SpgV0/femmx/manual_qt/images/dlg_materials_library.png

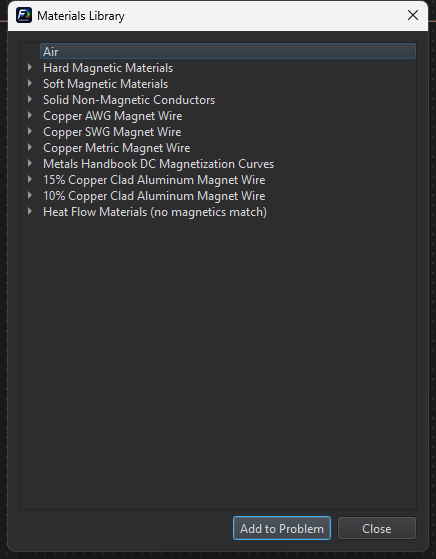
manual_qt/images/dlg_materials_library.png
