SpgV0/femmx/manual_qt/images/dlg_materials_list.png

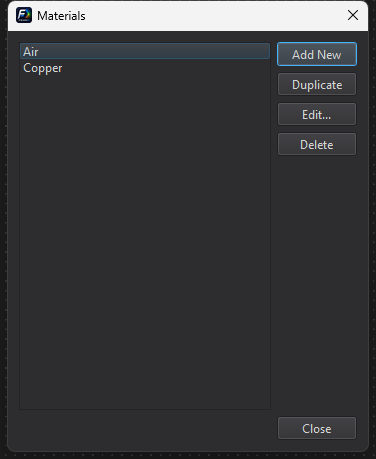
manual_qt/images/dlg_materials_list.png
