SpgV0/femmx/manual_qt/images/dlg_add_arc_prompt.png

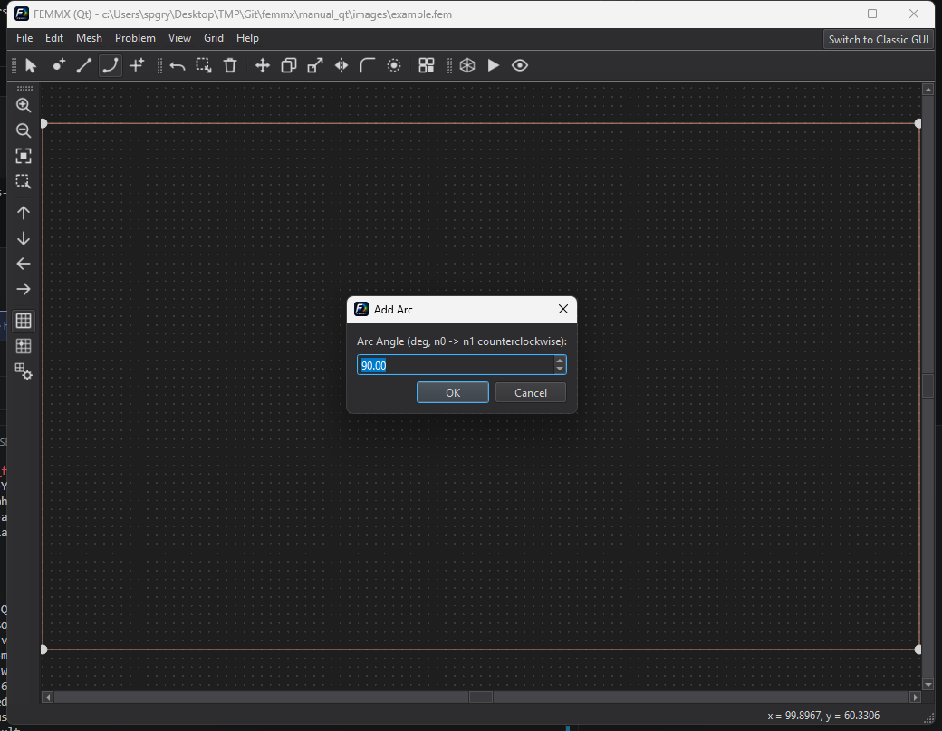
manual_qt/images/dlg_add_arc_prompt.png
