SpgV0/femmx/manual_qt/images/dlg_circuit_edit.png

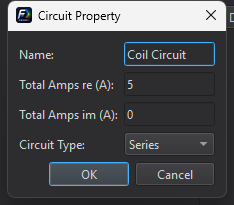
manual_qt/images/dlg_circuit_edit.png
