SpgV0/femmx/manual_qt/images/dlg_exterior_region.png

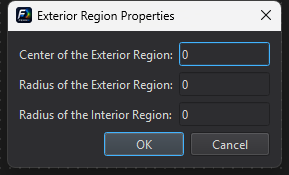
manual_qt/images/dlg_exterior_region.png
