SpgV0/femmx/manual_qt/images/dlg_heat_boundary_edit_filled.png

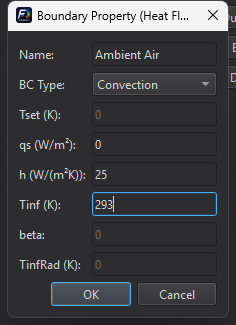
manual_qt/images/dlg_heat_boundary_edit_filled.png
