SpgV0/femmx/manual_qt/images/dlg_heat_boundary_list.png

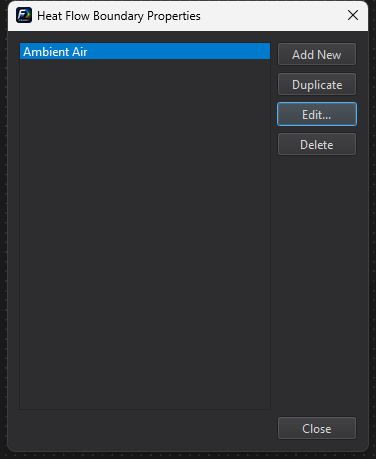
manual_qt/images/dlg_heat_boundary_list.png
