SpgV0/femmx/manual_qt/images/dlg_heat_point_edit.png

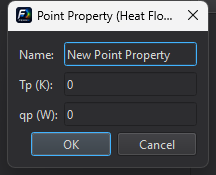
manual_qt/images/dlg_heat_point_edit.png
