SpgV0/femmx/manual_qt/images/dlg_node_props.png

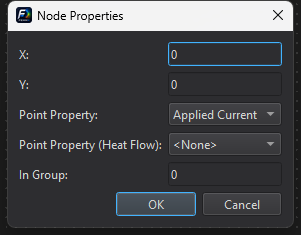
manual_qt/images/dlg_node_props.png
