SpgV0/femmx/manual_qt/images/dlg_pointprop_edit.png

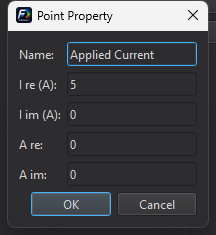
manual_qt/images/dlg_pointprop_edit.png
