SpgV0/femmx/manual_qt/images/menu_grid.png

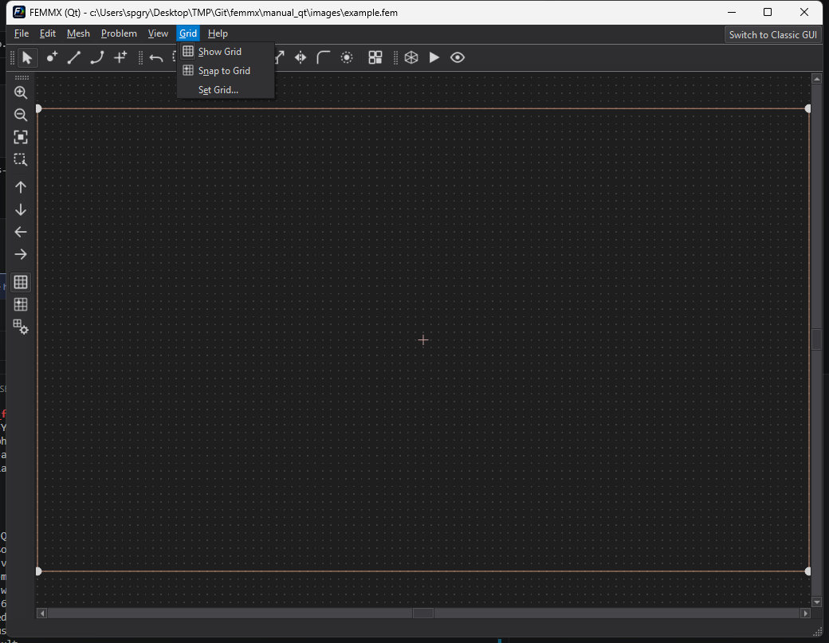
manual_qt/images/menu_grid.png
