SpgV0/femmx/manual_qt/images/menu_view.png

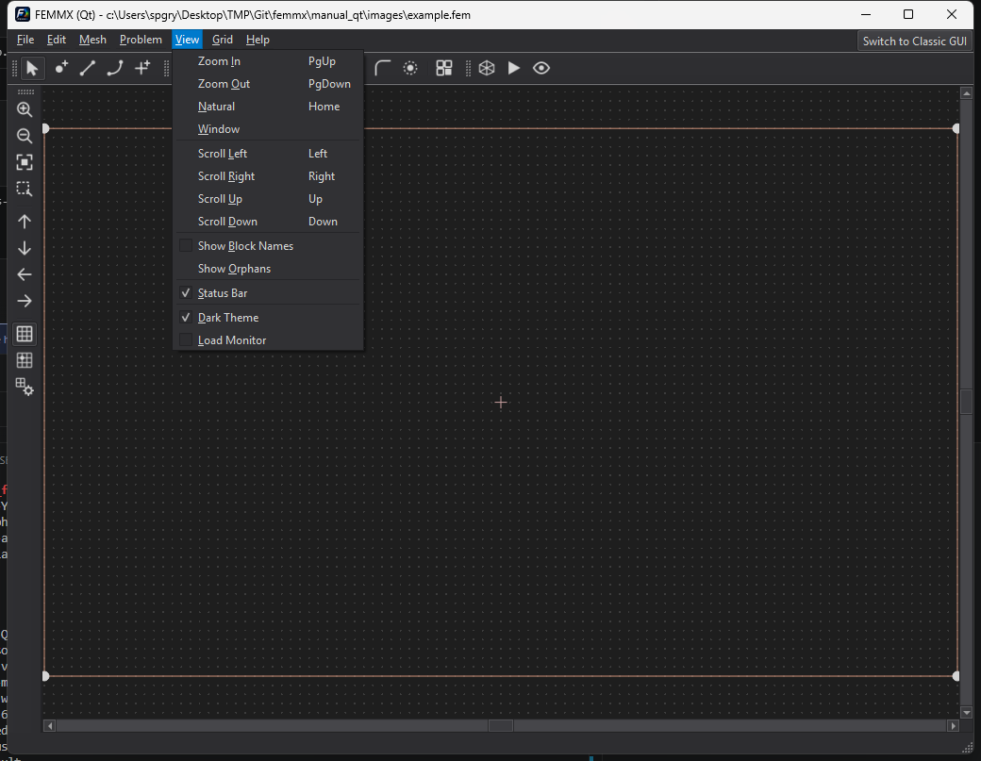
manual_qt/images/menu_view.png
