SpgV0/femmx/manual_qt/images/sv_menu_file.png

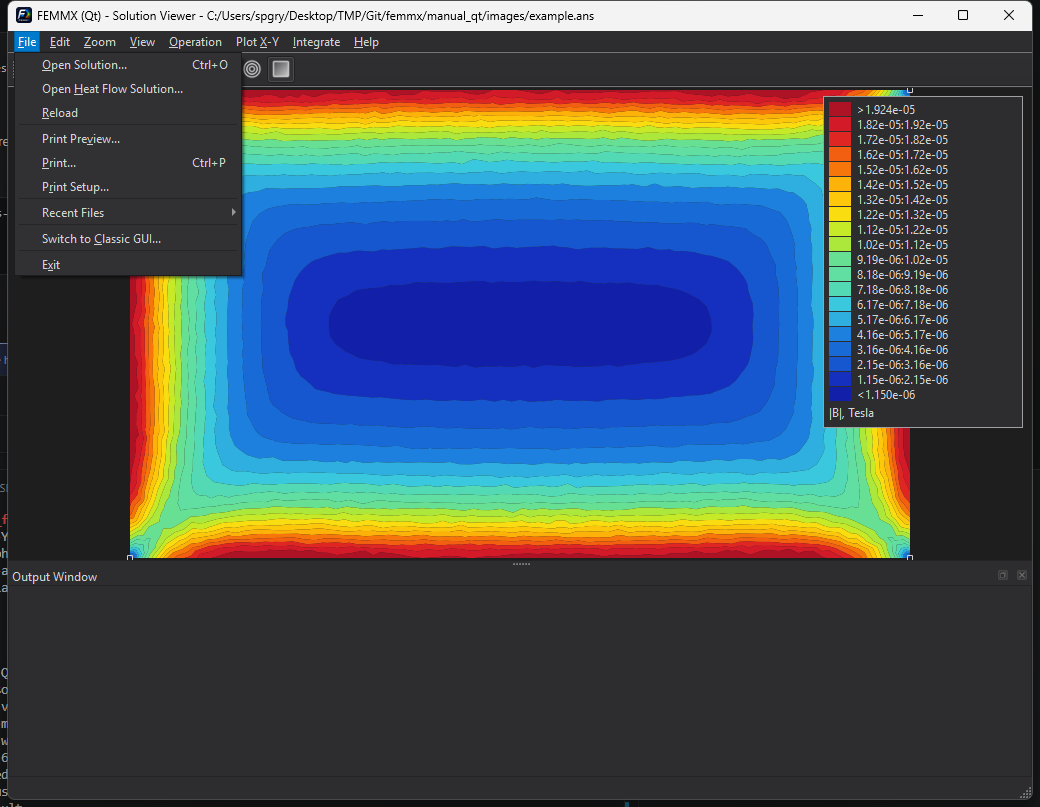
manual_qt/images/sv_menu_file.png
