SpgV0/femmx/manual_qt/images/sv_menu_operation.png

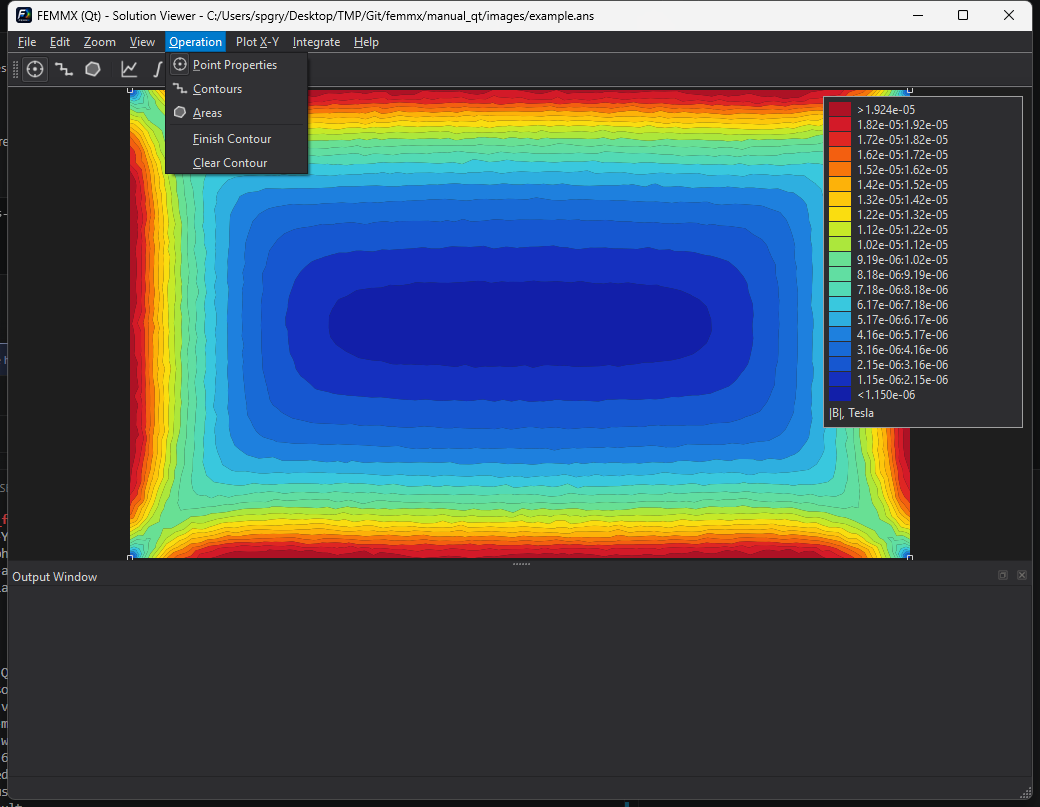
manual_qt/images/sv_menu_operation.png
