SpgV0/femmx/manual_qt/images/sv_plotxy_chart2.png

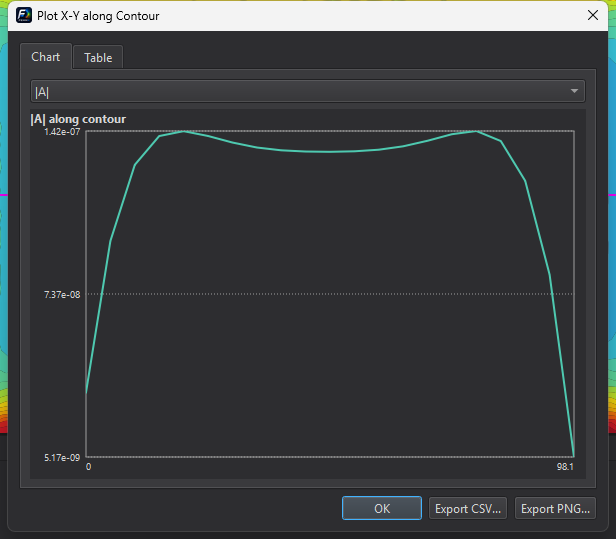
manual_qt/images/sv_plotxy_chart2.png
