SpgV0/femmx/manual_qt/images/view_loadmonitor_check.png

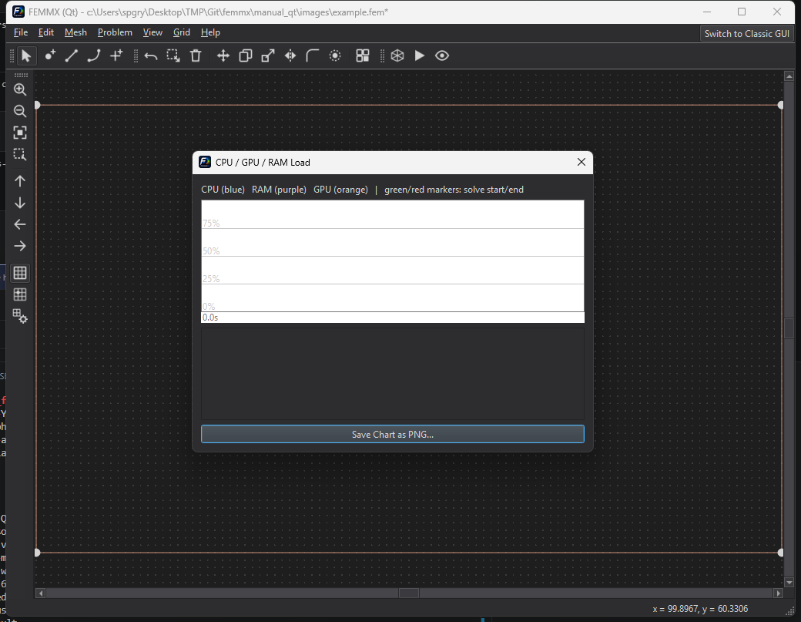
manual_qt/images/view_loadmonitor_check.png
