SpgV0/femmx/test/fixtures/render/golden/contour.png

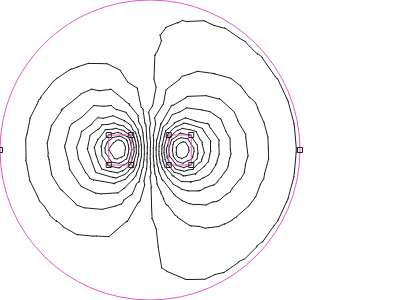
test/fixtures/render/golden/contour.png
