SpgV0/femmx/test/fixtures/render/golden/crop_density.png

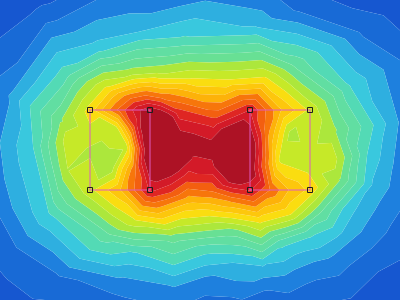
test/fixtures/render/golden/crop_density.png
