SpgV0/femmx/test/fixtures/render/golden/density.png

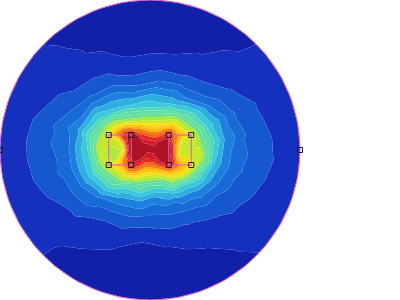
test/fixtures/render/golden/density.png
