SpgV0/femmx/test/fixtures/render/golden/geometry.png

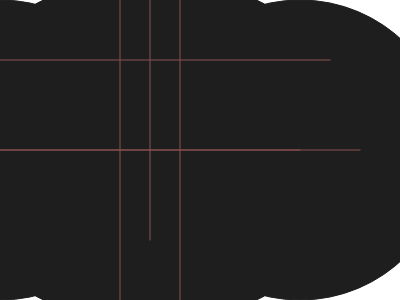
test/fixtures/render/golden/geometry.png
