SpgV0/femmx/manual_qt/images/dlg_problem_properties.png

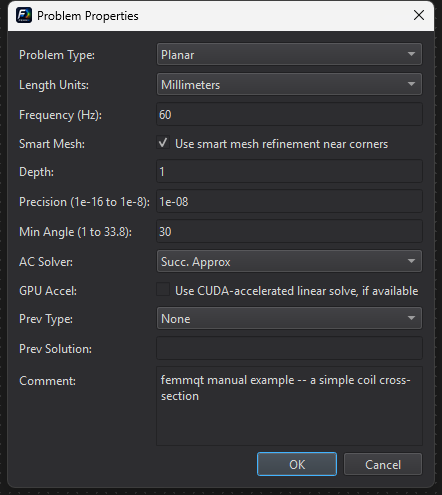
manual_qt/images/dlg_problem_properties.png
