SpgV0/femmx/femmqt/MainWindow.cpp

#define _USE_MATH_DEFINES

#include "MainWindow.h"

#include "AnsFileIO.h"
#include "AppPreferences.h"
#include "AppTheme.h"
#include "ArcPropDialog.h"
#include "BlockLabelPropDialog.h"
#include "BoundaryPropDialog.h"
#include "CircuitPropDialog.h"
#include "ConstraintListDialog.h"
#include "ConstraintSolver.h"
#include "DxfIO.h"
#include "ExteriorRegionDialog.h"
#include "FemmFileIO.h"
#include "FemmProblemEdit.h"
#include "FemxFileIO.h"
#include "SketchFileIO.h"
#include "GuiSwitch.h"
#include "HoverTooltip.h"
#include "IconTheme.h"
#include "LoadMonitorDialog.h"
#include "MaterialLibraryDialog.h"
#include "MaterialPropDialog.h"
#include "MeshOverlay.h"
#include "MoveCopyDialog.h"
#include "NodePropDialog.h"
#include "ConstructionGeometry.h"
#include "OffsetChamfer.h"
#include "ProblemFileIO.h"
#include "ProblemKind.h"
#include "OpenBoundaryDialog.h"
#include "PointPropDialog.h"
#include "PreferencesDialog.h"
#include "ProblemPropertiesDialog.h"
#include "PropertyEditDialog.h"
#include "PropertyFields.h"
#include "PropertyListDialog.h"
#include "SegmentPropDialog.h"
#include "SolutionView.h"
#include "SolveRunner.h"

#include <QActionGroup>
#include <QApplication>
#include <QClipboard>
#include <QCloseEvent>
#include <QComboBox>
#include <QDesktopServices>
#include <QDialog>
#include <QDialogButtonBox>
#include <QDoubleValidator>
#include <QFile>
#include <QFileDialog>
#include <QFileInfo>
#include <QFormLayout>
#include <QGraphicsView>
#include <QInputDialog>
#include <QLabel>
#include <QLineEdit>
#include <QMenuBar>
#include <QMessageBox>

#include "DemoBrowserDialog.h"
#include "DemoLibrary.h"
#include "Notify.h"
#include "WindowTitle.h"
#include <QPageSetupDialog>
#include <QPainter>
#include <QPlainTextEdit>
#include <QPrintDialog>
#include <QPrintPreviewDialog>
#include <QPrinter>
#include <QPushButton>
#include <QScrollArea>
#include <QScrollBar>
#include <QSet>
#include <QSettings>
#include <QSpinBox>
#include <QStatusBar>
#include <QToolBar>
#include <QUrl>
#include <QVBoxLayout>

#include <cmath>

namespace {
// Generates "New <Base>"/"<Base> Copy", disambiguated with a trailing
// " (2)", " (3)", ... against whatever names are already in `list` --
// shared by the Add New / Duplicate callbacks below for all four
// property lists (they're otherwise unrelated struct types, but all
// start with a QString `name` member, so this only needs to be a small
// template rather than four near-identical copies).
template <typename T>
QString uniqueName(const QVector<T>& list, const QString& base)
{
  QSet<QString> existing;
  for (const T& item : list)
    existing.insert(item.name);
  if (!existing.contains(base))
    return base;
  for (int n = 2;; n++) {
    QString candidate = QString("%1 (%2)").arg(base).arg(n);
    if (!existing.contains(candidate))
      return candidate;
  }
}

// Modified by Claude (Anthropic), noreply@anthropic.com: human-readable
// label for ConstraintListDialog -- names the type plus the node indices
// it touches, via ConstraintSolver::touchedNodes (the same node set the
// solver itself scopes its unknowns to -- see that function's own
// comment), rather than duplicating each type's own refA/refB/refC field
// semantics here.
QString constraintTypeName(ConstraintType type)
{
  switch (type) {
  case ConstraintType::Coincident: return "Coincident";
  case ConstraintType::Horizontal: return "Horizontal";
  case ConstraintType::Vertical: return "Vertical";
  case ConstraintType::Parallel: return "Parallel";
  case ConstraintType::Perpendicular: return "Perpendicular";
  case ConstraintType::Equal: return "Equal";
  case ConstraintType::Tangent: return "Tangent";
  case ConstraintType::Concentric: return "Concentric";
  case ConstraintType::Symmetric: return "Symmetric";
  }
  return "?";
}

QString describeConstraint(const FemmProblem& p, const FemmConstraint& c)
{
  const QVector<int> nodes = ConstraintSolver::touchedNodes(p, c);
  QStringList nodeStrs;
  for (int n : nodes)
    nodeStrs << QString::number(n);
  return QString("%1 (nodes %2)").arg(constraintTypeName(c.type)).arg(nodeStrs.join(", "));
}

// Matches ProblemPropertiesDialog.cpp's m_lengthUnits combo text exactly
// (same enum order), reused here so the Set Grid dialog's units label
// reads the same word the user already picked in Problem Properties.
QString lengthUnitsName(FemmLengthUnits u)
{
  switch (u) {
  case FemmLengthUnits::Inches: return "Inches";
  case FemmLengthUnits::Millimeters: return "Millimeters";
  case FemmLengthUnits::Centimeters: return "Centimeters";
  case FemmLengthUnits::Meters: return "Meters";
  case FemmLengthUnits::Mils: return "Mils";
  case FemmLengthUnits::Microns: return "Microns";
  }
  return QString();
}

// Per direct user request: right after a freshly-opened file's initial
// Natural/fit-to-view zoom, pick a grid spacing so roughly 20 squares
// span the x axis, snapped to a "nice" whole-number step (1/2/5 x a
// power of ten -- the same progression axis tick marks conventionally
// use) rather than an arbitrary fraction. Takes the ACTUAL visible scene
// width, not the raw model bounding box -- for anything other than a
// model whose own aspect ratio matches the viewport's, fitInViewSafe's
// Qt::KeepAspectRatio padding means more of the x axis is visible than
// just the model's own width (confirmed live: a 50x200mm model in a
// ~985x730px window shows ~295mm of scene width, not 50mm -- using the
// model's width alone would have produced a ~150-square-wide grid, not
// ~20). Callers pass view->mapToScene(view->viewport()->rect()).
// boundingRect(), taken AFTER fitInViewSafe so it reflects what actually
// ended up on screen. Bottoms out at 1 (a true integer, per the original
// request this was built for) for any view whose width is itself under
// ~20 units -- a sub-1 step would technically hit the "~20 squares"
// target more precisely there, but wouldn't be a whole number anymore.
double niceIntegerGridSize(const QRectF& visibleBounds)
{
  double extent = visibleBounds.width();
  if (extent <= 0)
    return 1.0;
  double target = extent / 20.0;
  if (target < 1.0)
    return 1.0;
  double magnitude = std::pow(10.0, std::floor(std::log10(target)));
  double normalized = target / magnitude;
  double nice;
  if (normalized < 1.5)
    nice = 1;
  else if (normalized < 3.5)
    nice = 2;
  else if (normalized < 7.5)
    nice = 5;
  else
    nice = 10;
  return nice * magnitude;
}
}

MainWindow::MainWindow(QWidget* parent)
    : QMainWindow(parent)
{
  resize(1024, 768);

  m_scene = new GeometryScene(this);
  m_scene->setProblem(&m_problem);
  // #28: honour the saved per-type snap choices from the first window
  // onwards, not just after Preferences has been opened once.
  m_scene->setSnapFlags(AppPreferences::load().snapFlags);
  connect(m_scene, &GeometryScene::problemEdited, this, &MainWindow::onProblemEdited);
  connect(m_scene, &GeometryScene::entityDoubleClicked, this, &MainWindow::onEntityDoubleClicked);
  connect(m_scene, &GeometryScene::openSelectedRequested, this, &MainWindow::onOpenSelectedTriggered);
  connect(m_scene, &GeometryScene::zoomWindowSelected, this, &MainWindow::onZoomWindowSelected);
  connect(m_scene, &GeometryScene::selectByCircleCompleted, this, [this]() { m_selectToolAction->setChecked(true); });
  connect(m_scene, &GeometryScene::aboutToEdit, this, &MainWindow::snapshotForUndo);

  m_view = new GeometryView(m_scene, this);
  m_view->setRenderHint(QPainter::Antialiasing);
  m_view->setDragMode(QGraphicsView::RubberBandDrag);
  // FEMM's geometry files use a math (y-up) convention, matching how
  // femmx.exe itself draws (see FemmeView.cpp's DwgToScreen, which flips
  // y explicitly for GDI's y-down screen space) -- flip the view instead
  // of the data, so GeometryScene's coordinates can stay exactly what's
  // in the .fem file with no transform bookkeeping of its own.
  m_view->scale(1, -1);
  setCentralWidget(m_view);
  connect(m_view, &GeometryView::enterPointRequested, this, &MainWindow::onEnterPointTriggered);

  QMenu* fileMenu = menuBar()->addMenu("&File");
  fileMenu->addAction("&New", this, &MainWindow::onNewTriggered, QKeySequence::New);
  fileMenu->addAction("&Open...", this, &MainWindow::onOpenTriggered, QKeySequence::Open);
  fileMenu->addAction("&Save", this, &MainWindow::onSaveTriggered, QKeySequence::Save);
  fileMenu->addAction("Save &As...", this, &MainWindow::onSaveAsTriggered, QKeySequence::SaveAs);
  fileMenu->addSeparator();
  fileMenu->addAction("&Import DXF...", this, &MainWindow::onImportDxfTriggered);
  fileMenu->addAction("&Export DXF...", this, &MainWindow::onExportDxfTriggered);
  fileMenu->addSeparator();
  fileMenu->addAction("Print Pre&view...", this, &MainWindow::onPrintPreviewTriggered);
  fileMenu->addAction("&Print...", this, &MainWindow::onPrintTriggered, QKeySequence::Print);
  fileMenu->addAction("P&rint Setup...", this, &MainWindow::onPrintSetupTriggered);
  fileMenu->addSeparator();
  // Issue #90: the shipped demo library. Disabled rather than hidden
  // when there is none, so a build without the corpus says why instead
  // of quietly having one fewer menu item -- and disabled rather than
  // reporting: a missing demo library is not something the user did,
  // and an error dialog at startup would be a modal on a path that may
  // have no desktop (#85).
  m_demoModelsAction = fileMenu->addAction("&Demo Models...", this,
      &MainWindow::onDemoModelsTriggered);
  {
    QString demoError;
    const int count = DemoLibrary::load(demoError).size();
    if (count == 0) {
      m_demoModelsAction->setEnabled(false);
      m_demoModelsAction->setToolTip(
          QStringLiteral("No demo models are installed: %1").arg(demoError));
    } else {
      m_demoModelsAction->setToolTip(
          QStringLiteral("%1 worked examples, each with a closed-form answer to "
                         "check against").arg(count));
    }
  }
  fileMenu->addSeparator();
  m_recentFilesMenu = fileMenu->addMenu("Recent Files");
  fileMenu->addSeparator();
  fileMenu->addAction("Switch to &Classic GUI...", this, &MainWindow::onSwitchToClassicTriggered);
  fileMenu->addSeparator();
  fileMenu->addAction("E&xit", this, &QWidget::close);

  // Matches femm.rc's IDR_FEMMETYPE Edit menu.
  QMenu* editMenu = menuBar()->addMenu("&Edit");
  editMenu->addAction("&Undo", this, &MainWindow::onUndoTriggered, QKeySequence::Undo);
  editMenu->addAction("&Open Selected", this, &MainWindow::onOpenSelectedTriggered);
  editMenu->addAction("&Delete", this, &MainWindow::onDeleteSelectedTriggered, QKeySequence::Delete);
  editMenu->addSeparator();
  editMenu->addAction("&Move...", this, &MainWindow::onMoveSelectedTriggered);
  editMenu->addAction("&Copy...", this, &MainWindow::onCopySelectedTriggered);
  editMenu->addAction("Sc&ale...", this, &MainWindow::onScaleSelectedTriggered);
  editMenu->addAction("M&irror...", this, &MainWindow::onMirrorSelectedTriggered);
  editMenu->addSeparator();
  editMenu->addAction("Create &Radius...", this, &MainWindow::onCreateRadiusTriggered);
  editMenu->addAction("Create &Open Boundary...", this, &MainWindow::onCreateOpenBoundaryTriggered);
  editMenu->addSeparator();
  editMenu->addAction("Copy as &Bitmap", this, &MainWindow::onCopyBitmapTriggered);
  editMenu->addSeparator();
  // Simplified, instant-action equivalent of femm.rc's "Operation > Group"
  // mode (which requires switching modes, then pressing Tab to prompt for
  // a group number) -- same underlying inGroup field, just two direct
  // commands instead of a persistent tool mode.
  editMenu->addAction("Select by &Group...", this, &MainWindow::onSelectByGroupTriggered);
  editMenu->addAction("Set &Group...", this, &MainWindow::onSetGroupTriggered);
  editMenu->addSeparator();
  editMenu->addAction("&Preferences...", this, &MainWindow::onPreferencesTriggered);

  // Modified by Claude (Anthropic), noreply@anthropic.com: menu-based
  // access to the drawing tools -- per direct user request ("I want a
  // tools tab for the drawing tools similar to constraints tab"). Until
  // now these existed ONLY as Draw-toolbar buttons with no menu entry
  // (see the toolbar-construction code below, where the still-checkable
  // QActions actually get created). Populated a bit further down, once
  // those QActions exist -- reuses the exact same QAction objects
  // (already checkable, already in the shared `toolGroup` QActionGroup)
  // rather than duplicating them, so a menu selection and a toolbar
  // click stay in sync for free, with no extra wiring.
  QMenu* toolsMenu = menuBar()->addMenu("&Tools");

  // Modified by Claude (Anthropic), noreply@anthropic.com: CAD-style
  // geometric constraints -- per direct user request ("add dimensions
  // when drawings and constraints similar to modern cad"). No classic
  // FEMM precedent (see FemmProblem.h's FemmConstraint comment) -- select
  // the entities a constraint type needs first (same selection mechanism
  // as Move/Copy/Scale/Mirror above), then apply it here.
  QMenu* constraintsMenu = menuBar()->addMenu("&Constraints");
  constraintsMenu->addAction("&Coincident", this, &MainWindow::onCoincidentConstraintTriggered);
  constraintsMenu->addAction("&Horizontal", this, &MainWindow::onHorizontalConstraintTriggered);
  constraintsMenu->addAction("&Vertical", this, &MainWindow::onVerticalConstraintTriggered);
  constraintsMenu->addAction("&Parallel", this, &MainWindow::onParallelConstraintTriggered);
  constraintsMenu->addAction("Perpe&ndicular", this, &MainWindow::onPerpendicularConstraintTriggered);
  constraintsMenu->addAction("&Equal", this, &MainWindow::onEqualConstraintTriggered);
  constraintsMenu->addAction("&Tangent", this, &MainWindow::onTangentConstraintTriggered);
  constraintsMenu->addAction("Co&ncentric", this, &MainWindow::onConcentricConstraintTriggered);
  constraintsMenu->addAction("&Symmetric", this, &MainWindow::onSymmetricConstraintTriggered);
  constraintsMenu->addSeparator();
  constraintsMenu->addAction("&Solve Constraints", this, &MainWindow::onSolveConstraintsTriggered);
  constraintsMenu->addAction("Constraint &List...", this, &MainWindow::onConstraintListTriggered);
  constraintsMenu->addSeparator();
  constraintsMenu->addAction("Clear All Constraints", this, &MainWindow::onClearConstraintsTriggered);
  constraintsMenu->addAction("Clear All Dimensions", this, &MainWindow::onClearDimensionsTriggered);

  // Matches femm.rc's separate Mesh (Create/Show/Purge) and Analysis
  // (Analyze/View Results) menus, just combined under one "Mesh" menu
  // rather than two -- Create Mesh alone (no solve) lets a mesh be
  // inspected/refined before committing to a full Solve.
  QMenu* meshMenu = menuBar()->addMenu("&Mesh");
  meshMenu->addAction("&Create Mesh", this, &MainWindow::onCreateMeshTriggered);
  m_showMeshAction = meshMenu->addAction("&Show Mesh");
  m_showMeshAction->setCheckable(true);
  connect(m_showMeshAction, &QAction::toggled, m_scene, &GeometryScene::setShowMesh);
  meshMenu->addAction("&Purge Mesh", this, &MainWindow::onPurgeMeshTriggered);
  meshMenu->addSeparator();
  meshMenu->addAction("&Solve", this, &MainWindow::onSolveTriggered, QKeySequence("Ctrl+L"));
  meshMenu->addAction("&View Results...", this, &MainWindow::onViewResultsTriggered);

  QMenu* problemMenu = menuBar()->addMenu("&Problem");
  problemMenu->addAction("&Problem Properties...", this, &MainWindow::onProblemPropertiesTriggered);
  problemMenu->addAction("&Exterior Region...", this, &MainWindow::onExteriorRegionTriggered);
  problemMenu->addSeparator();
  problemMenu->addAction("&Materials...", this, &MainWindow::onMaterialsTriggered);
  problemMenu->addAction("Materials &Library...", this, &MainWindow::onMaterialsLibraryTriggered);
  problemMenu->addAction("&Boundary Properties...", this, &MainWindow::onBoundaryPropsTriggered);
  problemMenu->addAction("&Circuits...", this, &MainWindow::onCircuitsTriggered);
  problemMenu->addAction("Poi&nt Properties...", this, &MainWindow::onPointPropsTriggered);

  // Matches femm.rc's IDR_FEMMETYPE View menu (Zoom/Pan/Show Block Names
  // subset), plus Dark Theme and the Load Monitor -- Lua Console is a
  // separate todo item (see the plan's scope note on it).
  QMenu* viewMenu = menuBar()->addMenu("&View");
  viewMenu->addAction("Zoom &In", this, &MainWindow::onZoomIn, QKeySequence(Qt::Key_PageUp));
  viewMenu->addAction("Zoom &Out", this, &MainWindow::onZoomOut, QKeySequence(Qt::Key_PageDown));
  viewMenu->addAction("&Natural", this, &MainWindow::onZoomNatural, QKeySequence(Qt::Key_Home));
  viewMenu->addAction("&Window", this, &MainWindow::onZoomWindowTriggered);
  viewMenu->addAction("&Keyboard", this, &MainWindow::onKbdZoomTriggered);
  viewMenu->addSeparator();
  viewMenu->addAction("Scroll &Left", this, &MainWindow::onPanLeft, QKeySequence(Qt::Key_Left));
  viewMenu->addAction("Scroll &Right", this, &MainWindow::onPanRight, QKeySequence(Qt::Key_Right));
  viewMenu->addAction("Scroll &Up", this, &MainWindow::onPanUp, QKeySequence(Qt::Key_Up));
  viewMenu->addAction("Scroll &Down", this, &MainWindow::onPanDown, QKeySequence(Qt::Key_Down));
  viewMenu->addSeparator();
  QAction* showNamesAction = viewMenu->addAction("Show &Block Names");
  showNamesAction->setCheckable(true);
  connect(showNamesAction, &QAction::toggled, m_scene, &GeometryScene::setShowBlockNames);
  viewMenu->addAction("Show &Orphans", this, &MainWindow::onShowOrphansTriggered);
  viewMenu->addSeparator();
  QAction* statusBarAction = viewMenu->addAction("&Status Bar");
  statusBarAction->setCheckable(true);
  statusBarAction->setChecked(true);
  connect(statusBarAction, &QAction::toggled, statusBar(), &QStatusBar::setVisible);
  viewMenu->addSeparator();
  QAction* darkThemeAction = viewMenu->addAction("&Dark Theme");
  darkThemeAction->setCheckable(true);
  darkThemeAction->setChecked(AppTheme::isDark());
  connect(darkThemeAction, &QAction::toggled, this, &MainWindow::onDarkThemeToggled);
  QAction* loadMonitorAction = viewMenu->addAction("&Load Monitor");
  loadMonitorAction->setCheckable(true);
  connect(loadMonitorAction, &QAction::toggled, this, &MainWindow::onLoadMonitorToggled);

  QMenu* gridMenu = menuBar()->addMenu("&Grid");
  QAction* showGridAction = gridMenu->addAction("&Show Grid");
  showGridAction->setCheckable(true);
  showGridAction->setChecked(m_scene->showGrid());
  connect(showGridAction, &QAction::toggled, m_scene, &GeometryScene::setShowGrid);
  QAction* snapGridAction = gridMenu->addAction("S&nap to Grid");
  snapGridAction->setCheckable(true);
  snapGridAction->setChecked(m_scene->snapToGrid());
  connect(snapGridAction, &QAction::toggled, m_scene, &GeometryScene::setSnapToGrid);
  gridMenu->addAction("S&et Grid...", this, &MainWindow::onSetGridTriggered);

  QMenu* helpMenu = menuBar()->addMenu("&Help");
  helpMenu->addAction("&Help Topics", this, &MainWindow::onHelpTopicsTriggered);
  helpMenu->addAction("&Keyboard Shortcuts...", this, &MainWindow::onKeyboardShortcutsTriggered);
  helpMenu->addSeparator();
  helpMenu->addAction("&License", this, &MainWindow::onLicenseTriggered);
  helpMenu->addAction("&About FEMMX...", this, &MainWindow::onAboutTriggered);

  // Distinct, always-visible button for jumping back to the classic MFC
  // GUI, per direct user request -- the toolbars above are deliberately
  // icon-only (see their own comment), so "Switch to Classic GUI" living
  // only as a File-menu item was easy to miss. Pinned to the menu bar's
  // corner so it stays visible regardless of window size, not swallowed
  // into an overflow chevron the way a toolbar button could be.
  auto* switchToClassicButton = new QPushButton("Switch to Classic GUI", this);
  switchToClassicButton->setToolTip("Close this file here and reopen it in the original FEMM interface");
  connect(switchToClassicButton, &QPushButton::clicked, this, &MainWindow::onSwitchToClassicTriggered);
  menuBar()->setCornerWidget(switchToClassicButton, Qt::TopRightCorner);

  updateRecentFilesMenu();

  QToolBar* toolBar = addToolBar("Draw");
  // Icon-only, matching a modern CAD-style toolbar -- each action keeps
  // its descriptive text (set below) as a tooltip and for the
  // accessibility/menu fallback, it just isn't painted next to the icon.
  toolBar->setToolButtonStyle(Qt::ToolButtonIconOnly);
  toolBar->setIconSize(QSize(20, 20));
  auto* toolGroup = new QActionGroup(this);
  toolGroup->setExclusive(true);

  m_selectToolAction = addThemedToolAction(toolBar, ":/icons/select.svg", "Select");
  m_selectToolAction->setToolTip("Select -- click or rubber-band-select existing geometry to edit it");
  m_selectToolAction->setCheckable(true);
  m_selectToolAction->setChecked(true);
  toolGroup->addAction(m_selectToolAction);
  connect(m_selectToolAction, &QAction::triggered, this, [this]() { m_scene->setToolMode(GeometryToolMode::Select); });

  m_addNodeToolAction = addThemedToolAction(toolBar, ":/icons/add_node.svg", "Add Node");
  m_addNodeToolAction->setToolTip("Add Node -- click to place a new node");
  m_addNodeToolAction->setCheckable(true);
  // Single-key tool shortcut, per direct user request for CAD-style
  // keys ("n for node, l for line, c for circle, r for rectangle").
  // setShortcut, not just a menu mnemonic, so the bare key works
  // whenever the canvas has focus. Matches the Smart Dimension "D"
  // precedent below; none of these collide with an existing binding.
  m_addNodeToolAction->setShortcut(QKeySequence(Qt::Key_N));
  toolGroup->addAction(m_addNodeToolAction);
  connect(m_addNodeToolAction, &QAction::triggered, this, [this]() { m_scene->setToolMode(GeometryToolMode::AddNode); });

  m_addSegmentToolAction = addThemedToolAction(toolBar, ":/icons/add_segment.svg", "Add Segment");
  m_addSegmentToolAction->setToolTip("Add Segment -- click two nodes to connect them with a straight line");
  m_addSegmentToolAction->setCheckable(true);
  // Single-key tool shortcut, per direct user request for CAD-style
  // keys ("n for node, l for line, c for circle, r for rectangle").
  // setShortcut, not just a menu mnemonic, so the bare key works
  // whenever the canvas has focus. Matches the Smart Dimension "D"
  // precedent below; none of these collide with an existing binding.
  m_addSegmentToolAction->setShortcut(QKeySequence(Qt::Key_L));
  toolGroup->addAction(m_addSegmentToolAction);
  connect(m_addSegmentToolAction, &QAction::triggered, this, [this]() { m_scene->setToolMode(GeometryToolMode::AddSegment); });

  m_addArcToolAction = addThemedToolAction(toolBar, ":/icons/add_arc.svg", "Add Arc");
  m_addArcToolAction->setToolTip("Add Arc -- click two nodes to connect them with a circular arc");
  m_addArcToolAction->setCheckable(true);
  // Single-key tool shortcut, per direct user request for CAD-style
  // keys ("n for node, l for line, c for circle, r for rectangle").
  // setShortcut, not just a menu mnemonic, so the bare key works
  // whenever the canvas has focus. Matches the Smart Dimension "D"
  // precedent below; none of these collide with an existing binding.
  m_addArcToolAction->setShortcut(QKeySequence(Qt::Key_A));
  toolGroup->addAction(m_addArcToolAction);
  connect(m_addArcToolAction, &QAction::triggered, this, [this]() { m_scene->setToolMode(GeometryToolMode::AddArc); });

  m_addBlockLabelToolAction = addThemedToolAction(toolBar, ":/icons/add_block_label.svg", "Add Block Label");
  m_addBlockLabelToolAction->setToolTip("Add Block Label -- click to mark a region and assign it a material");
  m_addBlockLabelToolAction->setCheckable(true);
  toolGroup->addAction(m_addBlockLabelToolAction);
  connect(m_addBlockLabelToolAction, &QAction::triggered, this, [this]() { m_scene->setToolMode(GeometryToolMode::AddBlockLabel); });

  // Per direct user request -- no classic FEMM precedent (see the enum's
  // own comment), a new CAD-style convenience: drag out a rectangle/circle
  // in one gesture instead of placing each node and connecting segment/
  // arc by hand.
  m_addRectangleToolAction = addThemedToolAction(toolBar, ":/icons/add_rectangle.svg", "Draw Rectangle");
  m_addRectangleToolAction->setToolTip("Draw Rectangle -- drag between two diagonal corners");
  m_addRectangleToolAction->setCheckable(true);
  // Single-key tool shortcut, per direct user request for CAD-style
  // keys ("n for node, l for line, c for circle, r for rectangle").
  // setShortcut, not just a menu mnemonic, so the bare key works
  // whenever the canvas has focus. Matches the Smart Dimension "D"
  // precedent below; none of these collide with an existing binding.
  m_addRectangleToolAction->setShortcut(QKeySequence(Qt::Key_R));
  toolGroup->addAction(m_addRectangleToolAction);
  connect(m_addRectangleToolAction, &QAction::triggered, this, [this]() { m_scene->setToolMode(GeometryToolMode::DrawRectangle); });

  m_addCircleToolAction = addThemedToolAction(toolBar, ":/icons/add_circle.svg", "Draw Circle");
  m_addCircleToolAction->setToolTip("Draw Circle -- drag from the center out to the perimeter");
  m_addCircleToolAction->setCheckable(true);
  // Single-key tool shortcut, per direct user request for CAD-style
  // keys ("n for node, l for line, c for circle, r for rectangle").
  // setShortcut, not just a menu mnemonic, so the bare key works
  // whenever the canvas has focus. Matches the Smart Dimension "D"
  // precedent below; none of these collide with an existing binding.
  m_addCircleToolAction->setShortcut(QKeySequence(Qt::Key_C));
  toolGroup->addAction(m_addCircleToolAction);
  connect(m_addCircleToolAction, &QAction::triggered, this, [this]() { m_scene->setToolMode(GeometryToolMode::DrawCircle); });

  // Added by Claude (Anthropic), noreply@anthropic.com, 2026-09-12
  // (issue #29). These three MODIFY existing geometry, which is the
  // category femmqt was missing entirely -- it could add and it could
  // delete, so the only way to shorten a line was to delete it and draw
  // it again, which is where stray fragments and near-miss junctions
  // come from.
  //
  // Grouped behind their own separator for that reason: they are a
  // different kind of operation from everything to their left, and the
  // click means something different (it picks a PIECE, not a position).
  toolBar->addSeparator();

  m_trimToolAction = addThemedToolAction(toolBar, ":/icons/trim.svg", "Trim");
  m_trimToolAction->setToolTip("Trim -- click the piece of a line or arc to remove. "
                               "The piece runs to the nearest crossing on each side; "
                               "with nothing crossing it, the whole entity goes.");
  m_trimToolAction->setCheckable(true);
  // T, matching the single-key CAD-style bindings the tools to the left
  // already use (N/L/A/R/C/D). Free: nothing else binds it.
  m_trimToolAction->setShortcut(QKeySequence(Qt::Key_T));
  toolGroup->addAction(m_trimToolAction);
  connect(m_trimToolAction, &QAction::triggered, this, [this]() { m_scene->setToolMode(GeometryToolMode::Trim); });

  m_extendToolAction = addThemedToolAction(toolBar, ":/icons/extend.svg", "Extend");
  m_extendToolAction->setToolTip("Extend -- click near the end of a line or arc to grow it "
                                 "until it meets the next entity in its path.");
  m_extendToolAction->setCheckable(true);
  m_extendToolAction->setShortcut(QKeySequence(Qt::Key_E));
  toolGroup->addAction(m_extendToolAction);
  connect(m_extendToolAction, &QAction::triggered, this, [this]() { m_scene->setToolMode(GeometryToolMode::Extend); });

  m_splitToolAction = addThemedToolAction(toolBar, ":/icons/split.svg", "Split");
  m_splitToolAction->setToolTip("Split -- click a line or arc to cut it in two at that point, "
                                "moving nothing.");
  m_splitToolAction->setCheckable(true);
  // S is Save's modifier-less neighbour but not itself bound; K is what
  // Fusion uses for Break, and is free here too. S reads better next to
  // T and E, and Ctrl+S is unaffected.
  m_splitToolAction->setShortcut(QKeySequence(Qt::Key_S));
  toolGroup->addAction(m_splitToolAction);
  connect(m_splitToolAction, &QAction::triggered, this, [this]() { m_scene->setToolMode(GeometryToolMode::Split); });

  // Modified by Claude (Anthropic), noreply@anthropic.com: CAD-style
  // dimension tools -- per direct user request ("add dimensions when
  // drawings"). Also reachable from the Tools menu, like every other
  // drawing-tool button above -- see toolsMenu's population just below.
  toolBar->addSeparator();
  m_addDimensionDistanceToolAction = addThemedToolAction(toolBar, ":/icons/dimension_distance.svg", "Distance Dimension");
  m_addDimensionDistanceToolAction->setToolTip("Distance Dimension -- click two nodes, then enter the distance");
  m_addDimensionDistanceToolAction->setCheckable(true);
  toolGroup->addAction(m_addDimensionDistanceToolAction);
  connect(m_addDimensionDistanceToolAction, &QAction::triggered, this, [this]() { m_scene->setToolMode(GeometryToolMode::AddDimensionDistance); });

  m_addDimensionRadiusToolAction = addThemedToolAction(toolBar, ":/icons/dimension_radius.svg", "Radius Dimension");
  m_addDimensionRadiusToolAction->setToolTip("Radius Dimension -- click an arc, then enter the radius");
  m_addDimensionRadiusToolAction->setCheckable(true);
  toolGroup->addAction(m_addDimensionRadiusToolAction);
  connect(m_addDimensionRadiusToolAction, &QAction::triggered, this, [this]() { m_scene->setToolMode(GeometryToolMode::AddDimensionRadius); });

  m_addDimensionAngleToolAction = addThemedToolAction(toolBar, ":/icons/dimension_angle.svg", "Angle Dimension");
  m_addDimensionAngleToolAction->setToolTip("Angle Dimension -- click two lines, move to place, then type the angle. The lines need not touch.");
  m_addDimensionAngleToolAction->setCheckable(true);
  toolGroup->addAction(m_addDimensionAngleToolAction);
  // Modified by Claude (Anthropic), noreply@anthropic.com: per direct user
  // report that "the angle tool does not always work well", asking for
  // Fusion 360's behaviour -- this button now arms Smart Dimension rather
  // than the old AddDimensionAngle mode.
  //
  // The old mode responded ONLY to clicks on nodes, and needed three of
  // them in a fixed order (vertex first, then each ray end) with no
  // feedback about which stage you were in, then popped a modal dialog
  // immediately instead of the place-then-type step every other dimension
  // here uses. Clicking the lines you actually wanted to angle did
  // nothing at all.
  //
  // Fusion has no separate angle tool: Smart Dimension infers the kind of
  // dimension from what you pick, and two line picks mean an angle. That
  // path already existed here and is now general enough to be the whole
  // answer (see handleToolClick's SmartDimension case, which as of this
  // change also handles lines that never touch). AddDimensionAngle is
  // left in place for the 3-node form rather than deleted, since existing
  // .fem-adjacent workflows and the Tools menu still reference it.
  connect(m_addDimensionAngleToolAction, &QAction::triggered, this, [this]() { m_scene->setToolMode(GeometryToolMode::SmartDimension); });

  // Modified by Claude (Anthropic), noreply@anthropic.com: "Smart
  // Dimension" -- per direct user request ("I want to be able to set
  // dimension by pressing D and [click] the line or the nodes"), matching
  // SolidWorks/Fusion 360's own "D" shortcut. setShortcut (not just a
  // menu mnemonic) makes the bare "D" key work anywhere the canvas has
  // focus, not just while a menu is open -- confirmed no existing action
  // in this app already binds plain Key_D. See GeometryScene::
  // handleToolClick's SmartDimension case for the actual click dispatch
  // (segment -> Distance on its own 2 endpoints, arc -> Radius, node ->
  // 2-click Distance).
  m_smartDimensionToolAction = addThemedToolAction(toolBar, ":/icons/dimension_smart.svg", "Smart Dimension");
  m_smartDimensionToolAction->setToolTip("Smart Dimension (D) -- click a line for its length, an arc for its radius, or two nodes for the distance between them");
  m_smartDimensionToolAction->setCheckable(true);
  m_smartDimensionToolAction->setShortcut(QKeySequence(Qt::Key_D));
  toolGroup->addAction(m_smartDimensionToolAction);
  connect(m_smartDimensionToolAction, &QAction::triggered, this, [this]() { m_scene->setToolMode(GeometryToolMode::SmartDimension); });

  // toolsMenu (created earlier, alongside the Edit menu) populated here,
  // now that every tool QAction above actually exists -- same order as
  // the toolbar itself, so the menu reads as a straightforward list
  // version of it.
  toolsMenu->addAction(m_selectToolAction);
  toolsMenu->addAction(m_addNodeToolAction);
  toolsMenu->addAction(m_addSegmentToolAction);
  toolsMenu->addAction(m_addArcToolAction);
  toolsMenu->addAction(m_addBlockLabelToolAction);
  toolsMenu->addSeparator();
  toolsMenu->addAction(m_addRectangleToolAction);
  toolsMenu->addAction(m_addCircleToolAction);
  toolsMenu->addSeparator();
  toolsMenu->addAction(m_trimToolAction);
  toolsMenu->addAction(m_extendToolAction);
  toolsMenu->addAction(m_splitToolAction);

  // Added by Claude (Anthropic), noreply@anthropic.com, 2026-09-12
  // (issue #31). A submenu rather than five more toolbar buttons: these
  // are occasional, and the toolbar is already dense enough that #57's
  // missing icons went unnoticed until a user reported them.
  QMenu* constructionMenu = toolsMenu->addMenu("Construction Geometry");
  constructionMenu->setToolTipsVisible(true);
  QAction* toConstruction = constructionMenu->addAction("Convert Selection to Construction");
  toConstruction->setToolTip("Construction geometry is drawn dashed, is never meshed or "
                             "solved, and is not written to the .fem -- but constraints "
                             "and dimensions may reference it, which is the point of it.");
  connect(toConstruction, &QAction::triggered, this, [this]() { convertSelectionConstruction(true); });
  QAction* toReal = constructionMenu->addAction("Convert Selection to Real Geometry");
  connect(toReal, &QAction::triggered, this, [this]() { convertSelectionConstruction(false); });
  constructionMenu->addSeparator();
  connect(constructionMenu->addAction("Centreline..."), &QAction::triggered,
      this, &MainWindow::onAddCentrelineTriggered);
  connect(constructionMenu->addAction("Bolt Circle..."), &QAction::triggered,
      this, &MainWindow::onAddBoltCircleTriggered);
  connect(constructionMenu->addAction("Reference Rectangle..."), &QAction::triggered,
      this, &MainWindow::onAddReferenceRectangleTriggered);
  toolsMenu->addSeparator();
  toolsMenu->addAction(m_addDimensionDistanceToolAction);
  toolsMenu->addAction(m_addDimensionRadiusToolAction);
  toolsMenu->addAction(m_addDimensionAngleToolAction);
  toolsMenu->addAction(m_smartDimensionToolAction);

  HoverTooltip::installOn(toolBar);

  // Matches femm.rc's IDR_FEMMETYPE toolbar's edit/mesh/analyze section --
  // every one of these already exists as a menu item above; this just
  // gives the common ones a toolbar button too (per direct user request:
  // the classic GUI's toolbars are icon-driven, not text-menu-only).
  // Tooltip text matches femm.rc's own STRINGTABLE descriptions for these
  // command IDs where one exists, adapted lightly for wording that isn't
  // Qt-specific-command-ID-shaped.
  QToolBar* editToolBar = addToolBar("Edit");
  editToolBar->setToolButtonStyle(Qt::ToolButtonIconOnly);
  editToolBar->setIconSize(QSize(20, 20));
  addThemedAction(editToolBar, ":/icons/undo.svg", "Undo", "Undo the last operation", &MainWindow::onUndoTriggered);
  addThemedAction(editToolBar, ":/icons/open_selected.svg", "Open Selected", "Open the properties dialog for the currently selected entity", &MainWindow::onOpenSelectedTriggered);
  addThemedAction(editToolBar, ":/icons/delete.svg", "Delete", "Delete the selected objects", &MainWindow::onDeleteSelectedTriggered);
  // Matches femm.rc's IDR_FEMMETYPE toolbar's ID_FD_SELECTCIRC, right next
  // to ID_SELECTWND (that one has no femmqt equivalent since it's just
  // rubber-band drag-select, already the Select tool's default behavior)
  // -- toolbar-only in the classic GUI, no menu item, found missing during
  // a full icon-by-icon toolbar audit.
  addThemedAction(editToolBar, ":/icons/select_circle.svg", "Select by Circle", "Drag out a circle -- everything inside it gets selected", &MainWindow::onSelectByCircleTriggered);
  editToolBar->addSeparator();
  addThemedAction(editToolBar, ":/icons/move.svg", "Move", "Move the selected objects", &MainWindow::onMoveSelectedTriggered);
  addThemedAction(editToolBar, ":/icons/copy.svg", "Copy", "Copy the selected objects", &MainWindow::onCopySelectedTriggered);
  addThemedAction(editToolBar, ":/icons/scale.svg", "Scale", "Scale the selected objects", &MainWindow::onScaleSelectedTriggered);
  addThemedAction(editToolBar, ":/icons/mirror.svg", "Mirror", "Mirror the selected objects across a line", &MainWindow::onMirrorSelectedTriggered);
  addThemedAction(editToolBar, ":/icons/create_radius.svg", "Create Radius", "Convert a sharp corner into a radius", &MainWindow::onCreateRadiusTriggered);
  // Added by Claude (Anthropic), noreply@anthropic.com, 2026-09-12
  // (issue #30). Beside Create Radius because they are the same family:
  // a fillet, a flat and a parallel copy are the three things you do to
  // a corner or an edge, and Create Radius was the only one of them
  // femmqt had.
  addThemedAction(editToolBar, ":/icons/chamfer.svg", "Chamfer", "Cut a sharp corner off with a flat -- the straight counterpart to Create Radius", &MainWindow::onChamferTriggered);
  addThemedAction(editToolBar, ":/icons/offset.svg", "Offset", "Draw a parallel copy of the selected lines and arcs at a set distance", &MainWindow::onOffsetTriggered);
  addThemedAction(editToolBar, ":/icons/open_boundary.svg", "Create Open Boundary", "Create an asymptotic (Kelvin-transform) open boundary around the model", &MainWindow::onCreateOpenBoundaryTriggered);
  editToolBar->addSeparator();
  addThemedAction(editToolBar, ":/icons/group.svg", "Select by Group", "Select all entities belonging to a numbered group", &MainWindow::onSelectByGroupTriggered);
  HoverTooltip::installOn(editToolBar);

  QToolBar* constraintsToolBar = addToolBar("Constraints");
  constraintsToolBar->setToolButtonStyle(Qt::ToolButtonIconOnly);
  constraintsToolBar->setIconSize(QSize(20, 20));
  addThemedAction(constraintsToolBar, ":/icons/constraint_coincident.svg", "Coincident", "Coincident -- select 2 nodes", &MainWindow::onCoincidentConstraintTriggered);
  addThemedAction(constraintsToolBar, ":/icons/constraint_horizontal.svg", "Horizontal", "Horizontal -- select 1 segment", &MainWindow::onHorizontalConstraintTriggered);
  addThemedAction(constraintsToolBar, ":/icons/constraint_vertical.svg", "Vertical", "Vertical -- select 1 segment", &MainWindow::onVerticalConstraintTriggered);
  addThemedAction(constraintsToolBar, ":/icons/constraint_parallel.svg", "Parallel", "Parallel -- select 2 segments", &MainWindow::onParallelConstraintTriggered);
  addThemedAction(constraintsToolBar, ":/icons/constraint_perpendicular.svg", "Perpendicular", "Perpendicular -- select 2 segments", &MainWindow::onPerpendicularConstraintTriggered);
  addThemedAction(constraintsToolBar, ":/icons/constraint_equal.svg", "Equal", "Equal -- select 2 segments, or 2 arcs", &MainWindow::onEqualConstraintTriggered);
  addThemedAction(constraintsToolBar, ":/icons/constraint_tangent.svg", "Tangent", "Tangent -- select 1 segment + 1 arc, or 2 arcs", &MainWindow::onTangentConstraintTriggered);
  addThemedAction(constraintsToolBar, ":/icons/constraint_concentric.svg", "Concentric", "Concentric -- select 2 arcs", &MainWindow::onConcentricConstraintTriggered);
  addThemedAction(constraintsToolBar, ":/icons/constraint_symmetric.svg", "Symmetric", "Symmetric -- select 2 nodes + 1 segment (the mirror line)", &MainWindow::onSymmetricConstraintTriggered);
  HoverTooltip::installOn(constraintsToolBar);

  QToolBar* meshToolBar = addToolBar("Mesh");
  meshToolBar->setToolButtonStyle(Qt::ToolButtonIconOnly);
  meshToolBar->setIconSize(QSize(20, 20));
  addThemedAction(meshToolBar, ":/icons/mesh.svg", "Create Mesh", "Run the mesh generator", &MainWindow::onCreateMeshTriggered);
  addThemedAction(meshToolBar, ":/icons/solve.svg", "Solve", "Run the field analysis (mesh, then solve)", &MainWindow::onSolveTriggered);
  addThemedAction(meshToolBar, ":/icons/view_results.svg", "View Results", "View the results of the analysis", &MainWindow::onViewResultsTriggered);
  HoverTooltip::installOn(meshToolBar);

  // Matches femm.rc's separate IDR_LEFTBAR (zoom/pan/grid, docked on the
  // left in classic FEMM) -- kept as its own left-docked toolbar here
  // too, rather than folding it into the top ones, for the same reason:
  // it's a distinct, frequently-used group.
  QToolBar* navToolBar = addToolBar("Navigate");
  addToolBar(Qt::LeftToolBarArea, navToolBar);
  navToolBar->setOrientation(Qt::Vertical);
  navToolBar->setToolButtonStyle(Qt::ToolButtonIconOnly);
  navToolBar->setIconSize(QSize(20, 20));
  addThemedAction(navToolBar, ":/icons/zoom_in.svg", "Zoom In", "Zoom in", &MainWindow::onZoomIn);
  addThemedAction(navToolBar, ":/icons/zoom_out.svg", "Zoom Out", "Zoom out", &MainWindow::onZoomOut);
  addThemedAction(navToolBar, ":/icons/zoom_natural.svg", "Natural", "Zoom to fit the entire drawing", &MainWindow::onZoomNatural);
  addThemedAction(navToolBar, ":/icons/zoom_window.svg", "Window", "Drag a rectangle to zoom into", &MainWindow::onZoomWindowTriggered);
  navToolBar->addSeparator();
  addThemedAction(navToolBar, ":/icons/pan_up.svg", "Scroll Up", "Move the view up", &MainWindow::onPanUp);
  addThemedAction(navToolBar, ":/icons/pan_down.svg", "Scroll Down", "Move the view down", &MainWindow::onPanDown);
  addThemedAction(navToolBar, ":/icons/pan_left.svg", "Scroll Left", "Move the view left", &MainWindow::onPanLeft);
  addThemedAction(navToolBar, ":/icons/pan_right.svg", "Scroll Right", "Move the view right", &MainWindow::onPanRight);
  navToolBar->addSeparator();
  // Reuses the exact same QAction objects the Grid menu above already
  // created (not copies) so the toolbar buttons and menu checkmarks for
  // Show/Snap Grid never drift out of sync with each other. Icons are
  // re-tinted by refreshToolbarIcons() too (added to m_themedActions
  // manually here since addThemedAction() always creates a fresh action).
  navToolBar->addAction(showGridAction);
  showGridAction->setIcon(IconTheme::themedToolIcon(":/icons/show_grid.svg"));
  showGridAction->setToolTip("Show grid points");
  m_themedActions.push_back({ showGridAction, ":/icons/show_grid.svg" });
  navToolBar->addAction(snapGridAction);
  snapGridAction->setIcon(IconTheme::themedToolIcon(":/icons/snap_grid.svg"));
  snapGridAction->setToolTip("Snap new points and drags to the nearest grid point");
  m_themedActions.push_back({ snapGridAction, ":/icons/snap_grid.svg" });
  addThemedAction(navToolBar, ":/icons/set_grid.svg", "Set Grid", "Change the grid spacing", &MainWindow::onSetGridTriggered);
  HoverTooltip::installOn(navToolBar);

  m_positionLabel = new QLabel(this);
  m_positionLabel->setMinimumWidth(160);
  statusBar()->addPermanentWidget(m_positionLabel);
  // Added by Claude (Anthropic), noreply@anthropic.com, 2026-09-12 (#28):
  // names the snap the cursor is currently on. Left of the coordinates
  // because the two are read together -- the coordinate readout already
  // shows the SNAPPED position, and without this there is no way to tell
  // a snapped coordinate from a free one.
  m_snapLabel = new QLabel(this);
  m_snapLabel->setMinimumWidth(90);
  statusBar()->addPermanentWidget(m_snapLabel);
  connect(m_scene, &GeometryScene::mousePositionChanged, this, &MainWindow::onMousePositionChanged);
  connect(m_scene, &GeometryScene::snapChanged, this, &MainWindow::onSnapChanged);
  // #29: trim/extend/split decline for ordinary geometric reasons
  // ("nothing crosses that line"), which are not errors and must not be
  // dialogs -- but a click that does nothing and says nothing is
  // indistinguishable from a broken tool.
  connect(m_scene, &GeometryScene::toolMessage, this,
      [this](const QString& text) { statusBar()->showMessage(text, 6000); });

  statusBar()->showMessage("Ready");
  updateTitle();
}

// Added by Claude (Anthropic), noreply@anthropic.com, 2026-09-12 (#28).
void MainWindow::onSnapChanged(const SnapEngine::SnapResult& snap)
{
  if (!m_snapLabel)
    return;
  // Grid is deliberately named here even though the on-canvas glyph
  // stays hidden for it: a word in the status bar costs nothing and
  // answers "why did my point move?", whereas a marker chasing the
  // cursor across every grid square would be noise.
  m_snapLabel->setText(snap.snapped()
          ? QString("Snap: %1").arg(QString::fromLatin1(SnapEngine::name(snap.type)))
          : QString());
}

void MainWindow::onMousePositionChanged(QPointF scenePos)
{
  m_lastMousePos = scenePos;
  // Matches femm/FemmeView.cpp's OnMouseMove status-text format exactly:
  // (x,y) for planar Cartesian, (r,z) for axisymmetric Cartesian, or
  // (magnitude at angle) whenever Coords/coordsPolar is polar, regardless
  // of problem type.
  double x = scenePos.x(), y = scenePos.y();
  if (!m_problem.coordsPolar) {
    const char* label1 = m_problem.problemType == FemmCoordinateType::Axisymmetric ? "r" : "x";
    const char* label2 = m_problem.problemType == FemmCoordinateType::Axisymmetric ? "z" : "y";
    m_positionLabel->setText(QString("%1 = %2, %3 = %4").arg(label1).arg(x, 0, 'g', 6).arg(label2).arg(y, 0, 'g', 6));
  } else {
    double r = std::hypot(x, y);
    double deg = std::atan2(y, x) * 180.0 / M_PI;
    m_positionLabel->setText(QString("%1 at %2 deg").arg(r, 0, 'g', 6).arg(deg, 0, 'g', 6));
  }
}

void MainWindow::onEnterPointTriggered()
{
  // Matches femm/FemmeView.cpp's EnterPoint()/IDD_ENTERPT exactly: two
  // labeled fields whose meaning depends on coordsPolar (radius/degrees)
  // or else problemType (x/y planar, r/z axisymmetric), defaulting to the
  // cursor's last known position (converted to polar first if that's the
  // active mode) the same way classic seeds m_coord1/m_coord2 from mx/my.
  GeometryToolMode mode = m_scene->toolMode();
  if (mode != GeometryToolMode::AddNode && mode != GeometryToolMode::AddBlockLabel)
    return;

  QDialog dlg(this);
  dlg.setWindowTitle("Enter Point");
  auto* form = new QFormLayout;

  QString label1, label2;
  double coord1, coord2;
  if (!m_problem.coordsPolar) {
    label1 = m_problem.problemType == FemmCoordinateType::Axisymmetric ? "r-coord" : "x-coord";
    label2 = m_problem.problemType == FemmCoordinateType::Axisymmetric ? "z-coord" : "y-coord";
    coord1 = m_lastMousePos.x();
    coord2 = m_lastMousePos.y();
  } else {
    label1 = "radius";
    label2 = "degrees";
    coord1 = std::hypot(m_lastMousePos.x(), m_lastMousePos.y());
    coord2 = std::atan2(m_lastMousePos.y(), m_lastMousePos.x()) * 180.0 / M_PI;
  }

  auto* coord1Edit = new QLineEdit(QString::number(coord1, 'g', 12), &dlg);
  coord1Edit->setValidator(new QDoubleValidator(coord1Edit));
  form->addRow(label1 + ":", coord1Edit);
  auto* coord2Edit = new QLineEdit(QString::number(coord2, 'g', 12), &dlg);
  coord2Edit->setValidator(new QDoubleValidator(coord2Edit));
  form->addRow(label2 + ":", coord2Edit);

  auto* buttons = new QDialogButtonBox(QDialogButtonBox::Ok | QDialogButtonBox::Cancel, &dlg);
  connect(buttons, &QDialogButtonBox::accepted, &dlg, &QDialog::accept);
  connect(buttons, &QDialogButtonBox::rejected, &dlg, &QDialog::reject);

  auto* layout = new QVBoxLayout(&dlg);
  layout->addLayout(form);
  layout->addWidget(buttons);

  if (dlg.exec() != QDialog::Accepted)
    return;

  double x, y;
  if (!m_problem.coordsPolar) {
    x = coord1Edit->text().toDouble();
    y = coord2Edit->text().toDouble();
  } else {
    double r = coord1Edit->text().toDouble();
    double deg = coord2Edit->text().toDouble();
    x = r * std::cos(deg * M_PI / 180.0);
    y = r * std::sin(deg * M_PI / 180.0);
  }

  snapshotForUndo();
  if (mode == GeometryToolMode::AddNode)
    FemmProblemEdit::addNode(m_problem, x, y);
  else
    FemmProblemEdit::addBlockLabel(m_problem, x, y);
  m_scene->rebuild();
  markEdited();
}

void MainWindow::onNewTriggered()
{
  if (!confirmDiscardUnsavedChanges())
    return;

  // Issue #80: a document is one problem kind, chosen here, exactly as
  // the classic GUI's NewDocDlg asks. The kind cannot be changed
  // afterwards because the properties attached to the geometry mean
  // different things in each physics -- a permeability is not a thermal
  // conductivity -- so there is nothing sensible to convert them into.
  QDialog dlg(this);
  dlg.setWindowTitle("New Problem");
  auto* form = new QFormLayout;
  auto* kindCombo = new QComboBox(&dlg);
  const FemmProblemKind kinds[] = {
    FemmProblemKind::Magnetics,
    FemmProblemKind::Electrostatics,
    FemmProblemKind::HeatFlow,
    FemmProblemKind::CurrentFlow,
  };
  for (FemmProblemKind k : kinds) {
    kindCombo->addItem(QStringLiteral("%1  (*.%2)")
                           .arg(ProblemKind::displayName(k), ProblemKind::extension(k)));
  }
  form->addRow("Problem type:", kindCombo);
  auto* buttons = new QDialogButtonBox(QDialogButtonBox::Ok | QDialogButtonBox::Cancel, &dlg);
  QObject::connect(buttons, &QDialogButtonBox::accepted, &dlg, &QDialog::accept);
  QObject::connect(buttons, &QDialogButtonBox::rejected, &dlg, &QDialog::reject);
  auto* layout = new QVBoxLayout(&dlg);
  layout->addLayout(form);
  layout->addWidget(buttons);
  if (dlg.exec() != QDialog::Accepted)
    return;

  m_problem = FemmProblem();
  m_problem.kind = kinds[qBound(0, kindCombo->currentIndex(), 3)];
  m_currentPath.clear();
  m_scene->setProblem(&m_problem);
  m_dirty = false; // after setProblem() -- see the matching comment in openFile()
  m_view->resetZoomTransform();
  updateTitle();
  statusBar()->showMessage(
      QStringLiteral("New %1 problem").arg(ProblemKind::displayName(m_problem.kind)));
}

void MainWindow::onOpenTriggered()
{
  if (!confirmDiscardUnsavedChanges())
    return;
  const QString path = QFileDialog::getOpenFileName(this, "Open Problem", QString(),
      "FEMM Problems (*.fem *.fee *.feh *.fec *.femx);;"
      "Magnetics (*.fem *.femx);;"
      "Electrostatics (*.fee);;"
      "Heat Flow (*.feh);;"
      "Current Flow (*.fec)");
  if (path.isEmpty())
    return;
  openFile(path);
}

// Added by Claude (Anthropic), noreply@anthropic.com, 2026-09-13 (#91).
bool MainWindow::openDemo(const QString& demoPath, const QString& title)
{
  QString error;
  const QString copy = DemoLibrary::makeWorkingCopy(demoPath, error);
  if (copy.isEmpty()) {
    Notify::warning(this, "Open Demo",
        QStringLiteral("Couldn't make a working copy of this demo: %1").arg(error));
    return false;
  }

  // Deliberately the copy's path, not the original's: the solve
  // pipeline derives its working directory from whatever is open, so
  // this is what keeps triangle.exe and the solver out of the installed
  // demos directory.
  if (!openFile(copy))
    return false;

  m_isDemoCopy = true;
  m_demoTitle = title;
  updateTitle();
  statusBar()->showMessage(
      QStringLiteral("Opened a working copy of \"%1\" -- Save will ask where to "
                     "keep it").arg(title));
  return true;
}

bool MainWindow::openFile(const QString& path)
{
  QFileInfo pathInfo(path);
  QString femPath = path;
  QString femxPath = pathInfo.absolutePath() + "/" + pathInfo.completeBaseName() + ".femx";
  if (pathInfo.suffix().compare("femx", Qt::CaseInsensitive) == 0) {
    femPath = pathInfo.absolutePath() + "/" + pathInfo.completeBaseName() + ".fem";
    femxPath = path;
  }

  // Issue #80: which physics this file is, from its extension.
  FemmProblemKind kind = FemmProblemKind::Magnetics;
  if (!ProblemKind::kindForPath(femPath, kind)) {
    Notify::warning(this, "Open Failed",
        QStringLiteral("\"%1\" is not a FEMM model file. Expected .fem "
                       "(magnetics), .fee (electrostatics), .feh (heat flow) "
                       "or .fec (current flow).")
            .arg(pathInfo.fileName()));
    return false;
  }

  // THE .femx CACHE IS MAGNETICS-ONLY, deliberately, which #80 asked to
  // have decided explicitly rather than left to happen.
  //
  // It is a binary mirror of the .fem's record layout, and it exists
  // twice -- once in femmqt/ and once in femm/ -- which is a duplication
  // this repo has already been bitten by. Extending it to three more
  // formats means three more record layouts kept byte-identical across
  // both copies, in exchange for load time on models that do not exist:
  // the 88k-node magnetics models that motivated the cache have no
  // electrostatics or heat-flow counterpart here. The format also has no
  // field saying which physics it holds, so a .femx cannot describe a
  // .fee without a version bump that would invalidate every existing
  // cache.
  //
  // The correctness point matters more than the reasoning: a .femx
  // sitting beside a .fee is a cache of some OTHER model that shared the
  // base name, and loading it would silently hand back the wrong
  // geometry. Hence the kind check here, not just a preference.
  const bool cacheApplies = (kind == FemmProblemKind::Magnetics);

  QString error;
  FemmProblem problem;
  bool loadedFromFemx = false;

  if (cacheApplies && FemxFileIO::isUpToDate(femxPath, femPath)) {
    if (FemxFileIO::readFemx(femxPath, problem, error))
      loadedFromFemx = true;
    // falls through to the .fem path below if the cache turned out corrupt
  }

  if (!loadedFromFemx) {
    if (!QFileInfo::exists(femPath)) {
      Notify::warning(this, "Open Failed",
          QStringLiteral("\"%1\" doesn't exist and no matching .femx cache was found.").arg(femPath));
      return false;
    }
    if (!ProblemFileIO::readAs(femPath, kind, problem, error)) {
      Notify::warning(this, "Open Failed", error);
      return false;
    }
    // Cache for next time -- best-effort, same as the .ansx side, and
    // only for the format the cache describes.
    if (cacheApplies) {
      QString writeError;
      FemxFileIO::writeFemx(femxPath, femPath, problem, writeError);
    }
  }

  // Modified by Claude (Anthropic), noreply@anthropic.com, 2026-09-12:
  // restore the sketch layer from its sidecar (issue #27). Done here
  // rather than inside either file reader because the sketch belongs to
  // the MODEL, not to whichever of .fem/.femx happened to supply the
  // geometry -- and .femx is a regenerable cache, so it cannot be the
  // sketch's home (see SketchFileIO.h).
  //
  // References are re-resolved against the geometry that just loaded.
  // Anything that no longer matches is dropped and reported rather than
  // applied to whatever now occupies its index.
  QStringList sketchReport;
  QString sketchError;
  if (!SketchFileIO::readSketch(femPath, problem, sketchReport, sketchError)) {
    Notify::warning(this, "Sketch Not Loaded",
        QStringLiteral("The model opened, but its constraints and dimensions "
                       "did not:\n\n%1")
            .arg(sketchError));
  } else if (!sketchReport.isEmpty()) {
    Notify::information(this, "Sketch Partly Restored",
        QStringLiteral("The model opened. Some constraints or dimensions "
                       "could not be reattached to the geometry and were "
                       "dropped:\n\n%1")
            .arg(sketchReport.join("\n")));
  }

  m_problem = problem;
  m_currentPath = femPath;
  // Cleared here rather than by each caller: every ordinary open goes
  // through this function, and a stale flag would make Save prompt for
  // a document that has a perfectly good path of its own (#91).
  m_isDemoCopy = false;
  m_demoTitle.clear();
  m_scene->setProblem(&m_problem);
  QRectF problemBounds = m_scene->computeProblemBounds();
  m_view->fitInViewSafe(problemBounds);
  m_scene->setGridSize(niceIntegerGridSize(m_view->mapToScene(m_view->viewport()->rect()).boundingRect()));
  // After, not before, setProblem(): populating the scene calls setPos()
  // on every new NodeItem, which -- same as a real user drag -- fires
  // ItemPositionHasChanged -> onNodeMoved() -> problemEdited(), so a
  // freshly-opened, untouched file would otherwise show as dirty
  // immediately (confirmed directly: the window title showed a
  // trailing "*" right after this session's first GUI-switch test,
  // before this fix).
  m_dirty = false;

  statusBar()->showMessage(QString("%1 -- %2 nodes, %3 segments, %4 arcs, %5 block labels (loaded via %6)")
                                .arg(femPath)
                                .arg(m_problem.nodes.size())
                                .arg(m_problem.segments.size())
                                .arg(m_problem.arcSegments.size())
                                .arg(m_problem.blockLabels.size())
                                .arg(loadedFromFemx ? ".femx" : ".fem"));
  updateTitle();
  addToRecentFiles(femPath);
  return true;
}

void MainWindow::onSaveTriggered()
{
  // Issue #91: a demo's working copy lives in a temporary directory,
  // so writing back to it silently would put the user's work somewhere
  // they would never find it. Ask where it should go instead -- this
  // is the menu action only; saveAs() below is still what every
  // internal save (including the one before a solve) calls, and that
  // must not stop to ask.
  if (m_currentPath.isEmpty() || m_isDemoCopy) {
    onSaveAsTriggered();
    return;
  }
  saveAs(m_currentPath);
}

void MainWindow::onSaveAsTriggered()
{
  // Only this kind's extension is offered: the writer refuses a
  // mismatched one anyway (a heat-flow model saved as .fem would reopen
  // as magnetics with no properties), so offering the others would only
  // produce a refusal the user could have been spared.
  const QString ext = ProblemKind::extension(m_problem.kind);
  const QString path = QFileDialog::getSaveFileName(this,
      QStringLiteral("Save %1 Problem").arg(ProblemKind::displayName(m_problem.kind)),
      m_currentPath,
      QStringLiteral("%1 (*.%2)").arg(ProblemKind::displayName(m_problem.kind), ext));
  if (path.isEmpty())
    return;
  saveAs(path);
}

bool MainWindow::saveAs(const QString& path)
{
  QString error;
  if (!ProblemFileIO::write(path, m_problem, error)) {
    Notify::warning(this, "Save Failed", error);
    return false;
  }
  // Best-effort .femx cache refresh -- unlike .ansx's lazy on-open
  // generation, this can be done right here since the just-saved
  // FemmProblem is already in hand, so a save never leaves a stale cache
  // behind for this session's own next open.
  QFileInfo pathInfo(path);
  QString femxPath = pathInfo.absolutePath() + "/" + pathInfo.completeBaseName() + ".femx";
  if (m_problem.kind == FemmProblemKind::Magnetics) {
    QString femxError;
    FemxFileIO::writeFemx(femxPath, path, m_problem, femxError);
  }

  // Modified by Claude (Anthropic), noreply@anthropic.com, 2026-09-12:
  // the sketch layer goes to its own sidecar (issue #27). Best-effort in
  // the same sense as the .femx cache above -- a read-only directory must
  // not fail the save the user asked for -- but unlike the cache this is
  // the ONLY copy, so a failure is worth saying out loud rather than
  // swallowing. writeSketch removes the sidecar when the sketch is empty,
  // so deleting the last constraint persists too.
  QString sketchError;
  if (!SketchFileIO::writeSketch(path, m_problem, sketchError)
      && !(m_problem.constraints.isEmpty() && m_problem.dimensions.isEmpty())) {
    statusBar()->showMessage(
        QStringLiteral("Saved %1, but its constraints and dimensions were "
                       "not: %2").arg(path, sketchError));
  }

  // A saved-somewhere-else copy is an ordinary document; only a save
  // that lands back on the working copy itself leaves it a demo (#91).
  if (m_isDemoCopy && path != m_currentPath) {
    m_isDemoCopy = false;
    m_demoTitle.clear();
  }

  m_currentPath = path;
  m_dirty = false;
  updateTitle();
  statusBar()->showMessage(QString("Saved %1").arg(path));
  addToRecentFiles(path);
  return true;
}

void MainWindow::onSolveTriggered()
{
  // OnWritePoly (see MeshBuilder's header comment) reads geometry from
  // the saved .fem on disk, not straight from m_problem in memory --
  // matching the classic GUI's own OnMenuAnalyze (femm/FemmeView.cpp:
  // 2743), which force-saves right before meshing/solving. A file must
  // exist on disk either way, so this always saves first rather than
  // just checking m_dirty.
  if (m_currentPath.isEmpty()) {
    onSaveAsTriggered();
    if (m_currentPath.isEmpty())
      return; // user cancelled the save dialog
  } else if (!saveAs(m_currentPath)) {
    return;
  }

  if (hasAppliedPeriodicBoundary()) {
    Notify::warning(this, "Cannot Solve",
        "This problem uses a periodic or antiperiodic boundary condition, "
        "which this Qt GUI doesn't support meshing for yet. Open it in the "
        "classic FEMMX GUI to solve it.");
    return;
  }

  statusBar()->showMessage("Meshing and solving...");
  QApplication::setOverrideCursor(Qt::WaitCursor);
  // SolveRunner::solve() now pumps the event loop while it waits on
  // triangle.exe/fkn.exe (see SolveRunner.cpp's own comment) so the Load
  // Monitor's timer can actually sample during a solve -- but that also
  // means this window would otherwise still respond to menu clicks
  // mid-solve, and a second concurrent solve/mesh isn't safe (both would
  // write the same .poly/.pbc/.ans files). Disabling the menu bar for the
  // duration blocks that without blocking repaints/timers the way a full
  // setEnabled(false) on the whole window would.
  if (m_loadMonitor)
    m_loadMonitor->markSolveStart(QStringLiteral("magnetics: %1").arg(QFileInfo(m_currentPath).fileName()));
  menuBar()->setEnabled(false);
  QString error;
  bool ok = SolveRunner::solve(m_problem, m_currentPath, error);
  menuBar()->setEnabled(true);
  if (m_loadMonitor)
    m_loadMonitor->markSolveEnd();
  QApplication::restoreOverrideCursor();

  if (!ok) {
    statusBar()->showMessage("Solve failed");
    Notify::warning(this, "Solve Failed", error);
    return;
  }

  // Modified by Claude (Anthropic), noreply@anthropic.com, 2026-09-13
  // (issue #82): each solver writes its own solution format -- .ans,
  // .res, .anh, .anc -- so the path follows the document's kind rather
  // than always saying .ans.
  const QString solutionPath = QFileInfo(m_currentPath).absolutePath() + "/"
      + QFileInfo(m_currentPath).completeBaseName() + "."
      + ProblemKind::solutionExtension(m_problem.kind);
  statusBar()->showMessage(QString("Solved -- see %1").arg(solutionPath));

  // #83: the viewer reads all four now, so every kind opens it.
  const QString ansPath = solutionPath;
  if (!m_solutionWindow)
    m_solutionWindow = new SolutionWindow();
  // Modified by Claude (Anthropic), noreply@anthropic.com, 2026-07-20:
  // show() now runs BEFORE openAnsFile(), not after -- openAnsFile()'s
  // fitInView() call needs the view's real, final viewport geometry to
  // compute a correct "Natural" fit, and a QMainWindow's viewport can
  // report stale/default layout geometry before its first show(). Matches
  // the ordering main.cpp's own command-line-file-open path already uses.
  m_solutionWindow->show();
  m_solutionWindow->raise();
  m_solutionWindow->activateWindow();
  m_solutionWindow->openSolutionFile(ansPath);
}

void MainWindow::onViewResultsTriggered()
{
  if (!m_solutionWindow)
    m_solutionWindow = new SolutionWindow();
  m_solutionWindow->show();
  m_solutionWindow->raise();
  m_solutionWindow->activateWindow();
}

// Added by Claude (Anthropic), noreply@anthropic.com, 2026-09-13 (#90).
void MainWindow::onDemoModelsTriggered()
{
  QString error;
  const QVector<DemoLibrary::Demo> demos = DemoLibrary::load(error);
  if (demos.isEmpty()) {
    // Reached only if the library disappeared after startup, since the
    // action is disabled otherwise.
    Notify::warning(this, "Demo Models",
        QStringLiteral("No demo models are installed: %1").arg(error));
    return;
  }

  // An unsaved document would be silently replaced otherwise -- the
  // same guard the ordinary Open path uses.
  if (!confirmDiscardUnsavedChanges())
    return;

  DemoBrowserDialog dialog(demos, this);
  if (dialog.exec() != QDialog::Accepted)
    return;

  const DemoLibrary::Demo& demo = dialog.selected();
  // openDemo, not openFile: the installed original must never be the
  // file that is open. See DemoLibrary.h.
  openDemo(demo.absolutePath(), demo.title);
}

void MainWindow::onSwitchToClassicTriggered()
{
  // The other GUI needs a file on disk to open (there's no in-memory
  // handoff between two separate processes) -- same "must be saved"
  // requirement as onSolveTriggered, reusing the same confirm-or-save
  // flow the normal close path already uses.
  if (m_dirty) {
    // Cancel is the headless answer: with nobody to ask, refusing to
    // switch loses nothing, while Discard would throw away the user's
    // edits on their behalf (issue #85).
    auto result = Notify::question(this, "Switch GUI",
        "Save changes before switching to the classic GUI?",
        QMessageBox::Save | QMessageBox::Discard | QMessageBox::Cancel,
        QMessageBox::Save, QMessageBox::Cancel);
    if (result == QMessageBox::Cancel)
      return;
    if (result == QMessageBox::Save) {
      if (m_currentPath.isEmpty()) {
        onSaveAsTriggered();
        if (m_currentPath.isEmpty() || m_dirty)
          return; // save dialog was cancelled, or failed
      } else if (!saveAs(m_currentPath)) {
        return;
      }
    }
  }

  GuiSwitch::writePreferredGui(GuiSwitch::PreferredGui::Classic);
  if (!GuiSwitch::launchClassicGui(m_currentPath)) {
    Notify::warning(this, "Switch Failed",
        "Couldn't find or start femmx.exe next to femmqt.exe.");
    return;
  }
  close();
}

bool MainWindow::hasAppliedPeriodicBoundary() const
{
  // Mirrors CFemmeDoc::HasPeriodicBC (femm/writepoly.cpp:28-88): BdryFormat
  // 4-7 are the periodic/antiperiodic variants: 4/5 are the ones a plain
  // segment can carry (femm/writepoly.cpp:57), while arcs can carry any of
  // 4-7 (femm/writepoly.cpp:77). Only checks properties actually referenced
  // by a segment/arc, not just defined -- an unused periodic boundary
  // definition doesn't block solving, matching the original's own
  // two-phase check.
  auto isPeriodicFormat = [](int fmt, bool allowExtended) {
    return fmt == 4 || fmt == 5 || (allowExtended && (fmt == 6 || fmt == 7));
  };
  for (const FemmSegment& s : m_problem.segments) {
    if (s.boundaryMarker <= 0 || s.boundaryMarker > m_problem.boundaryProps.size())
      continue;
    if (isPeriodicFormat(m_problem.boundaryProps[s.boundaryMarker - 1].bdryFormat, false))
      return true;
  }
  for (const FemmArcSegment& a : m_problem.arcSegments) {
    if (a.boundaryMarker <= 0 || a.boundaryMarker > m_problem.boundaryProps.size())
      continue;
    if (isPeriodicFormat(m_problem.boundaryProps[a.boundaryMarker - 1].bdryFormat, true))
      return true;
  }
  return false;
}

void MainWindow::onProblemEdited()
{
  markEdited();
}

void MainWindow::markEdited()
{
  m_dirty = true;
  updateTitle();
}

void MainWindow::onProblemPropertiesTriggered()
{
  ProblemPropertiesDialog dlg(m_problem, this);
  if (dlg.exec() == QDialog::Accepted)
    markEdited();
}

void MainWindow::onExteriorRegionTriggered()
{
  ExteriorRegionDialog dlg(m_problem, this);
  if (dlg.exec() == QDialog::Accepted)
    markEdited();
}

void MainWindow::onMaterialsLibraryTriggered()
{
  MaterialLibraryDialog dlg(m_problem, this);
  dlg.exec();
  // The dialog only ever appends (never edits/removes) materials, so
  // there's nothing to roll back if the user just browsed without adding
  // anything -- but mark dirty unconditionally rather than tracking
  // whether "Add to Problem" actually fired, since a spurious dirty flag
  // costs nothing (worst case: an extra prompt to save unchanged data)
  // while a missed one could silently lose an added material.
  markEdited();
}

void MainWindow::onPreferencesTriggered()
{
  bool wasDark = AppTheme::isDark();
  PreferencesDialog dlg(this);
  if (dlg.exec() != QDialog::Accepted)
    return;
  if (AppTheme::isDark() != wasDark) {
    m_scene->refreshTheme();
    refreshToolbarIcons();
  }
  // #28: the snap toggles have to reach the live scene, not just
  // femm.cfg -- a setting that only takes effect after a restart reads
  // as a broken setting.
  m_scene->setSnapFlags(AppPreferences::load().snapFlags);
}

void MainWindow::onDarkThemeToggled(bool dark)
{
  AppTheme::setDark(dark);
  AppPreferences prefs = AppPreferences::load();
  prefs.darkTheme = dark;
  prefs.save();
  m_scene->refreshTheme();
  refreshToolbarIcons();
  if (m_loadMonitor)
    m_loadMonitor->refreshTheme();
}

void MainWindow::onLoadMonitorToggled(bool show)
{
  if (!m_loadMonitor) {
    m_loadMonitor = new LoadMonitorDialog(this);
    // Registers it with this window's docking system (per direct user
    // request: "a floating window that can be attached in the main
    // window") -- floating right away gives it the same default
    // appearance the old always-separate dialog had; from there, Qt's
    // own dock-widget title bar lets the user drag it into any of this
    // window's dock areas, or back out again.
    addDockWidget(Qt::RightDockWidgetArea, m_loadMonitor);
    m_loadMonitor->setFloating(true);
  }
  m_loadMonitor->setMonitoring(show);
}

void MainWindow::onCreateRadiusTriggered()
{
  // Requires exactly one selected node touching either two segments, two
  // arcs, or one of each -- femm/FemmeDoc.cpp's CanCreateRadius (the
  // classic GUI enforces this the same way, via its own node-selection
  // requirement before enabling this command).
  m_scene->syncSelectionToProblem();
  int nodeIndex = -1;
  for (int i = 0; i < m_problem.nodes.size(); i++) {
    if (m_problem.nodes[i].isSelected) {
      if (nodeIndex >= 0) {
        Notify::information(this, "Create Radius", "Select exactly one node first.");
        return;
      }
      nodeIndex = i;
    }
  }
  if (nodeIndex < 0) {
    Notify::information(this, "Create Radius", "Select a node first (one shared by two segments, two arcs, or one of each).");
    return;
  }
  if (!FemmProblemEdit::canCreateRadius(m_problem, nodeIndex)) {
    Notify::information(this, "Create Radius",
        "That node isn't a valid corner to fillet -- it needs to be shared by exactly two segments, two arcs, or one segment and one arc.");
    return;
  }

  bool ok = false;
  double r = QInputDialog::getDouble(this, "Create Radius", "Radius:", 0.0, 0.0, 1.0e300, 6, &ok);
  if (!ok)
    return;

  snapshotForUndo();
  if (!FemmProblemEdit::createRadius(m_problem, nodeIndex, r)) {
    Notify::warning(this, "Create Radius",
        "Couldn't fit a radius of that size at that corner (too large, a near-straight corner, or no valid tangent solution).");
    return;
  }
  m_scene->rebuild();
  markEdited();
}

// Added by Claude (Anthropic), noreply@anthropic.com, 2026-09-12 (#30).
//
// Chamfer takes the same corner selection as Create Radius directly
// above, and reports its refusals the same way -- a corner that cannot
// be cut is a fact about the drawing, not an error.
void MainWindow::onChamferTriggered()
{
  m_scene->syncSelectionToProblem();
  int nodeIndex = -1;
  for (int i = 0; i < m_problem.nodes.size(); i++) {
    if (m_problem.nodes[i].isSelected) {
      if (nodeIndex >= 0) {
        Notify::information(this, "Chamfer", "Select exactly one node first.");
        return;
      }
      nodeIndex = i;
    }
  }
  if (nodeIndex < 0) {
    Notify::information(this, "Chamfer",
        "Select the corner node to chamfer first -- one shared by exactly two straight lines.");
    return;
  }

  QDialog dlg(this);
  dlg.setWindowTitle("Chamfer");
  auto* form = new QFormLayout;

  auto* modeCombo = new QComboBox(&dlg);
  modeCombo->addItems({ "Distance and distance", "Distance and angle" });
  form->addRow("Define by:", modeCombo);

  const QString units = lengthUnitsName(m_problem.lengthUnits);
  auto* firstEdit = new QLineEdit("1", &dlg);
  firstEdit->setValidator(new QDoubleValidator(1e-12, 1e12, 12, firstEdit));
  form->addRow(QString("First distance (%1):").arg(units), firstEdit);

  auto* secondEdit = new QLineEdit("1", &dlg);
  secondEdit->setValidator(new QDoubleValidator(1e-12, 1e12, 12, secondEdit));
  auto* secondLabel = new QLabel(QString("Second distance (%1):").arg(units), &dlg);
  form->addRow(secondLabel, secondEdit);

  // The second field means two different things, so it says which rather
  // than leaving the user to infer it from the combo above.
  QObject::connect(modeCombo, &QComboBox::currentIndexChanged, &dlg, [&](int i) {
    if (i == 0) {
      secondLabel->setText(QString("Second distance (%1):").arg(units));
      secondEdit->setText("1");
    } else {
      secondLabel->setText("Angle to the first edge (degrees):");
      secondEdit->setText("45");
    }
  });

  auto* buttons = new QDialogButtonBox(QDialogButtonBox::Ok | QDialogButtonBox::Cancel, &dlg);
  QObject::connect(buttons, &QDialogButtonBox::accepted, &dlg, &QDialog::accept);
  QObject::connect(buttons, &QDialogButtonBox::rejected, &dlg, &QDialog::reject);
  auto* layout = new QVBoxLayout(&dlg);
  layout->addLayout(form);
  layout->addWidget(buttons);
  if (dlg.exec() != QDialog::Accepted)
    return;

  const double first = firstEdit->text().toDouble();
  const double second = secondEdit->text().toDouble();

  // Try it on a copy, so a refusal costs no undo step -- same reasoning
  // as GeometryScene::handleTrimExtendClick (#29).
  FemmProblem trial = m_problem;
  const OffsetChamfer::Result probe = modeCombo->currentIndex() == 0
      ? OffsetChamfer::chamferDistances(trial, nodeIndex, first, second)
      : OffsetChamfer::chamferDistanceAngle(trial, nodeIndex, first, second);
  if (!probe.ok) {
    Notify::information(this, "Chamfer", probe.message);
    return;
  }

  snapshotForUndo();
  if (modeCombo->currentIndex() == 0)
    OffsetChamfer::chamferDistances(m_problem, nodeIndex, first, second);
  else
    OffsetChamfer::chamferDistanceAngle(m_problem, nodeIndex, first, second);
  m_scene->rebuild();
  markEdited();
}

void MainWindow::onOffsetTriggered()
{
  m_scene->syncSelectionToProblem();
  int selected = 0;
  for (const FemmSegment& s : m_problem.segments)
    if (s.isSelected)
      selected++;
  for (const FemmArcSegment& a : m_problem.arcSegments)
    if (a.isSelected)
      selected++;
  if (selected == 0) {
    Notify::information(this, "Offset",
        "Select the lines and arcs to offset first. A connected run offsets as one "
        "curve, with its corners resolved; anything disconnected offsets on its own.");
    return;
  }

  QDialog dlg(this);
  dlg.setWindowTitle("Offset");
  auto* form = new QFormLayout;

  auto* distEdit = new QLineEdit("1", &dlg);
  // Deliberately signed: the side is part of the distance, and there is
  // no way to point at a side from a modal dialog.
  distEdit->setValidator(new QDoubleValidator(-1e12, 1e12, 12, distEdit));
  form->addRow(QString("Distance (%1):").arg(lengthUnitsName(m_problem.lengthUnits)), distEdit);

  auto* cornerCombo = new QComboBox(&dlg);
  cornerCombo->addItems({ "Sharp (extend and intersect)", "Rounded (arc of the offset radius)" });
  form->addRow("Outside corners:", cornerCombo);

  auto* note = new QLabel(
      "A positive distance offsets to the left of each chain's direction of travel, "
      "a negative one to the right. Boundary conditions are not copied onto the new "
      "curve: the original still carries them, and imposing the same condition in two "
      "places would change the problem rather than the drawing.",
      &dlg);
  note->setWordWrap(true);
  note->setMinimumWidth(360);

  auto* buttons = new QDialogButtonBox(QDialogButtonBox::Ok | QDialogButtonBox::Cancel, &dlg);
  QObject::connect(buttons, &QDialogButtonBox::accepted, &dlg, &QDialog::accept);
  QObject::connect(buttons, &QDialogButtonBox::rejected, &dlg, &QDialog::reject);
  auto* layout = new QVBoxLayout(&dlg);
  layout->addLayout(form);
  layout->addWidget(note);
  layout->addWidget(buttons);
  if (dlg.exec() != QDialog::Accepted)
    return;

  const double distance = distEdit->text().toDouble();
  const OffsetChamfer::CornerStyle style = cornerCombo->currentIndex() == 0
      ? OffsetChamfer::CornerStyle::Miter
      : OffsetChamfer::CornerStyle::Fillet;

  FemmProblem trial = m_problem;
  const OffsetChamfer::Result probe = OffsetChamfer::offsetSelection(trial, distance, style);
  if (!probe.ok) {
    Notify::information(this, "Offset", probe.message);
    return;
  }

  snapshotForUndo();
  const OffsetChamfer::Result r = OffsetChamfer::offsetSelection(m_problem, distance, style);
  m_scene->rebuild();
  markEdited();
  // What was created, and what was deliberately not carried over. In the
  // status bar rather than a dialog: it is a report, not a question.
  statusBar()->showMessage(r.message, 10000);
}

// Added by Claude (Anthropic), noreply@anthropic.com, 2026-09-12 (#31).
//
// All four share one shape: try it, and only take an undo snapshot if it
// is going to do something. A command that refuses must not consume an
// undo step -- see GeometryScene::handleTrimExtendClick (#29) for why
// that is a data-loss issue rather than a nuisance.
void MainWindow::applyConstructionResult(const QString& title,
    const ConstructionGeometry::Result& r)
{
  if (!r.ok) {
    Notify::information(this, title, r.message);
    return;
  }
  m_scene->rebuild();
  markEdited();
  statusBar()->showMessage(r.message, 8000);
}

void MainWindow::convertSelectionConstruction(bool toConstruction)
{
  m_scene->syncSelectionToProblem();
  FemmProblem trial = m_problem;
  const ConstructionGeometry::Result probe =
      ConstructionGeometry::setSelectedConstruction(trial, toConstruction);
  if (!probe.ok) {
    Notify::information(this, "Construction Geometry", probe.message);
    return;
  }
  snapshotForUndo();
  applyConstructionResult("Construction Geometry",
      ConstructionGeometry::setSelectedConstruction(m_problem, toConstruction));
}

void MainWindow::onAddCentrelineTriggered()
{
  QDialog dlg(this);
  dlg.setWindowTitle("Centreline");
  auto* form = new QFormLayout;
  const QString units = lengthUnitsName(m_problem.lengthUnits);

  // Prefilled with the axis, because in an axisymmetric model that is
  // the centreline nearly every time and r=0 is not part of the drawn
  // geometry.
  auto* x0 = new QLineEdit("0", &dlg);
  auto* y0 = new QLineEdit("0", &dlg);
  auto* x1 = new QLineEdit("0", &dlg);
  auto* y1 = new QLineEdit("100", &dlg);
  for (QLineEdit* e : { x0, y0, x1, y1 })
    e->setValidator(new QDoubleValidator(-1e12, 1e12, 12, e));
  form->addRow(QString("From x (%1):").arg(units), x0);
  form->addRow(QString("From y (%1):").arg(units), y0);
  form->addRow(QString("To x (%1):").arg(units), x1);
  form->addRow(QString("To y (%1):").arg(units), y1);

  auto* buttons = new QDialogButtonBox(QDialogButtonBox::Ok | QDialogButtonBox::Cancel, &dlg);
  QObject::connect(buttons, &QDialogButtonBox::accepted, &dlg, &QDialog::accept);
  QObject::connect(buttons, &QDialogButtonBox::rejected, &dlg, &QDialog::reject);
  auto* layout = new QVBoxLayout(&dlg);
  layout->addLayout(form);
  layout->addWidget(buttons);
  if (dlg.exec() != QDialog::Accepted)
    return;

  snapshotForUndo();
  applyConstructionResult("Centreline",
      ConstructionGeometry::addCentreline(m_problem, x0->text().toDouble(),
          y0->text().toDouble(), x1->text().toDouble(), y1->text().toDouble()));
}

void MainWindow::onAddBoltCircleTriggered()
{
  QDialog dlg(this);
  dlg.setWindowTitle("Bolt Circle");
  auto* form = new QFormLayout;
  const QString units = lengthUnitsName(m_problem.lengthUnits);

  auto* cx = new QLineEdit("0", &dlg);
  auto* cy = new QLineEdit("0", &dlg);
  auto* radius = new QLineEdit("50", &dlg);
  auto* start = new QLineEdit("0", &dlg);
  for (QLineEdit* e : { cx, cy, radius, start })
    e->setValidator(new QDoubleValidator(-1e12, 1e12, 12, e));
  auto* count = new QSpinBox(&dlg);
  count->setRange(1, 1000);
  count->setValue(6);

  form->addRow(QString("Centre x (%1):").arg(units), cx);
  form->addRow(QString("Centre y (%1):").arg(units), cy);
  form->addRow(QString("Radius (%1):").arg(units), radius);
  form->addRow("Positions:", count);
  form->addRow("First position at (degrees):", start);

  auto* buttons = new QDialogButtonBox(QDialogButtonBox::Ok | QDialogButtonBox::Cancel, &dlg);
  QObject::connect(buttons, &QDialogButtonBox::accepted, &dlg, &QDialog::accept);
  QObject::connect(buttons, &QDialogButtonBox::rejected, &dlg, &QDialog::reject);
  auto* layout = new QVBoxLayout(&dlg);
  layout->addLayout(form);
  layout->addWidget(buttons);
  if (dlg.exec() != QDialog::Accepted)
    return;

  snapshotForUndo();
  applyConstructionResult("Bolt Circle",
      ConstructionGeometry::addBoltCircle(m_problem, cx->text().toDouble(),
          cy->text().toDouble(), radius->text().toDouble(), count->value(),
          start->text().toDouble()));
}

void MainWindow::onAddReferenceRectangleTriggered()
{
  QDialog dlg(this);
  dlg.setWindowTitle("Reference Rectangle");
  auto* form = new QFormLayout;
  const QString units = lengthUnitsName(m_problem.lengthUnits);

  auto* x0 = new QLineEdit("0", &dlg);
  auto* y0 = new QLineEdit("0", &dlg);
  auto* x1 = new QLineEdit("100", &dlg);
  auto* y1 = new QLineEdit("60", &dlg);
  for (QLineEdit* e : { x0, y0, x1, y1 })
    e->setValidator(new QDoubleValidator(-1e12, 1e12, 12, e));
  form->addRow(QString("Corner x (%1):").arg(units), x0);
  form->addRow(QString("Corner y (%1):").arg(units), y0);
  form->addRow(QString("Opposite x (%1):").arg(units), x1);
  form->addRow(QString("Opposite y (%1):").arg(units), y1);

  auto* buttons = new QDialogButtonBox(QDialogButtonBox::Ok | QDialogButtonBox::Cancel, &dlg);
  QObject::connect(buttons, &QDialogButtonBox::accepted, &dlg, &QDialog::accept);
  QObject::connect(buttons, &QDialogButtonBox::rejected, &dlg, &QDialog::reject);
  auto* layout = new QVBoxLayout(&dlg);
  layout->addLayout(form);
  layout->addWidget(buttons);
  if (dlg.exec() != QDialog::Accepted)
    return;

  snapshotForUndo();
  applyConstructionResult("Reference Rectangle",
      ConstructionGeometry::addReferenceRectangle(m_problem, x0->text().toDouble(),
          y0->text().toDouble(), x1->text().toDouble(), y1->text().toDouble()));
}

void MainWindow::onCreateOpenBoundaryTriggered()
{
  OpenBoundaryDialog dlg(m_problem, this);
  snapshotForUndo();
  if (dlg.exec() == QDialog::Accepted) {
    m_scene->rebuild();
    markEdited();
  }
}

void MainWindow::onImportDxfTriggered()
{
  QString path = QFileDialog::getOpenFileName(this, "Import DXF", QString(), "DXF Files (*.dxf)");
  if (path.isEmpty())
    return;

  FemmProblem parsed;
  double suggestedTolerance = 0;
  QString error;
  if (!DxfIO::parseDxf(path, parsed, suggestedTolerance, error)) {
    Notify::warning(this, "Import DXF", error);
    return;
  }

  bool ok = false;
  double tolerance = QInputDialog::getDouble(this, "Import DXF",
      "Merge nodes within this distance of each other:", suggestedTolerance, 0.0, 1.0e300, 10, &ok);
  if (!ok)
    return;
  DxfIO::mergeCoincidentNodes(parsed, tolerance);

  snapshotForUndo();
  int nodeOffset = m_problem.nodes.size();
  for (const FemmNode& n : parsed.nodes)
    m_problem.nodes.push_back(n);
  for (FemmSegment s : parsed.segments) {
    s.n0 += nodeOffset;
    s.n1 += nodeOffset;
    m_problem.segments.push_back(s);
  }
  for (FemmArcSegment a : parsed.arcSegments) {
    a.n0 += nodeOffset;
    a.n1 += nodeOffset;
    m_problem.arcSegments.push_back(a);
  }
  m_scene->rebuild();
  markEdited();
  statusBar()->showMessage(QString("Imported %1 nodes, %2 segments, %3 arcs from %4")
                                .arg(parsed.nodes.size())
                                .arg(parsed.segments.size())
                                .arg(parsed.arcSegments.size())
                                .arg(path));
}

void MainWindow::onExportDxfTriggered()
{
  QString path = QFileDialog::getSaveFileName(this, "Export DXF", QString(), "DXF Files (*.dxf)");
  if (path.isEmpty())
    return;
  QString error;
  if (!DxfIO::exportDxf(path, m_problem, error))
    Notify::warning(this, "Export DXF", error);
  else
    statusBar()->showMessage(QString("Exported %1").arg(path));
}

void MainWindow::onPrintTriggered()
{
  if (!m_printer)
    m_printer = new QPrinter(QPrinter::HighResolution);
  QPrintDialog dlg(m_printer, this);
  if (dlg.exec() != QDialog::Accepted)
    return;
  QPainter painter(m_printer);
  m_view->render(&painter);
}

void MainWindow::onPrintPreviewTriggered()
{
  if (!m_printer)
    m_printer = new QPrinter(QPrinter::HighResolution);
  QPrintPreviewDialog dlg(m_printer, this);
  connect(&dlg, &QPrintPreviewDialog::paintRequested, this, [this](QPrinter* p) {
    QPainter painter(p);
    m_view->render(&painter);
  });
  dlg.exec();
}

void MainWindow::onPrintSetupTriggered()
{
  if (!m_printer)
    m_printer = new QPrinter(QPrinter::HighResolution);
  QPageSetupDialog dlg(m_printer, this);
  dlg.exec();
}

void MainWindow::onCopyBitmapTriggered()
{
  QPixmap pixmap = m_view->viewport()->grab();
  QApplication::clipboard()->setPixmap(pixmap);
  statusBar()->showMessage("Copied view to clipboard as a bitmap.");
}

void MainWindow::onDeleteSelectedTriggered()
{
  if (!m_scene->hasSelection()) {
    Notify::information(this, "Delete", "Nothing selected.");
    return;
  }
  m_scene->deleteSelectedItem();
}

void MainWindow::onSelectByCircleTriggered()
{
  // Arms the one-shot drag; GeometryScene::mouseReleaseEvent does the
  // actual selection and reverts back to Select mode itself, same pattern
  // as onZoomWindowTriggered.
  m_scene->setToolMode(GeometryToolMode::SelectCircle);
}

void MainWindow::onOpenSelectedTriggered()
{
  FemmItemKind kind;
  QVector<int> indices;
  if (!m_scene->selectedEntities(kind, indices)) {
    Notify::information(this, "Open Selected",
        m_scene->hasSelection() ? "Select entities of only one kind (nodes, segments, arcs, or block labels) at a time." : "Nothing selected.");
    return;
  }
  openEntityProperties(kind, indices);
}

// Added by Claude (Anthropic), noreply@anthropic.com, 2026-09-13 (#81).
//
// The property-list handler for every category of every problem kind
// that has a field spec. The list itself was already generic
// (PropertyListDialog takes callbacks); what is new is that the count,
// the names, the add, the delete and the reference count all go through
// ProblemKind, and the edit dialog is built from a field spec instead of
// being a hand-written class per physics.
//
// Magnetics still takes the branch below this one: its four dialogs
// already match the classic ones field for field, and two of them do
// things a flat field list does not describe -- the BH curve editor, and
// the point property's radio pair that ZEROES the other pair rather than
// just grasying it out. Rewriting those to gain uniformity would risk a
// regression in the one physics that already works.
void MainWindow::showPropertyList(ProblemKind::Category category)
{
  PropertyListDialog::Callbacks cb;
  cb.count = [this, category]() { return ProblemKind::count(m_problem, category); };
  cb.nameAt = [this, category](int i) { return ProblemKind::name(m_problem, category, i); };
  cb.editAt = [this, category](int i) {
    PropertyEditDialog dlg(PropertyFields::specFor(m_problem, category, i), this);
    if (dlg.exec() == QDialog::Accepted) {
      m_scene->rebuild();
      markEdited();
    }
  };
  cb.addNew = [this, category]() {
    ProblemKind::addDefault(m_problem, category);
    markEdited();
  };
  cb.referenceCount = [this, category](int i) {
    return ProblemKind::referenceCount(m_problem, category, i);
  };
  cb.remove = [this, category](int i) {
    ProblemKind::remove(m_problem, category, i);
    m_scene->rebuild();
    markEdited();
  };

  const QString label = ProblemKind::categoryLabel(m_problem.kind, category);
  PropertyListDialog dlg(label, label.toLower(), cb, this);
  dlg.exec();
}

void MainWindow::onMaterialsTriggered()
{
  if (PropertyFields::hasSpec(m_problem, ProblemKind::Category::Material)) {
    showPropertyList(ProblemKind::Category::Material);
    return;
  }
  PropertyListDialog::Callbacks cb;
  cb.count = [this]() { return m_problem.materialProps.size(); };
  cb.nameAt = [this](int i) { return m_problem.materialProps[i].name; };
  cb.editAt = [this](int i) {
    MaterialPropDialog dlg(m_problem.materialProps[i], this);
    if (dlg.exec() == QDialog::Accepted)
      markEdited();
  };
  cb.addNew = [this]() {
    FemmMaterialProp m;
    m.name = uniqueName(m_problem.materialProps, "New Material");
    m_problem.materialProps.push_back(m);
    markEdited();
  };
  cb.referenceCount = [this](int i) { return FemmProblemEdit::countMaterialPropReferences(m_problem, i); };
  cb.remove = [this](int i) {
    FemmProblemEdit::deleteMaterialProp(m_problem, i);
    m_scene->rebuild();
    markEdited();
  };
  PropertyListDialog dlg("Materials", "material", cb, this);
  dlg.exec();
}

void MainWindow::onBoundaryPropsTriggered()
{
  if (PropertyFields::hasSpec(m_problem, ProblemKind::Category::Boundary)) {
    showPropertyList(ProblemKind::Category::Boundary);
    return;
  }
  PropertyListDialog::Callbacks cb;
  cb.count = [this]() { return m_problem.boundaryProps.size(); };
  cb.nameAt = [this](int i) { return m_problem.boundaryProps[i].name; };
  cb.editAt = [this](int i) {
    BoundaryPropDialog dlg(m_problem.boundaryProps[i], this);
    if (dlg.exec() == QDialog::Accepted)
      markEdited();
  };
  cb.addNew = [this]() {
    FemmBoundaryProp b;
    b.name = uniqueName(m_problem.boundaryProps, "New Boundary");
    m_problem.boundaryProps.push_back(b);
    markEdited();
  };
  cb.referenceCount = [this](int i) { return FemmProblemEdit::countBoundaryPropReferences(m_problem, i); };
  cb.remove = [this](int i) {
    FemmProblemEdit::deleteBoundaryProp(m_problem, i);
    m_scene->rebuild();
    markEdited();
  };
  PropertyListDialog dlg("Boundary Properties", "boundary", cb, this);
  dlg.exec();
}

void MainWindow::onCircuitsTriggered()
{
  if (PropertyFields::hasSpec(m_problem, ProblemKind::Category::Source)) {
    showPropertyList(ProblemKind::Category::Source);
    return;
  }
  PropertyListDialog::Callbacks cb;
  cb.count = [this]() { return m_problem.circuitProps.size(); };
  cb.nameAt = [this](int i) { return m_problem.circuitProps[i].name; };
  cb.editAt = [this](int i) {
    CircuitPropDialog dlg(m_problem.circuitProps[i], this);
    if (dlg.exec() == QDialog::Accepted)
      markEdited();
  };
  cb.addNew = [this]() {
    FemmCircuitProp c;
    c.name = uniqueName(m_problem.circuitProps, "New Circuit");
    m_problem.circuitProps.push_back(c);
    markEdited();
  };
  cb.referenceCount = [this](int i) { return FemmProblemEdit::countCircuitPropReferences(m_problem, i); };
  cb.remove = [this](int i) {
    FemmProblemEdit::deleteCircuitProp(m_problem, i);
    m_scene->rebuild();
    markEdited();
  };
  PropertyListDialog dlg("Circuits", "circuit", cb, this);
  dlg.exec();
}

void MainWindow::onPointPropsTriggered()
{
  if (PropertyFields::hasSpec(m_problem, ProblemKind::Category::Point)) {
    showPropertyList(ProblemKind::Category::Point);
    return;
  }
  PropertyListDialog::Callbacks cb;
  cb.count = [this]() { return m_problem.pointProps.size(); };
  cb.nameAt = [this](int i) { return m_problem.pointProps[i].name; };
  cb.editAt = [this](int i) {
    PointPropDialog dlg(m_problem.pointProps[i], this);
    if (dlg.exec() == QDialog::Accepted)
      markEdited();
  };
  cb.addNew = [this]() {
    FemmPointProp p;
    p.name = uniqueName(m_problem.pointProps, "New Point Property");
    m_problem.pointProps.push_back(p);
    markEdited();
  };
  cb.referenceCount = [this](int i) { return FemmProblemEdit::countPointPropReferences(m_problem, i); };
  cb.remove = [this](int i) {
    FemmProblemEdit::deletePointProp(m_problem, i);
    m_scene->rebuild();
    markEdited();
  };
  PropertyListDialog dlg("Point Properties", "point property", cb, this);
  dlg.exec();
}

void MainWindow::onEntityDoubleClicked(FemmItemKind kind, int index)
{
  openEntityProperties(kind, { index });
}

void MainWindow::openEntityProperties(FemmItemKind kind, const QVector<int>& indices)
{
  bool accepted = false;
  switch (kind) {
  case FemmItemKind::Node: {
    QVector<FemmNode*> nodes;
    for (int i : indices)
      if (i >= 0 && i < m_problem.nodes.size())
        nodes.push_back(&m_problem.nodes[i]);
    if (!nodes.isEmpty()) {
      NodePropDialog dlg(nodes, m_problem, this);
      accepted = dlg.exec() == QDialog::Accepted;
    }
    break;
  }
  case FemmItemKind::Segment: {
    QVector<FemmSegment*> segments;
    for (int i : indices)
      if (i >= 0 && i < m_problem.segments.size())
        segments.push_back(&m_problem.segments[i]);
    if (!segments.isEmpty()) {
      SegmentPropDialog dlg(segments, m_problem, this);
      accepted = dlg.exec() == QDialog::Accepted;
    }
    break;
  }
  case FemmItemKind::Arc: {
    QVector<FemmArcSegment*> arcs;
    for (int i : indices)
      if (i >= 0 && i < m_problem.arcSegments.size())
        arcs.push_back(&m_problem.arcSegments[i]);
    if (!arcs.isEmpty()) {
      ArcPropDialog dlg(arcs, m_problem, this);
      accepted = dlg.exec() == QDialog::Accepted;
    }
    break;
  }
  case FemmItemKind::BlockLabel: {
    QVector<FemmBlockLabel*> labels;
    for (int i : indices)
      if (i >= 0 && i < m_problem.blockLabels.size())
        labels.push_back(&m_problem.blockLabels[i]);
    if (!labels.isEmpty()) {
      BlockLabelPropDialog dlg(labels, m_problem, this);
      accepted = dlg.exec() == QDialog::Accepted;
    }
    break;
  }
  // Modified by Claude (Anthropic), noreply@anthropic.com: double-click
  // to edit a dimension's value -- unlike the property dialogs above
  // (which only ever change non-geometric properties like boundary/
  // material assignment), this one CAN move geometry, via the constraint
  // solver -- so it snapshots for undo itself, unlike its siblings here
  // (none of which currently do; a pre-existing gap in this function,
  // not something newly introduced).
  case FemmItemKind::Dimension: {
    if (indices.isEmpty() || indices.first() < 0 || indices.first() >= m_problem.dimensions.size())
      break;
    FemmDimension& dim = m_problem.dimensions[indices.first()];
    // Modified by Claude (Anthropic), noreply@anthropic.com: was a 2-way
    // ternary chain that silently fell through to the Angle label/bounds
    // for HorizontalDistance/VerticalDistance (added alongside the Smart
    // Dimension tool's two-point H/V/Aligned inference) -- switched to an
    // explicit switch so a new DimensionType can't silently inherit the
    // wrong label/bounds again.
    QString label;
    double minVal = 0.0, maxVal = 1.0e9;
    switch (dim.type) {
    case DimensionType::Distance:
    case DimensionType::HorizontalDistance:
    case DimensionType::VerticalDistance:
      label = "Distance:";
      break;
    case DimensionType::Radius:
      label = "Radius:";
      break;
    case DimensionType::Angle:
      label = "Angle (deg):";
      minVal = -359.99;
      maxVal = 359.99;
      break;
    case DimensionType::AngleLines:
      // Lines have no direction, so their angle only spans (0,180) -- see
      // DimensionType::AngleLines in FemmProblem.h.
      label = "Angle (deg):";
      minVal = 0.01;
      maxVal = 179.99;
      break;
    }
    bool ok = false;
    double newValue = QInputDialog::getDouble(this, "Edit Dimension", label, dim.value, minVal, maxVal, 6, &ok);
    if (ok && newValue != dim.value) {
      snapshotForUndo();
      dim.value = newValue;
      ConstraintSolver::SolveResult result = ConstraintSolver::solve(m_problem);
      m_scene->setConstraintStatus(result.nodeStatus);
      accepted = true;
    }
    break;
  }
  }

  if (accepted) {
    // A block label's hole/material-assigned rendering (see
    // addBlockLabelItem's pen color) depends on blockTypeIndex, which
    // this dialog can change -- rebuild() to reflect it. Cheap enough at
    // this editor's scale (thousands, not millions, of entities) to just
    // always do it here rather than tracking which edits actually need it.
    m_scene->rebuild();
    markEdited();
  }
}

// Zoom/Pan -- mirrors FemmeView.cpp's OnZoomIn/OnZoomOut/OnPan* (2x-per-
// step zoom, quarter-viewport-per-step pan), just expressed as relative
// QGraphicsView transforms/scrollbar deltas instead of raw GDI ox/oy/mag
// bookkeeping -- Qt's view already owns an equivalent transform, so there's
// no reason to duplicate that state on this side.
void MainWindow::onZoomIn()
{
  m_view->zoomBy(2.0);
}

void MainWindow::onZoomOut()
{
  m_view->zoomBy(0.5);
}

void MainWindow::onZoomNatural()
{
  m_view->fitInViewSafe(m_scene->computeProblemBounds());
}

void MainWindow::onZoomWindowTriggered()
{
  m_scene->setToolMode(GeometryToolMode::ZoomWindow);
}

QImage MainWindow::renderToImage(QSize size, QRectF source)
{
  if (m_scene == nullptr || size.isEmpty())
    return QImage();

  const QRectF bounds = m_scene->computeProblemBounds();
  if (bounds.isEmpty())
    return QImage();

  QImage image(size, QImage::Format_ARGB32);
  image.fill(AppTheme::background());

  QPainter painter(&image);
  painter.setRenderHint(QPainter::Antialiasing, true);
  // y-up scene, same flip as SolutionWindow::renderToImage -- see there.
  painter.translate(0, size.height());
  painter.scale(1.0, -1.0);

  m_scene->render(&painter, QRectF(QPointF(0, 0), QSizeF(size)),
      source.isEmpty() ? bounds : source, Qt::KeepAspectRatio);
  return image;
}

void MainWindow::onZoomWindowSelected(QRectF sceneRect)
{
  m_view->fitInViewSafe(sceneRect);
  // Match the toolbar's radio buttons back to Select, which is what the
  // scene itself reverted to internally (see GeometryScene::
  // mouseReleaseEvent) -- Zoom Window isn't part of that QActionGroup (see
  // its header comment), so nothing else re-checks this automatically.
  m_selectToolAction->setChecked(true);
}

void MainWindow::onKbdZoomTriggered()
{
  // Matches femm/FemmeView.cpp's OnKbdZoom (IDD_KBDZOOM): a numeric-entry
  // alternative to Zoom > Window's mouse drag, prefilled with the current
  // view bounds. Ends by reusing the exact same fitInViewSafe path Zoom
  // Window uses -- only how the target rect is obtained differs.
  QRectF visible = m_view->mapToScene(m_view->viewport()->rect()).boundingRect();

  QDialog dlg(this);
  dlg.setWindowTitle("Set View Bounds");
  auto* form = new QFormLayout(&dlg);
  auto* leftEdit = new QLineEdit(QString::number(visible.left(), 'g', 6));
  auto* rightEdit = new QLineEdit(QString::number(visible.right(), 'g', 6));
  auto* topEdit = new QLineEdit(QString::number(visible.bottom(), 'g', 6)); // scene is y-up (GeometryView::fitInViewSafe applies scale(1,-1)) -- bottom() is numerically the larger y, i.e. "Top" in problem space
  auto* bottomEdit = new QLineEdit(QString::number(visible.top(), 'g', 6));
  for (auto* e : {leftEdit, rightEdit, topEdit, bottomEdit})
    e->setValidator(new QDoubleValidator(e));
  form->addRow("Left:", leftEdit);
  form->addRow("Right:", rightEdit);
  form->addRow("Top:", topEdit);
  form->addRow("Bottom:", bottomEdit);
  auto* buttons = new QDialogButtonBox(QDialogButtonBox::Ok | QDialogButtonBox::Cancel, &dlg);
  connect(buttons, &QDialogButtonBox::accepted, &dlg, &QDialog::accept);
  connect(buttons, &QDialogButtonBox::rejected, &dlg, &QDialog::reject);
  form->addRow(buttons);
  if (dlg.exec() != QDialog::Accepted)
    return;

  double x0 = leftEdit->text().toDouble();
  double x1 = rightEdit->text().toDouble();
  double y0 = topEdit->text().toDouble();
  double y1 = bottomEdit->text().toDouble();
  QRectF rect(qMin(x0, x1), qMin(y0, y1), qAbs(x1 - x0), qAbs(y1 - y0));
  m_view->fitInViewSafe(rect);
}

void MainWindow::onPanLeft()
{
  auto* bar = m_view->horizontalScrollBar();
  bar->setValue(bar->value() - m_view->viewport()->width() / 4);
}

void MainWindow::onPanRight()
{
  auto* bar = m_view->horizontalScrollBar();
  bar->setValue(bar->value() + m_view->viewport()->width() / 4);
}

void MainWindow::onPanUp()
{
  auto* bar = m_view->verticalScrollBar();
  bar->setValue(bar->value() - m_view->viewport()->height() / 4);
}

void MainWindow::onPanDown()
{
  auto* bar = m_view->verticalScrollBar();
  bar->setValue(bar->value() + m_view->viewport()->height() / 4);
}

void MainWindow::onSetGridTriggered()
{
  // Matches femm/GRIDDLG.h's GRIDDLG exactly (CAPTION "Grid Properties"):
  // Grid Size plus a Coordinates combo (Cartesian/Polar) -- the same
  // coordsPolar flag EnterPoint() (onEnterPointTriggered) and the status
  // bar's mouse-position readout (onMousePositionChanged) both read.
  QDialog dlg(this);
  dlg.setWindowTitle("Set Grid");
  auto* form = new QFormLayout;

  auto* sizeEdit = new QLineEdit(QString::number(m_scene->gridSize(), 'g', 12), &dlg);
  sizeEdit->setValidator(new QDoubleValidator(1e-9, 1e9, 12, sizeEdit));
  // Per direct user request -- classic's own Grid Properties dialog shows
  // a bare number with no unit indication at all.
  form->addRow(QString("Grid Size (%1):").arg(lengthUnitsName(m_problem.lengthUnits)), sizeEdit);

  auto* coordsCombo = new QComboBox(&dlg);
  coordsCombo->addItems({ "Cartesian", "Polar" });
  coordsCombo->setCurrentIndex(m_problem.coordsPolar ? 1 : 0);
  form->addRow("Coordinates:", coordsCombo);

  auto* buttons = new QDialogButtonBox(QDialogButtonBox::Ok | QDialogButtonBox::Cancel, &dlg);
  QObject::connect(buttons, &QDialogButtonBox::accepted, &dlg, &QDialog::accept);
  QObject::connect(buttons, &QDialogButtonBox::rejected, &dlg, &QDialog::reject);

  auto* layout = new QVBoxLayout(&dlg);
  layout->addLayout(form);
  layout->addWidget(buttons);

  if (dlg.exec() != QDialog::Accepted)
    return;

  // setGridSize() unconditionally busts GeometryView's background cache
  // (see GeometryScene::resetViewBackgroundCache()) -- relied on here to
  // also repaint the Cartesian/Polar switch below, since that alone
  // doesn't go through setShowGrid/setGridSize.
  m_scene->setGridSize(sizeEdit->text().toDouble());
  m_problem.coordsPolar = coordsCombo->currentIndex() == 1;
  markEdited();
}

void MainWindow::snapshotForUndo()
{
  m_undoStack.push_back(m_problem);
  if (m_undoStack.size() > kMaxUndoSteps)
    m_undoStack.pop_front();
}

void MainWindow::onUndoTriggered()
{
  if (m_undoStack.isEmpty()) {
    statusBar()->showMessage("Nothing to undo");
    return;
  }
  m_problem = m_undoStack.takeLast();
  m_scene->rebuild();
  markEdited();
  statusBar()->showMessage(QString("Undone (%1 more step%2 available)").arg(m_undoStack.size()).arg(m_undoStack.size() == 1 ? "" : "s"));
}

void MainWindow::onMoveSelectedTriggered()
{
  if (!m_scene->hasSelection()) {
    Notify::information(this, "Move", "Nothing selected.");
    return;
  }
  MoveCopyDialog dlg(/*isMove=*/true, this);
  if (dlg.exec() != QDialog::Accepted)
    return;

  snapshotForUndo();
  m_scene->syncSelectionToProblem();
  // #32: a transform can change what a constraint MEANS -- a rotated
  // line is no longer horizontal -- and the report says so rather than
  // leaving the user to discover it when the next solve pulls the
  // geometry back.
  SketchTransform::Report sketchReport;
  if (dlg.transformMode() == MoveCopyDialog::TransformMode::Rotate)
    FemmProblemEdit::rotateSelected(m_problem, dlg.aboutX(), dlg.aboutY(), dlg.shiftAngleDeg(), &sketchReport);
  else
    FemmProblemEdit::moveSelected(m_problem, dlg.deltaX(), dlg.deltaY());
  m_scene->rebuild();
  markEdited();
  reportSketchTransform("Move", sketchReport);
}

void MainWindow::onCopySelectedTriggered()
{
  if (!m_scene->hasSelection()) {
    Notify::information(this, "Copy", "Nothing selected.");
    return;
  }
  MoveCopyDialog dlg(/*isMove=*/false, this);
  if (dlg.exec() != QDialog::Accepted)
    return;

  snapshotForUndo();
  m_scene->syncSelectionToProblem();
  SketchTransform::Report sketchReport;
  if (dlg.transformMode() == MoveCopyDialog::TransformMode::Rotate)
    FemmProblemEdit::rotateCopySelected(m_problem, dlg.aboutX(), dlg.aboutY(), dlg.shiftAngleDeg(), dlg.numCopies(), &sketchReport);
  else
    FemmProblemEdit::translateCopySelected(m_problem, dlg.deltaX(), dlg.deltaY(), dlg.numCopies(), &sketchReport);
  m_scene->rebuild();
  markEdited();
  reportSketchTransform("Copy", sketchReport);
}

void MainWindow::onScaleSelectedTriggered()
{
  if (!m_scene->hasSelection()) {
    Notify::information(this, "Scale", "Nothing selected.");
    return;
  }
  bool ok = false;
  double factor = QInputDialog::getDouble(this, "Scale", "Scale Factor:", 1.0, 1e-9, 1e9, 6, &ok);
  if (!ok)
    return;
  double baseX = QInputDialog::getDouble(this, "Scale", "Base Point X:", 0.0, -1e9, 1e9, 6, &ok);
  if (!ok)
    return;
  double baseY = QInputDialog::getDouble(this, "Scale", "Base Point Y:", 0.0, -1e9, 1e9, 6, &ok);
  if (!ok)
    return;

  snapshotForUndo();
  m_scene->syncSelectionToProblem();
  SketchTransform::Report sketchReport;
  FemmProblemEdit::scaleSelected(m_problem, baseX, baseY, factor, &sketchReport);
  m_scene->rebuild();
  markEdited();
  reportSketchTransform("Scale", sketchReport);
}

void MainWindow::onMirrorSelectedTriggered()
{
  if (!m_scene->hasSelection()) {
    Notify::information(this, "Mirror", "Nothing selected.");
    return;
  }
  bool ok = false;
  double x0 = QInputDialog::getDouble(this, "Mirror", "Mirror Line Point 1, X:", 0.0, -1e9, 1e9, 6, &ok);
  if (!ok)
    return;
  double y0 = QInputDialog::getDouble(this, "Mirror", "Mirror Line Point 1, Y:", 0.0, -1e9, 1e9, 6, &ok);
  if (!ok)
    return;
  double x1 = QInputDialog::getDouble(this, "Mirror", "Mirror Line Point 2, X:", 0.0, -1e9, 1e9, 6, &ok);
  if (!ok)
    return;
  double y1 = QInputDialog::getDouble(this, "Mirror", "Mirror Line Point 2, Y:", 1.0, -1e9, 1e9, 6, &ok);
  if (!ok)
    return;

  snapshotForUndo();
  m_scene->syncSelectionToProblem();
  SketchTransform::Report sketchReport;
  FemmProblemEdit::mirrorSelected(m_problem, x0, y0, x1, y1, &sketchReport);
  m_scene->rebuild();
  markEdited();
  reportSketchTransform("Mirror", sketchReport);
}

// Added by Claude (Anthropic), noreply@anthropic.com, 2026-09-12 (#32).
//
// The status bar for the ordinary outcome -- "N constraints came along"
// is information, not a question -- and a dialog only when something was
// dropped or now conflicts, because those change what the model means
// and are worth stopping for.
void MainWindow::reportSketchTransform(const QString& title,
    const SketchTransform::Report& r)
{
  const QString summary = r.summary();
  if (summary.isEmpty())
    return;
  if (r.constraintsDropped == 0 && r.conflictsIntroduced == 0) {
    statusBar()->showMessage(title + ": " + summary, 8000);
    return;
  }
  QMessageBox box(this);
  box.setIcon(QMessageBox::Information);
  box.setWindowTitle(title);
  box.setText(summary);
  if (!r.notes.isEmpty())
    box.setDetailedText(r.notes.join("\n\n"));
  box.exec();
}

void MainWindow::applyConstraint(const FemmConstraint& c)
{
  snapshotForUndo();
  m_problem.constraints.push_back(c);
  ConstraintSolver::SolveResult result = ConstraintSolver::solve(m_problem);
  m_scene->setConstraintStatus(result.nodeStatus);
  m_scene->rebuild();
  markEdited();
  if (!result.converged)
    statusBar()->showMessage("Constraint added, but the sketch could not be fully solved -- check for a conflict (shown in red).", 6000);
}

void MainWindow::onCoincidentConstraintTriggered()
{
  QVector<int> nodes, segments, arcs, blocks;
  m_scene->selectedByKind(nodes, segments, arcs, blocks);
  if (nodes.size() != 2 || !segments.isEmpty() || !arcs.isEmpty()) {
    Notify::information(this, "Coincident", "Select exactly 2 nodes.");
    return;
  }
  FemmConstraint c;
  c.type = ConstraintType::Coincident;
  c.refA = nodes[0];
  c.refB = nodes[1];
  applyConstraint(c);
}

void MainWindow::onHorizontalConstraintTriggered()
{
  QVector<int> nodes, segments, arcs, blocks;
  m_scene->selectedByKind(nodes, segments, arcs, blocks);
  if (segments.size() != 1 || !nodes.isEmpty() || !arcs.isEmpty()) {
    Notify::information(this, "Horizontal", "Select exactly 1 segment.");
    return;
  }
  FemmConstraint c;
  c.type = ConstraintType::Horizontal;
  c.refA = segments[0];
  applyConstraint(c);
}

void MainWindow::onVerticalConstraintTriggered()
{
  QVector<int> nodes, segments, arcs, blocks;
  m_scene->selectedByKind(nodes, segments, arcs, blocks);
  if (segments.size() != 1 || !nodes.isEmpty() || !arcs.isEmpty()) {
    Notify::information(this, "Vertical", "Select exactly 1 segment.");
    return;
  }
  FemmConstraint c;
  c.type = ConstraintType::Vertical;
  c.refA = segments[0];
  applyConstraint(c);
}

void MainWindow::onParallelConstraintTriggered()
{
  QVector<int> nodes, segments, arcs, blocks;
  m_scene->selectedByKind(nodes, segments, arcs, blocks);
  if (segments.size() != 2 || !nodes.isEmpty() || !arcs.isEmpty()) {
    Notify::information(this, "Parallel", "Select exactly 2 segments.");
    return;
  }
  FemmConstraint c;
  c.type = ConstraintType::Parallel;
  c.refA = segments[0];
  c.refB = segments[1];
  applyConstraint(c);
}

void MainWindow::onPerpendicularConstraintTriggered()
{
  QVector<int> nodes, segments, arcs, blocks;
  m_scene->selectedByKind(nodes, segments, arcs, blocks);
  if (segments.size() != 2 || !nodes.isEmpty() || !arcs.isEmpty()) {
    Notify::information(this, "Perpendicular", "Select exactly 2 segments.");
    return;
  }
  FemmConstraint c;
  c.type = ConstraintType::Perpendicular;
  c.refA = segments[0];
  c.refB = segments[1];
  applyConstraint(c);
}

void MainWindow::onEqualConstraintTriggered()
{
  QVector<int> nodes, segments, arcs, blocks;
  m_scene->selectedByKind(nodes, segments, arcs, blocks);
  FemmConstraint c;
  c.type = ConstraintType::Equal;
  if (segments.size() == 2 && nodes.isEmpty() && arcs.isEmpty()) {
    c.isArcPair = false;
    c.refA = segments[0];
    c.refB = segments[1];
  } else if (arcs.size() == 2 && nodes.isEmpty() && segments.isEmpty()) {
    c.isArcPair = true;
    c.refA = arcs[0];
    c.refB = arcs[1];
  } else {
    Notify::information(this, "Equal", "Select exactly 2 segments, or exactly 2 arcs.");
    return;
  }
  applyConstraint(c);
}

void MainWindow::onTangentConstraintTriggered()
{
  QVector<int> nodes, segments, arcs, blocks;
  m_scene->selectedByKind(nodes, segments, arcs, blocks);
  FemmConstraint c;
  c.type = ConstraintType::Tangent;
  if (segments.size() == 1 && arcs.size() == 1 && nodes.isEmpty()) {
    c.firstIsArc = false;
    c.refA = segments[0];
    c.refB = arcs[0];
  } else if (arcs.size() == 2 && nodes.isEmpty() && segments.isEmpty()) {
    c.firstIsArc = true;
    c.refA = arcs[0];
    c.refB = arcs[1];
  } else {
    Notify::information(this, "Tangent", "Select exactly 1 segment + 1 arc, or exactly 2 arcs.");
    return;
  }
  applyConstraint(c);
}

void MainWindow::onConcentricConstraintTriggered()
{
  QVector<int> nodes, segments, arcs, blocks;
  m_scene->selectedByKind(nodes, segments, arcs, blocks);
  if (arcs.size() != 2 || !nodes.isEmpty() || !segments.isEmpty()) {
    Notify::information(this, "Concentric", "Select exactly 2 arcs.");
    return;
  }
  FemmConstraint c;
  c.type = ConstraintType::Concentric;
  c.refA = arcs[0];
  c.refB = arcs[1];
  applyConstraint(c);
}

void MainWindow::onSymmetricConstraintTriggered()
{
  QVector<int> nodes, segments, arcs, blocks;
  m_scene->selectedByKind(nodes, segments, arcs, blocks);
  if (nodes.size() != 2 || segments.size() != 1 || !arcs.isEmpty()) {
    Notify::information(this, "Symmetric", "Select exactly 2 nodes and 1 segment (the mirror line).");
    return;
  }
  FemmConstraint c;
  c.type = ConstraintType::Symmetric;
  c.refA = nodes[0];
  c.refB = nodes[1];
  c.refC = segments[0];
  applyConstraint(c);
}

void MainWindow::onSolveConstraintsTriggered()
{
  if (m_problem.constraints.isEmpty() && m_problem.dimensions.isEmpty()) {
    statusBar()->showMessage("No constraints or dimensions to solve.", 4000);
    return;
  }
  snapshotForUndo();
  ConstraintSolver::SolveResult result = ConstraintSolver::solve(m_problem);
  m_scene->setConstraintStatus(result.nodeStatus);
  m_scene->rebuild();
  markEdited();
  statusBar()->showMessage(result.converged
          ? QString("Solved in %1 iteration(s), residual %2.").arg(result.iterations).arg(result.finalResidualNorm, 0, 'g', 3)
          : "Could not fully solve -- check for a conflict (shown in red).",
      6000);
}

void MainWindow::onClearConstraintsTriggered()
{
  if (m_problem.constraints.isEmpty())
    return;
  snapshotForUndo();
  m_problem.constraints.clear();
  ConstraintSolver::SolveResult result = ConstraintSolver::solve(m_problem);
  m_scene->setConstraintStatus(result.nodeStatus);
  m_scene->rebuild();
  markEdited();
}

void MainWindow::onClearDimensionsTriggered()
{
  if (m_problem.dimensions.isEmpty())
    return;
  snapshotForUndo();
  m_problem.dimensions.clear();
  ConstraintSolver::SolveResult result = ConstraintSolver::solve(m_problem);
  m_scene->setConstraintStatus(result.nodeStatus);
  m_scene->rebuild();
  markEdited();
}

void MainWindow::onConstraintListTriggered()
{
  ConstraintListDialog::Callbacks cb;
  cb.count = [this]() { return m_problem.constraints.size(); };
  cb.descriptionAt = [this](int i) { return describeConstraint(m_problem, m_problem.constraints[i]); };
  cb.selectOnCanvas = [this](int i) { m_scene->selectConstraintGlyph(i); };
  cb.remove = [this](int i) {
    snapshotForUndo();
    FemmProblemEdit::deleteConstraint(m_problem, i);
    ConstraintSolver::SolveResult result = ConstraintSolver::solve(m_problem);
    m_scene->setConstraintStatus(result.nodeStatus);
    m_scene->rebuild();
    markEdited();
  };
  ConstraintListDialog dlg(cb, this);
  dlg.exec();
}

void MainWindow::onCreateMeshTriggered()
{
  // Same "must be saved first" requirement as Solve -- MeshBuilder reads
  // geometry from the saved .fem, not m_problem directly (see
  // onSolveTriggered's comment).
  if (m_currentPath.isEmpty()) {
    onSaveAsTriggered();
    if (m_currentPath.isEmpty())
      return;
  } else if (!saveAs(m_currentPath)) {
    return;
  }

  if (hasAppliedPeriodicBoundary()) {
    Notify::warning(this, "Cannot Mesh",
        "This problem uses a periodic or antiperiodic boundary condition, "
        "which this Qt GUI doesn't support meshing for yet. Open it in the "
        "classic FEMMX GUI instead.");
    return;
  }

  statusBar()->showMessage("Meshing...");
  QApplication::setOverrideCursor(Qt::WaitCursor);
  // See onSolveTriggered's matching comment -- SolveRunner::mesh() also
  // pumps events now, so the menu bar is disabled for the same
  // re-entrancy reason (triangle.exe here writes the same rootPath.* files
  // a concurrent Solve would).
  menuBar()->setEnabled(false);
  QString error;
  bool ok = SolveRunner::mesh(m_problem, m_currentPath, error);
  menuBar()->setEnabled(true);
  QApplication::restoreOverrideCursor();
  if (!ok) {
    statusBar()->showMessage("Meshing failed");
    Notify::warning(this, "Mesh Failed", error);
    return;
  }

  QFileInfo fi(m_currentPath);
  QString rootPath = fi.absolutePath() + "/" + fi.completeBaseName();
  MeshOverlay mesh;
  if (!MeshOverlayIO::load(rootPath, mesh, error)) {
    statusBar()->showMessage("Meshing failed");
    Notify::warning(this, "Mesh Failed", error);
    return;
  }

  m_scene->setMeshOverlay(mesh);
  m_scene->setShowMesh(true);
  m_showMeshAction->setChecked(true);
  statusBar()->showMessage(QString("Meshed -- %1 nodes, %2 elements").arg(mesh.nodes.size()).arg(mesh.elements.size()));
}

void MainWindow::onPurgeMeshTriggered()
{
  m_scene->clearMeshOverlay();
  m_showMeshAction->setChecked(false);

  // Matches femm.rc's "Purge Mesh" actually deleting the mesh files on
  // disk (not just hiding the overlay), so a subsequent Solve can't
  // accidentally pick up a stale mesh -- though SolveRunner::solve()
  // always regenerates them fresh anyway, this also mirrors the classic
  // GUI's own disk-cleanliness intent.
  if (!m_currentPath.isEmpty()) {
    QFileInfo fi(m_currentPath);
    QString rootPath = fi.absolutePath() + "/" + fi.completeBaseName();
    QFile::remove(rootPath + ".node");
    QFile::remove(rootPath + ".edge");
    QFile::remove(rootPath + ".ele");
  }
  statusBar()->showMessage("Mesh purged");
}

void MainWindow::onShowOrphansTriggered()
{
  if (m_scene->selectOrphans())
    statusBar()->showMessage("Orphaned nodes found and selected -- these likely mean an unclosed region.");
  else
    statusBar()->showMessage("No orphaned nodes found.");
}

void MainWindow::onSelectByGroupTriggered()
{
  bool ok = false;
  int group = QInputDialog::getInt(this, "Select by Group", "Group Number:", 0, 0, 1000000, 1, &ok);
  if (ok)
    m_scene->selectByGroup(group);
}

void MainWindow::onSetGroupTriggered()
{
  if (!m_scene->hasSelection()) {
    Notify::information(this, "Set Group", "Nothing selected.");
    return;
  }
  bool ok = false;
  int group = QInputDialog::getInt(this, "Set Group", "Group Number:", 0, 0, 1000000, 1, &ok);
  if (!ok)
    return;
  m_scene->syncSelectionToProblem();
  m_scene->applyGroupToSelected(group);
  markEdited();
}

void MainWindow::addToRecentFiles(const QString& path)
{
  QSettings settings;
  QStringList recent = settings.value("recentFiles").toStringList();
  recent.removeAll(path);
  recent.prepend(path);
  while (recent.size() > 8)
    recent.removeLast();
  settings.setValue("recentFiles", recent);
  updateRecentFilesMenu();
}

void MainWindow::updateRecentFilesMenu()
{
  m_recentFilesMenu->clear();
  QSettings settings;
  QStringList recent = settings.value("recentFiles").toStringList();
  if (recent.isEmpty()) {
    QAction* empty = m_recentFilesMenu->addAction("(none)");
    empty->setEnabled(false);
    return;
  }
  for (const QString& path : recent) {
    QAction* action = m_recentFilesMenu->addAction(path);
    action->setData(path);
    connect(action, &QAction::triggered, this, &MainWindow::onOpenRecentFile);
  }
}

void MainWindow::onOpenRecentFile()
{
  auto* action = qobject_cast<QAction*>(sender());
  if (!action)
    return;
  QString path = action->data().toString();
  if (!QFileInfo::exists(path)) {
    Notify::warning(this, "Open Failed", QStringLiteral("\"%1\" no longer exists.").arg(path));
    QSettings settings;
    QStringList recent = settings.value("recentFiles").toStringList();
    recent.removeAll(path);
    settings.setValue("recentFiles", recent);
    updateRecentFilesMenu();
    return;
  }
  if (!confirmDiscardUnsavedChanges())
    return;
  openFile(path);
}
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
