SpgV0/femmx/femm/femmeLua.cpp

// femmeDoc.cpp : implementation of the CFemmeDoc class
//
// Modified by Claude (Anthropic), noreply@anthropic.com, 2026-07-07:
// added mi_setredraw Lua command (lua_setredraw) so scripts can suspend
// canvas redraw during batch edits (e.g. many mi_copytranslate/
// mi_copyrotate calls) and force a single refresh when re-enabled.
// Modified by Claude (Anthropic), noreply@anthropic.com, 2026-07-08:
// added mi_setgpuaccel Lua command (lua_setgpuaccel) to opt a problem
// into fkn.exe's optional CUDA-accelerated linear solve.

#include "stdafx.h"
#include "BitmapCapture.h"
#include "MaterialFolder.h"
#include "ScriptGui.h"
#include "femm.h"
#include "femmeDoc.h"
#include "femmeView.h"
#include "promptbox.h"
#include "MainFrm.h"
#include "ChildFrm.h"

extern BOOL lua_byebye;
extern void* pFemmeDoc;
extern lua_State* lua;
extern BOOL bLinehook;
extern CLuaConsoleDlg* LuaConsole;
extern int m_luaWindowStatus;

#define CatchNullDocument()                              \
  ;                                                      \
  if (pFemmeDoc == NULL) {                               \
    CString msg = "No current magnetics input in focus"; \
    lua_error(L, msg.GetBuffer(1));                      \
    return 0;                                            \
  }

//---------------------Lua Extensions------------------------

void CFemmeDoc::initalise_lua()
{
  // generalized lua functionality
  // should put these in femm.cpp or something

  // register lua extensions
  lua_register(lua, "mi_saveas", luaSaveDocument);
  lua_register(lua, "mi_createmesh", lua_create_mesh);
  lua_register(lua, "mi_smartmesh", lua_smartmesh);
  lua_register(lua, "mi_showmesh", lua_show_mesh);
  lua_register(lua, "mi_purgemesh", lua_purge_mesh);
  lua_register(lua, "mi_probdef", lua_prob_def);
  lua_register(lua, "mi_analyse", lua_analyze);
  lua_register(lua, "mi_loadsolution", lua_runpost);
  lua_register(lua, "mi_addnode", lua_addnode);
  lua_register(lua, "mi_addblocklabel", lua_addlabel);
  lua_register(lua, "mi_addsegment", lua_addline);
  lua_register(lua, "mi_addarc", lua_addarc);
  lua_register(lua, "mi_selectnode", lua_selectnode);
  lua_register(lua, "mi_selectlabel", lua_selectlabel);
  lua_register(lua, "mi_selectsegment", lua_selectsegment);
  lua_register(lua, "mi_selectarcsegment", lua_selectarcsegment);
  lua_register(lua, "mi_clearselected", lua_clearselected);
  lua_register(lua, "mi_setnodeprop", lua_setnodeprop);
  lua_register(lua, "mi_setblockprop", lua_setblockprop);
  lua_register(lua, "mi_setsegmentprop", lua_setsegmentprop);
  lua_register(lua, "mi_setarcsegmentprop", lua_setarcsegmentprop);
  lua_register(lua, "mi_deleteselected", lua_deleteselected);
  lua_register(lua, "mi_deleteselectednodes", lua_deleteselectednodes);
  lua_register(lua, "mi_deleteselectedlabels", lua_deleteselectedlabels);
  lua_register(lua, "mi_deleteselectedsegments", lua_deleteselectedsegments);
  lua_register(lua, "mi_deleteselectedarcsegments", lua_deleteselectedarcsegments);
  lua_register(lua, "mi_zoomnatural", lua_zoomnatural);
  lua_register(lua, "mi_zoomout", lua_zoomout);
  lua_register(lua, "mi_zoomin", lua_zoomin);
  lua_register(lua, "mi_zoom", lua_zoom);
  lua_register(lua, "mi_addmaterial", lua_addmatprop);
  lua_register(lua, "mi_addpointprop", lua_addpointprop);
  lua_register(lua, "mi_addcircprop", lua_addcircuitprop);
  lua_register(lua, "mi_addboundprop", lua_addboundprop);
  lua_register(lua, "mi_modifymaterial", lua_modmatprop);
  lua_register(lua, "mi_modifyboundprop", lua_modboundprop);
  lua_register(lua, "mi_modifypointprop", lua_modpointprop);
  lua_register(lua, "mi_modifycircprop", lua_modcircprop);
  lua_register(lua, "mi_deletematerial", lua_delmatprop);
  lua_register(lua, "mi_deleteboundprop", lua_delboundprop);
  lua_register(lua, "mi_deletecircuit", lua_delcircuitprop);
  lua_register(lua, "mi_deletepointprop", lua_delpointprop);
  lua_register(lua, "mi_moverotate", lua_move_rotate);
  lua_register(lua, "mi_movetranslate", lua_move_translate);
  lua_register(lua, "mi_copyrotate", lua_copy_rotate);
  lua_register(lua, "mi_copytranslate", lua_copy_translate);
  lua_register(lua, "mi_mirror", lua_mirror);
  lua_register(lua, "mi_scale", lua_scale);
  lua_register(lua, "mi_seteditmode", lua_seteditmode);
  lua_register(lua, "mi_selectgroup", lua_selectgroup);
  lua_register(lua, "mi_newdocument", lua_newdocument);
  lua_register(lua, "mi_savebitmap", lua_savebitmap);
  lua_register(lua, "mi_savepng", lua_savepng);
  lua_register(lua, "mi_save_png", lua_savepng);
  lua_register(lua, "mi_savemetafile", lua_saveWMF);
  lua_register(lua, "mi_close", lua_exitpre);
  lua_register(lua, "mi_addbhpoint", lua_addbhpoint);
  lua_register(lua, "mi_clearbhpoints", lua_clearbhpoints);
  lua_register(lua, "mi_refreshview", lua_updatewindow);
  lua_register(lua, "mi_setredraw", lua_setredraw);
  lua_register(lua, "mi_setgpuaccel", lua_setgpuaccel);
  // Both spellings, as every other command in this file has: FEMM's
  // manual promises an underscore-separated form for each name, and
  // these two fork-added commands only ever registered one (#19).
  lua_register(lua, "mi_set_redraw", lua_setredraw);
  lua_register(lua, "mi_set_gpuaccel", lua_setgpuaccel);
  lua_register(lua, "mi_shownames", lua_shownames);
  lua_register(lua, "mi_showgrid", lua_showgrid);
  lua_register(lua, "mi_hidegrid", lua_hidegrid);
  lua_register(lua, "mi_gridsnap", lua_gridsnap);
  lua_register(lua, "mi_setgrid", lua_setgrid);
  lua_register(lua, "mi_setfocus", lua_switchfocus);
  lua_register(lua, "mi_readdxf", lua_readdxf);
  lua_register(lua, "mi_savedxf", lua_savedxf);
  lua_register(lua, "mi_defineouterspace", lua_defineouterspace);
  lua_register(lua, "mi_attachouterspace", lua_attachouterspace);
  lua_register(lua, "mi_detachouterspace", lua_detachouterspace);
  lua_register(lua, "mi_attachdefault", lua_attachdefault);
  lua_register(lua, "mi_detachdefault", lua_detachdefault);
  lua_register(lua, "mi_attach_default", lua_attachdefault);
  lua_register(lua, "mi_detach_default", lua_detachdefault);
  lua_register(lua, "mi_resize", luaResize);
  lua_register(lua, "mi_minimize", luaMinimize);
  lua_register(lua, "mi_maximize", luaMaximize);
  lua_register(lua, "mi_restore", luaRestore);
  lua_register(lua, "mi_createradius", lua_createradius);
  lua_register(lua, "mi_gettitle", lua_gettitle);
  lua_register(lua, "mi_setgroup", lua_setgroup);
  lua_register(lua, "mi_getmaterial", lua_getmaterial);
  lua_register(lua, "mi_getprobleminfo", lua_getprobleminfo);
  lua_register(lua, "mi_getboundingbox", lua_getboundingbox);
  lua_register(lua, "mi_selectcircle", lua_selectcircle);
  lua_register(lua, "mi_selectrectangle", lua_selectrectangle);
  lua_register(lua, "mi_setprevious", lua_previous);
  lua_register(lua, "mi_setcomment", lua_comment);

  // compatibility lua function names
  lua_register(lua, "mi_select_rectangle", lua_selectrectangle);
  lua_register(lua, "mi_select_circle", lua_selectcircle);
  lua_register(lua, "mi_set_group", lua_setgroup);
  lua_register(lua, "mi_get_title", lua_gettitle);
  lua_register(lua, "mi_define_outer_space", lua_defineouterspace);
  lua_register(lua, "mi_attach_outer_space", lua_attachouterspace);
  lua_register(lua, "mi_detach_outer_space", lua_detachouterspace);
  lua_register(lua, "mi_set_focus", lua_switchfocus);
  lua_register(lua, "mi_save_as", luaSaveDocument);
  lua_register(lua, "mi_create_mesh", lua_create_mesh);
  lua_register(lua, "mi_show_mesh", lua_show_mesh);
  lua_register(lua, "mi_purge_mesh", lua_purge_mesh);
  lua_register(lua, "mi_prob_def", lua_prob_def);
  lua_register(lua, "mi_analyze", lua_analyze);
  lua_register(lua, "mi_load_solution", lua_runpost);
  lua_register(lua, "mi_add_node", lua_addnode);
  lua_register(lua, "mi_add_block_label", lua_addlabel);
  lua_register(lua, "mi_add_segment", lua_addline);
  lua_register(lua, "mi_add_arc", lua_addarc);
  lua_register(lua, "mi_select_node", lua_selectnode);
  lua_register(lua, "mi_select_label", lua_selectlabel);
  lua_register(lua, "mi_select_segment", lua_selectsegment);
  lua_register(lua, "mi_select_arcsegment", lua_selectarcsegment);
  lua_register(lua, "mi_clear_selected", lua_clearselected);
  lua_register(lua, "mi_set_node_prop", lua_setnodeprop);
  lua_register(lua, "mi_set_block_prop", lua_setblockprop);
  lua_register(lua, "mi_set_segment_prop", lua_setsegmentprop);
  lua_register(lua, "mi_set_arcsegment_prop", lua_setarcsegmentprop);
  lua_register(lua, "mi_delete_selected", lua_deleteselected);
  lua_register(lua, "mi_delete_selected_nodes", lua_deleteselectednodes);
  lua_register(lua, "mi_delete_selected_labels", lua_deleteselectedlabels);
  lua_register(lua, "mi_delete_selected_segments", lua_deleteselectedsegments);
  lua_register(lua, "mi_delete_selected_arcsegments", lua_deleteselectedarcsegments);
  lua_register(lua, "mi_zoom_natural", lua_zoomnatural);
  lua_register(lua, "mi_zoom_out", lua_zoomout);
  lua_register(lua, "mi_zoom_in", lua_zoomin);
  lua_register(lua, "mi_add_material", lua_addmatprop);
  lua_register(lua, "mi_add_point_prop", lua_addpointprop);
  lua_register(lua, "mi_add_circ_prop", lua_addcircuitprop);
  lua_register(lua, "mi_add_bound_prop", lua_addboundprop);
  lua_register(lua, "mi_modify_material", lua_modmatprop);
  lua_register(lua, "mi_modify_bound_prop", lua_modboundprop);
  lua_register(lua, "mi_modify_point_prop", lua_modpointprop);
  lua_register(lua, "mi_modify_circ_prop", lua_modcircprop);
  lua_register(lua, "mi_delete_material", lua_delmatprop);
  lua_register(lua, "mi_delete_bound_prop", lua_delboundprop);
  lua_register(lua, "mi_delete_circuit", lua_delcircuitprop);
  lua_register(lua, "mi_delete_point_prop", lua_delpointprop);
  lua_register(lua, "mi_move_rotate", lua_move_rotate);
  lua_register(lua, "mi_move_translate", lua_move_translate);
  lua_register(lua, "mi_copy_rotate", lua_copy_rotate);
  lua_register(lua, "mi_copy_translate", lua_copy_translate);
  lua_register(lua, "mi_set_edit_mode", lua_seteditmode);
  lua_register(lua, "mi_select_group", lua_selectgroup);
  lua_register(lua, "mi_new_document", lua_newdocument);
  lua_register(lua, "mi_save_bitmap", lua_savebitmap);
  lua_register(lua, "mi_save_metafile", lua_saveWMF);
  lua_register(lua, "mi_add_bh_point", lua_addbhpoint);
  lua_register(lua, "mi_clear_bh_points", lua_clearbhpoints);
  lua_register(lua, "mi_refresh_view", lua_updatewindow);
  lua_register(lua, "mi_show_grid", lua_showgrid);
  lua_register(lua, "mi_hide_grid", lua_hidegrid);
  lua_register(lua, "mi_grid_snap", lua_gridsnap);
  lua_register(lua, "mi_set_grid", lua_setgrid);
  lua_register(lua, "mi_show_names", lua_shownames);
  lua_register(lua, "mi_read_dxf", lua_readdxf);
  lua_register(lua, "mi_save_dxf", lua_savedxf);
  lua_register(lua, "mi_create_radius", lua_createradius);
  lua_register(lua, "mi_get_material", lua_getmaterial);

  pFemmeDoc = (CFemmeDoc*)this;
}

int CFemmeDoc::lua_switchfocus(lua_State* L)
{
  POSITION tpos, dpos;
  CDocTemplate* pTemp;
  CFemmeDoc* pDoc;
  CString DocTitle, ThisTitle;
  int n;

  // get title of desired document from Lua
  n = lua_gettop(L);
  if (n == 0)
    return NULL;
  DocTitle.Format("%s", lua_tostring(L, n));
  DocTitle.MakeLower();
  if (DocTitle.Right(4) == ".fem")
    DocTitle = DocTitle.Left(DocTitle.GetLength() - 4);

  // get pointer to document template for FemmeDoc
  tpos = AfxGetApp()->GetFirstDocTemplatePosition();
  pTemp = AfxGetApp()->GetNextDocTemplate(tpos);

  // leaf through documents to get a pointer to the
  // document with the right title
  dpos = pTemp->GetFirstDocPosition();
  while (dpos != NULL) {
    pDoc = (CFemmeDoc*)pTemp->GetNextDoc(dpos);
    ThisTitle = pDoc->GetTitle();
    ThisTitle.MakeLower();
    if (ThisTitle.Right(4) == ".fem")
      ThisTitle = ThisTitle.Left(ThisTitle.GetLength() - 4);
    if (ThisTitle == DocTitle) {
      pFemmeDoc = pDoc;
      return NULL;
    }
  }

  // if we can't find it, throw an error message
  CString msg;
  msg.Format("No document that matches %s", DocTitle);
  lua_error(L, msg.GetBuffer(1));
  return NULL;
}

int CFemmeDoc::lua_exitpre(lua_State* L)
{
  CatchNullDocument();
  ((CFemmeDoc*)pFemmeDoc)->OnCloseDocument();

  return 0;
}

int CFemmeDoc::lua_readdxf(lua_State* L)
{
  CatchNullDocument();
  CFemmeDoc* thisDoc;
  CFemmeView* theView;

  thisDoc = (CFemmeDoc*)pFemmeDoc;
  POSITION pos;
  pos = thisDoc->GetFirstViewPosition();
  theView = (CFemmeView*)thisDoc->GetNextView(pos);

  int n;
  CString DocTitle;
  double DefTol;
  BOOL result;

  // get title of desired document from Lua
  n = lua_gettop(L);
  if (n == 0)
    return FALSE;
  DocTitle.Format("%s", lua_tostring(L, 1));
  if (n == 2)
    DefTol = lua_todouble(L, 2);
  else
    DefTol = 0;

  result = thisDoc->ReadDXF(DocTitle, DefTol);
  if (result)
    theView->InvalidateRect(NULL);

  return result;
}

int CFemmeDoc::lua_savedxf(lua_State* L)
{
  CatchNullDocument();
  CFemmeDoc* thisDoc;
  CFemmeView* theView;

  thisDoc = (CFemmeDoc*)pFemmeDoc;
  POSITION pos;
  pos = thisDoc->GetFirstViewPosition();
  theView = (CFemmeView*)thisDoc->GetNextView(pos);

  int n;
  CString DocTitle;
  BOOL result;

  // get title of desired document from Lua
  n = lua_gettop(L);
  if (n == 0)
    return FALSE;
  DocTitle.Format("%s", lua_tostring(L, 1));

  result = thisDoc->WriteDXF(DocTitle);
  if (result)
    theView->InvalidateRect(NULL);

  return result;
}

int CFemmeDoc::luaSaveDocument(lua_State* L)
{
  CatchNullDocument();
  CFemmeDoc* thisDoc;
  thisDoc = (CFemmeDoc*)pFemmeDoc;
  int n;
  n = lua_gettop(L);

  CString temp;
  temp.Format("%s", lua_tostring(L, n));
  thisDoc->OnSaveDocument(temp);
  thisDoc->SetPathName(temp);

  return 0;
}

int CFemmeDoc::lua_previous(lua_State* L)
{
  CatchNullDocument();
  CFemmeDoc* thisDoc;
  thisDoc = (CFemmeDoc*)pFemmeDoc;
  int n;
  n = lua_gettop(L);

  CString PrevSoln;
  if (n > 0) {
    PrevSoln.Format("%s", lua_tostring(L, 1));
    thisDoc->PrevSoln = PrevSoln;
  }

  if (n > 1)
    thisDoc->PrevType = (int)lua_todouble(L, 2);
  else
    thisDoc->PrevType = 0;

  return 0;
}

int CFemmeDoc::lua_comment(lua_State* L)
{
  CatchNullDocument();
  CFemmeDoc* thisDoc;
  thisDoc = (CFemmeDoc*)pFemmeDoc;
  int n;
  n = lua_gettop(L);

  if (n > 0) {
    CString myComment;
    myComment.Format("%s", lua_tostring(L, 1));
    thisDoc->ProblemNote = myComment;
  }

  return 0;
}

int CFemmeDoc::lua_prob_def(lua_State* L)
{
  CatchNullDocument();
  CFemmeDoc* thisDoc;
  thisDoc = (CFemmeDoc*)pFemmeDoc;

  CString units, type;
  int n;
  n = lua_gettop(L);

  // error traps
  int LengthUnits = -1;
  int ProblemType = -1;
  double Frequency;
  double Precision;
  double MinAngle = -1;
  int ACSolver = -1;

  // Frequency
  Frequency = fabs(lua_todouble(L, 1));
  thisDoc->Frequency = fabs(Frequency);
  if (n == 1)
    return 0;

  // Length Units
  units.Format("%s", lua_tostring(L, 2));
  if (units == "inches")
    LengthUnits = 0;
  if (units == "millimeters")
    LengthUnits = 1;
  if (units == "centimeters")
    LengthUnits = 2;
  if (units == "meters")
    LengthUnits = 3;
  if (units == "mills")
    LengthUnits = 4;
  if (units == "mils")
    LengthUnits = 4;
  if (units == "micrometers")
    LengthUnits = 5;
  if (LengthUnits == -1) {
    CString msg;
    msg.Format("Unknown length unit %s", units);
    lua_error(L, msg.GetBuffer(1));
    return 0;
  } else {
    thisDoc->LengthUnits = LengthUnits;
    if (n == 2)
      return 0;
  }

  // Problem type
  type.Format("%s", lua_tostring(L, 3));
  if (type == "planar")
    ProblemType = 0;
  if (type == "axi")
    ProblemType = 1;
  if (ProblemType == -1) {
    CString msg;
    msg.Format("Unknown problem type %s", type);
    lua_error(L, msg.GetBuffer(1));
    return 0;

  } else {
    thisDoc->ProblemType = ProblemType;
    if (n == 3)
      return 0;
  }

  // Changed to correct the precision rather than throwing a cryptic error
  Precision = lua_todouble(L, 4);
  if ((Precision == 0) || (Precision > 1.e-8))
    Precision = 1.e-8;
  if (Precision < 1.e-16)
    Precision = 1.e-16;
  thisDoc->Precision = Precision;
  if (n == 4)
    return 0;

  thisDoc->Depth = fabs(lua_todouble(L, 5));
  if (thisDoc->Depth <= 0)
    thisDoc->Depth = 1;
  if (n == 5)
    return 0;

  MinAngle = lua_todouble(L, 6);
  if ((MinAngle >= 1.) && (MinAngle <= MINANGLE_MAX)) {
    thisDoc->MinAngle = MinAngle;
  }
  if (n == 6)
    return 0;

  ACSolver = (int)lua_todouble(L, 7);
  if ((ACSolver == 0) || (ACSolver == 1)) {
    thisDoc->ACSolver = ACSolver;
  }

  return 0;
}

int CFemmeDoc::lua_create_mesh(lua_State* L)
{
  CatchNullDocument();
  CFemmeDoc* thisDoc;
  CFemmeView* theView;

  thisDoc = (CFemmeDoc*)pFemmeDoc;
  POSITION pos;
  pos = thisDoc->GetFirstViewPosition();
  theView = (CFemmeView*)thisDoc->GetNextView(pos);

  theView->lnuMakeMesh();

  return 1;
}

int CFemmeDoc::lua_smartmesh(lua_State* L)
{
  CatchNullDocument();
  CFemmeDoc* thisDoc;
  thisDoc = (CFemmeDoc*)pFemmeDoc;

  if (lua_gettop(L) != 0) {
    int k = (int)lua_todouble(L, 1);
    if (k != 0)
      k = 1;
    thisDoc->SmartMesh = k;
  }

  return 0;
}

int CFemmeDoc::lua_show_mesh(lua_State* L)
{
  CatchNullDocument();
  CFemmeDoc* thisDoc;
  CFemmeView* theView;

  thisDoc = (CFemmeDoc*)pFemmeDoc;
  POSITION pos;
  pos = thisDoc->GetFirstViewPosition();
  theView = (CFemmeView*)thisDoc->GetNextView(pos);

  theView->lnu_show_mesh();

  return 0;
}

int CFemmeDoc::lua_purge_mesh(lua_State* L)
{
  CatchNullDocument();
  CFemmeDoc* thisDoc;
  CFemmeView* theView;

  thisDoc = (CFemmeDoc*)pFemmeDoc;
  POSITION pos;
  pos = thisDoc->GetFirstViewPosition();
  theView = (CFemmeView*)thisDoc->GetNextView(pos);

  theView->lnu_purge_mesh();

  return 0;
}

int CFemmeDoc::lua_analyze(lua_State* L)
{
  CatchNullDocument();
  CFemmeDoc* thisDoc;
  CFemmeView* theView;

  thisDoc = (CFemmeDoc*)pFemmeDoc;
  POSITION pos;
  pos = thisDoc->GetFirstViewPosition();
  theView = (CFemmeView*)thisDoc->GetNextView(pos);

  int n = lua_gettop(L);
  int bHide = 0;
  if ((n == 0) && (theApp.GetMainWnd()->GetStyle() & WS_MINIMIZE))
    bHide = 1;
  if (n > 0)
    bHide = (int)lua_todouble(L, 1);
  if (bHide != 0)
    bHide = 1;

  theView->lnu_analyze(bHide);

  return 0;
}

int CFemmeDoc::lua_runpost(lua_State* L)
{
  CatchNullDocument();
  CFemmeDoc* thisDoc = (CFemmeDoc*)pFemmeDoc;
  CString pn = thisDoc->GetPathName();

  if (pn.GetLength() == 0) {
    CString msg;
    msg.Format("No results to display");
    lua_error(L, msg.GetBuffer(1));
    return 0;
  }

  CString rootname = "\"" + pn.Left(pn.ReverseFind('.')) + ".ans\"";
  if (((CFemmApp*)AfxGetApp())->MOCheckIfAlreadyOpen(rootname) == FALSE)
    AfxGetApp()->OpenDocumentFile(rootname);

  return 0;
}

int CFemmeDoc::lua_addnode(lua_State* L)
{
  CatchNullDocument();
  CFemmeDoc* thisDoc;
  CFemmeView* theView;
  double x, y, d;

  thisDoc = (CFemmeDoc*)pFemmeDoc;
  POSITION pos;
  pos = thisDoc->GetFirstViewPosition();

  theView = (CFemmeView*)thisDoc->GetNextView(pos);

  x = lua_todouble(L, 1);
  y = lua_todouble(L, 2);

  //	if(thisDoc->Coords)
  //	{
  //		double r,t;
  //		r=mx;
  //		t=my*PI/180;
  //		x=mx*cos(t);
  //		y=mx*sin(t);
  //	}

  if (thisDoc->nodelist.GetSize() < 2)
    d = 1.e-08;
  else {
    CComplex p0, p1, p2;
    p0 = thisDoc->nodelist[0].CC();
    p1 = p0;
    for (int i = 1; i < thisDoc->nodelist.GetSize(); i++) {
      p2 = thisDoc->nodelist[i].CC();
      if (p2.re < p0.re)
        p0.re = p2.re;
      if (p2.re > p1.re)
        p1.re = p2.re;
      if (p2.im < p0.im)
        p0.im = p2.im;
      if (p2.im > p1.im)
        p1.im = p2.im;
    }
    d = abs(p1 - p0) * CLOSE_ENOUGH;
  }
  BOOL flag;
  flag = thisDoc->AddNode(x, y, d);

  if (flag == TRUE) {
    theView->MeshUpToDate = FALSE;
    if (theView->MeshFlag == TRUE)
      theView->lnu_show_mesh();
    else
      theView->DrawPSLG();
  }

  return 0;
}

int CFemmeDoc::lua_addlabel(lua_State* L)
{
  CatchNullDocument();
  CFemmeDoc* thisDoc;
  CFemmeView* theView;
  double x, y, d;

  x = lua_todouble(L, 1);
  y = lua_todouble(L, 2);

  thisDoc = (CFemmeDoc*)pFemmeDoc;
  POSITION pos;
  pos = thisDoc->GetFirstViewPosition();
  theView = (CFemmeView*)thisDoc->GetNextView(pos);

  //	if(thisDoc->Coords)
  //	{
  //		double r,t;
  //		r=mx;
  //		t=my*PI/180;
  //		x=mx*cos(t);
  //		y=mx*sin(t);
  //	}

  if (thisDoc->nodelist.GetSize() < 2)
    d = 1.e-08;
  else {
    CComplex p0, p1, p2;
    p0 = thisDoc->nodelist[0].CC();
    p1 = p0;
    for (int i = 1; i < thisDoc->nodelist.GetSize(); i++) {
      p2 = thisDoc->nodelist[i].CC();
      if (p2.re < p0.re)
        p0.re = p2.re;
      if (p2.re > p1.re)
        p1.re = p2.re;
      if (p2.im < p0.im)
        p0.im = p2.im;
      if (p2.im > p1.im)
        p1.im = p2.im;
    }
    d = abs(p1 - p0) * CLOSE_ENOUGH;
  }
  BOOL flag;
  flag = thisDoc->AddBlockLabel(x, y, d);

  if (flag == TRUE) {
    theView->MeshUpToDate = FALSE;
    if (theView->MeshFlag == TRUE)
      theView->lnu_show_mesh();
    else
      theView->DrawPSLG();
  }

  return 0;
}

int CFemmeDoc::lua_addline(lua_State* L)
{
  CatchNullDocument();
  CFemmeDoc* thisDoc;
  CFemmeView* theView;

  double sx, sy, ex, ey;

  sx = lua_todouble(L, 1);
  sy = lua_todouble(L, 2);

  ex = lua_todouble(L, 3);
  ey = lua_todouble(L, 4);

  thisDoc = (CFemmeDoc*)pFemmeDoc;
  POSITION pos;
  pos = thisDoc->GetFirstViewPosition();

  theView = (CFemmeView*)thisDoc->GetNextView(pos);
  BOOL flag;

  flag = thisDoc->AddSegment(thisDoc->ClosestNode(sx, sy), thisDoc->ClosestNode(ex, ey));

  if (flag == TRUE) {
    theView->MeshUpToDate = FALSE;
    if (theView->MeshFlag == TRUE)
      theView->lnu_show_mesh();
    else
      theView->DrawPSLG();
  } else
    theView->DrawPSLG();

  return 0;
}

int CFemmeDoc::lua_addarc(lua_State* L)
{
  CatchNullDocument();
  CFemmeDoc* thisDoc;
  CFemmeView* theView;

  double sx, sy, ex, ey;
  double angle, maxseg;

  sx = lua_todouble(L, 1);
  sy = lua_todouble(L, 2);
  ex = lua_todouble(L, 3);
  ey = lua_todouble(L, 4);

  angle = lua_todouble(L, 5);
  maxseg = lua_todouble(L, 6);

  thisDoc = (CFemmeDoc*)pFemmeDoc;
  POSITION pos;
  pos = thisDoc->GetFirstViewPosition();

  theView = (CFemmeView*)thisDoc->GetNextView(pos);
  BOOL flag;

  CArcSegment asegm;
  asegm.n0 = thisDoc->ClosestNode(sx, sy);
  asegm.n1 = thisDoc->ClosestNode(ex, ey);
  thisDoc->nodelist[asegm.n1].ToggleSelect();
  theView->DrawPSLG();

  asegm.MaxSideLength = maxseg;
  asegm.ArcLength = angle;
  asegm.BoundaryMarker = "<None>";

  flag = thisDoc->AddArcSegment(asegm);
  flag = FALSE;
  thisDoc->UnselectAll();
  if (flag == TRUE) {
    theView->MeshUpToDate = FALSE;
    if (theView->MeshFlag == TRUE)
      theView->lnu_show_mesh();
    else
      theView->DrawPSLG();
  } else
    theView->DrawPSLG();

  return 0;
}

int CFemmeDoc::lua_selectnode(lua_State* L)
{
  CatchNullDocument();
  CFemmeDoc* thisDoc;
  CFemmeView* theView;

  double mx, my;
  mx = lua_todouble(L, 1);
  my = lua_todouble(L, 2);
  thisDoc = (CFemmeDoc*)pFemmeDoc;
  POSITION pos;
  pos = thisDoc->GetFirstViewPosition();
  theView = (CFemmeView*)thisDoc->GetNextView(pos);

  int node;
  if (thisDoc->nodelist.GetSize() == 0)
    return 0;
  node = thisDoc->ClosestNode(mx, my);
  thisDoc->nodelist[node].ToggleSelect();

  lua_pushnumber(L, thisDoc->nodelist[node].x);
  lua_pushnumber(L, thisDoc->nodelist[node].y);

  return 2;
}

int CFemmeDoc::lua_selectlabel(lua_State* L)
{
  CatchNullDocument();
  CFemmeDoc* thisDoc;
  CFemmeView* theView;

  double mx, my;
  mx = lua_todouble(L, 1);
  my = lua_todouble(L, 2);
  thisDoc = (CFemmeDoc*)pFemmeDoc;
  POSITION pos;
  pos = thisDoc->GetFirstViewPosition();
  theView = (CFemmeView*)thisDoc->GetNextView(pos);

  int node;
  if (thisDoc->blocklist.GetSize() == 0)
    return 0;
  node = thisDoc->ClosestBlockLabel(mx, my);
  thisDoc->blocklist[node].ToggleSelect();

  lua_pushnumber(L, thisDoc->blocklist[node].x);
  lua_pushnumber(L, thisDoc->blocklist[node].y);

  return 2;
}

int CFemmeDoc::lua_selectsegment(lua_State* L)
{
  CatchNullDocument();
  CFemmeDoc* thisDoc;
  CFemmeView* theView;

  double mx, my;
  mx = lua_todouble(L, 1);
  my = lua_todouble(L, 2);
  thisDoc = (CFemmeDoc*)pFemmeDoc;
  POSITION pos;
  pos = thisDoc->GetFirstViewPosition();
  theView = (CFemmeView*)thisDoc->GetNextView(pos);

  int node;
  if (thisDoc->linelist.GetSize() == 0)
    return 0;
  node = thisDoc->ClosestSegment(mx, my);
  thisDoc->linelist[node].ToggleSelect();

  lua_pushnumber(L, thisDoc->nodelist[thisDoc->linelist[node].n0].x);
  lua_pushnumber(L, thisDoc->nodelist[thisDoc->linelist[node].n0].y);
  lua_pushnumber(L, thisDoc->nodelist[thisDoc->linelist[node].n1].x);
  lua_pushnumber(L, thisDoc->nodelist[thisDoc->linelist[node].n1].y);

  return 4;
}

int CFemmeDoc::lua_selectarcsegment(lua_State* L)
{
  CatchNullDocument();
  CFemmeDoc* thisDoc;
  CFemmeView* theView;

  double mx, my;
  mx = lua_todouble(L, 1);
  my = lua_todouble(L, 2);
  thisDoc = (CFemmeDoc*)pFemmeDoc;
  POSITION pos;
  pos = thisDoc->GetFirstViewPosition();
  theView = (CFemmeView*)thisDoc->GetNextView(pos);

  int node;
  if (thisDoc->arclist.GetSize() == 0)
    return 0;
  node = thisDoc->ClosestArcSegment(mx, my);
  thisDoc->arclist[node].ToggleSelect();

  lua_pushnumber(L, thisDoc->nodelist[thisDoc->arclist[node].n0].x);
  lua_pushnumber(L, thisDoc->nodelist[thisDoc->arclist[node].n0].y);
  lua_pushnumber(L, thisDoc->nodelist[thisDoc->arclist[node].n1].x);
  lua_pushnumber(L, thisDoc->nodelist[thisDoc->arclist[node].n1].y);

  return 4;
}

int CFemmeDoc::lua_clearselected(lua_State* L)
{
  CatchNullDocument();
  CFemmeDoc* thisDoc;
  CFemmeView* theView;
  thisDoc = (CFemmeDoc*)pFemmeDoc;
  POSITION pos;
  pos = thisDoc->GetFirstViewPosition();
  theView = (CFemmeView*)thisDoc->GetNextView(pos);

  thisDoc->UnselectAll();
  return 0;
}

int CFemmeDoc::lua_setnodeprop(lua_State* L)
{
  CatchNullDocument();
  CString nodeprop;
  int groupno;

  nodeprop.Format("%s", lua_tostring(L, 1));
  groupno = (int)lua_todouble(L, 2);

  if (groupno < 0) {
    CString msg;
    msg.Format("Invalid group no %d", groupno);
    lua_error(L, msg.GetBuffer(1));
    return 0;
  }

  CFemmeDoc* thisDoc = (CFemmeDoc*)pFemmeDoc;
  int i;

  // check to see how many (if any) nodes are selected.
  for (i = 0; i < thisDoc->nodelist.GetSize(); i++) {
    if (thisDoc->nodelist[i].IsSelected == TRUE) {
      thisDoc->nodelist[i].InGroup = groupno;
      thisDoc->nodelist[i].BoundaryMarker = nodeprop;
    }
  }

  return 0;
}

int CFemmeDoc::lua_setblockprop(lua_State* L)
{
  CatchNullDocument();
  CString blocktype, incircuit, magdirfctn;
  BOOL automesh;
  double meshsize, magdirection;
  int group, turns;

  int n = lua_gettop(L);

  blocktype = "<None>";
  automesh = 1;
  incircuit = "<None>";
  magdirection = 0;
  magdirfctn.Empty();
  group = 0;
  turns = 1;

  if (n > 0)
    blocktype.Format("%s", lua_tostring(L, 1));
  if (n > 1)
    automesh = (int)lua_todouble(L, 2);
  if (n > 2)
    meshsize = lua_todouble(L, 3);
  if (n > 3)
    incircuit.Format("%s", lua_tostring(L, 4));
  if (n > 4) {
    if (lua_isnumber(L, 5))
      magdirection = lua_todouble(L, 5);
    else
      magdirfctn.Format("%s", lua_tostring(L, 5));
  }
  if (n > 5)
    group = (int)lua_todouble(L, 6);
  if (n > 6) {
    turns = (int)lua_todouble(L, 7);
    if (turns == 0)
      turns = 1;
  }

  CFemmeDoc* thisDoc = (CFemmeDoc*)pFemmeDoc;
  int i;

  for (i = 0; i < thisDoc->blocklist.GetSize(); i++) {
    if (thisDoc->blocklist[i].IsSelected == TRUE) {
      thisDoc->blocklist[i].MaxArea = PI * meshsize * meshsize / 4.;
      thisDoc->blocklist[i].MagDir = magdirection;
      thisDoc->blocklist[i].BlockType = blocktype;
      thisDoc->blocklist[i].InCircuit = incircuit;
      thisDoc->blocklist[i].InGroup = group;
      thisDoc->blocklist[i].Turns = turns;
      thisDoc->blocklist[i].MagDirFctn = magdirfctn;
      if (automesh == 1)
        thisDoc->blocklist[i].MaxArea = 0;
    }
  }

  return 0;
}

int CFemmeDoc::lua_setsegmentprop(lua_State* L)
{
  CatchNullDocument();
  CString prop;
  double elesize;
  int automesh, hide, group;

  prop.Format("%s", lua_tostring(L, 1));
  elesize = lua_todouble(L, 2);
  automesh = (int)lua_todouble(L, 3);
  hide = (int)lua_todouble(L, 4);
  group = (int)lua_todouble(L, 5);

  CFemmeDoc* thisDoc = (CFemmeDoc*)pFemmeDoc;

  for (int i = 0; i < thisDoc->linelist.GetSize(); i++) {
    if (thisDoc->linelist[i].IsSelected == TRUE) {
      if (automesh == 1)
        thisDoc->linelist[i].MaxSideLength = -1;
      else {
        if (elesize > 0)
          thisDoc->linelist[i].MaxSideLength = elesize;
        else
          elesize = -1;
      }
      thisDoc->linelist[i].BoundaryMarker = prop;
      thisDoc->linelist[i].Hidden = hide;
      thisDoc->linelist[i].InGroup = group;
    }
  }

  return 0;
}

int CFemmeDoc::lua_setarcsegmentprop(lua_State* L)
{
  CatchNullDocument();
  CString boundprop;
  double maxsegdeg;
  int hide, group;

  maxsegdeg = lua_todouble(L, 1);
  if (maxsegdeg > 10)
    maxsegdeg = 10;
  if (maxsegdeg <= 0)
    maxsegdeg = 1;
  boundprop.Format("%s", lua_tostring(L, 2));
  hide = (int)lua_todouble(L, 3);
  group = (int)lua_todouble(L, 4);

  CFemmeDoc* thisDoc = (CFemmeDoc*)pFemmeDoc;
  int i;

  for (i = 0; i < thisDoc->arclist.GetSize(); i++) {
    if (thisDoc->arclist[i].IsSelected == TRUE) {
      thisDoc->arclist[i].BoundaryMarker = boundprop;
      thisDoc->arclist[i].MaxSideLength = maxsegdeg;
      thisDoc->arclist[i].Hidden = hide;
      thisDoc->arclist[i].InGroup = group;
    }
  }

  return 0;
}

int CFemmeDoc::lua_deleteselectednodes(lua_State* L)
{
  CatchNullDocument();
  CFemmeDoc* thisDoc;
  thisDoc = (CFemmeDoc*)pFemmeDoc;
  thisDoc->DeleteSelectedNodes();
  return 0;
}

int CFemmeDoc::lua_deleteselectedlabels(lua_State* L)
{
  CatchNullDocument();
  CFemmeDoc* thisDoc;
  thisDoc = (CFemmeDoc*)pFemmeDoc;
  thisDoc->DeleteSelectedBlockLabels();
  return 0;
}

int CFemmeDoc::lua_deleteselectedsegments(lua_State* L)
{
  CatchNullDocument();
  CFemmeDoc* thisDoc;
  thisDoc = (CFemmeDoc*)pFemmeDoc;
  thisDoc->DeleteSelectedSegments();
  return 0;
}

int CFemmeDoc::lua_deleteselectedarcsegments(lua_State* L)
{
  CatchNullDocument();
  CFemmeDoc* thisDoc;
  thisDoc = (CFemmeDoc*)pFemmeDoc;
  thisDoc->DeleteSelectedArcSegments();
  return 0;
}

int CFemmeDoc::lua_deleteselected(lua_State* L)
{
  CatchNullDocument();
  CFemmeDoc* thisDoc;
  thisDoc = (CFemmeDoc*)pFemmeDoc;

  thisDoc->DeleteSelectedSegments();
  thisDoc->DeleteSelectedArcSegments();
  thisDoc->DeleteSelectedNodes();
  thisDoc->DeleteSelectedBlockLabels();

  return 0;
}

int CFemmeDoc::lua_newdocument(lua_State* L)
{
  CatchNullDocument();
  CFemmeDoc* thisDoc;
  thisDoc = (CFemmeDoc*)pFemmeDoc;
  thisDoc->OnNewDocument();
  thisDoc->SetPathName("Untitled", FALSE);
  thisDoc->SetTitle("Untitled");
  return 0;
}

int CFemmeDoc::lua_zoomnatural(lua_State* L)
{
  CatchNullDocument();
  CFemmeDoc* thisDoc;
  CFemmeView* theView;
  thisDoc = (CFemmeDoc*)pFemmeDoc;
  POSITION pos;
  pos = thisDoc->GetFirstViewPosition();
  theView = (CFemmeView*)thisDoc->GetNextView(pos);
  theView->lua_zoomnatural();

  return 0;
}

int CFemmeDoc::lua_zoomout(lua_State* L)
{
  CatchNullDocument();
  CFemmeDoc* thisDoc;
  CFemmeView* theView;
  thisDoc = (CFemmeDoc*)pFemmeDoc;
  POSITION pos;
  pos = thisDoc->GetFirstViewPosition();
  theView = (CFemmeView*)thisDoc->GetNextView(pos);

  theView->lua_zoomout();

  return 0;
}

int CFemmeDoc::lua_zoomin(lua_State* L)
{
  CatchNullDocument();
  CFemmeDoc* thisDoc;
  CFemmeView* theView;
  thisDoc = (CFemmeDoc*)pFemmeDoc;
  POSITION pos;
  pos = thisDoc->GetFirstViewPosition();
  theView = (CFemmeView*)thisDoc->GetNextView(pos);
  theView->lua_zoomin();

  //	PostMessage(theView->m_hWnd,WM_COMMAND,0,ID_ZOOM_IN);
  // it would be nice to use messages but I need to check the format first
  // this would cut down on code used twice and some unnecessary code !

  return 0;
}

int CFemmeDoc::lua_zoom(lua_State* L)
{
  CatchNullDocument();

  double x[2], y[2], m[2];

  x[0] = lua_todouble(L, 1);
  y[0] = lua_todouble(L, 2);
  x[1] = lua_todouble(L, 3);
  y[1] = lua_todouble(L, 4);

  CFemmeDoc* thisDoc;
  CFemmeView* theView;
  thisDoc = (CFemmeDoc*)pFemmeDoc;
  POSITION pos;
  pos = thisDoc->GetFirstViewPosition();
  theView = (CFemmeView*)thisDoc->GetNextView(pos);

  CRect r;
  theView->ox = x[0];
  theView->oy = y[0];
  theView->GetClientRect(&r);
  m[0] = ((double)(r.right - 1)) / (x[1] - x[0]);
  m[1] = ((double)(r.bottom - 1)) / (y[1] - y[0]);

  if (m[0] < m[1])
    theView->mag = m[0];
  else
    theView->mag = m[1];

  theView->Invalidate(TRUE);
  return 0;
}

int CFemmeDoc::lua_copy_rotate(lua_State* L)
{
  CatchNullDocument();
  CFemmeDoc* thisDoc;
  CFemmeView* theView;
  thisDoc = (CFemmeDoc*)pFemmeDoc;
  POSITION pos;
  pos = thisDoc->GetFirstViewPosition();
  theView = (CFemmeView*)thisDoc->GetNextView(pos);

  int n;
  n = lua_gettop(L);
  // IF N=5 WE Have an edit action, if n=4 we dont !

  int EditAction, copies;

  double x, y, angle;
  x = lua_todouble(L, 1);
  y = lua_todouble(L, 2);
  angle = lua_todouble(L, 3);
  copies = (int)lua_todouble(L, 4);

  if (n == 5)
    EditAction = (int)lua_todouble(L, 5);
  if (n == 4)
    EditAction = theView->EditAction;

  if (n != 4 && n != 5) {
    CString msg;
    msg.Format("Invalid number of parameters for copy rotate");
    lua_error(L, msg.GetBuffer(1));
    return 0;
  }

  thisDoc->RotateCopy(CComplex(x, y), angle, copies, EditAction);
  thisDoc->meshnode.RemoveAll();
  thisDoc->meshline.RemoveAll();
  thisDoc->greymeshline.RemoveAll();
  theView->MeshFlag = FALSE;
  theView->MeshUpToDate = FALSE;
  theView->InvalidateRect(NULL);

  return 0;
}

int CFemmeDoc::lua_copy_translate(lua_State* L)
{
  CatchNullDocument();
  CFemmeDoc* thisDoc;
  CFemmeView* theView;
  thisDoc = (CFemmeDoc*)pFemmeDoc;
  POSITION pos;
  pos = thisDoc->GetFirstViewPosition();
  theView = (CFemmeView*)thisDoc->GetNextView(pos);

  int n;
  n = lua_gettop(L);

  int EditAction, copies;
  double x, y;
  x = lua_todouble(L, 1);
  y = lua_todouble(L, 2);
  copies = (int)lua_todouble(L, 3);

  if (n == 4)
    EditAction = (int)lua_todouble(L, 4);
  if (n == 3)
    EditAction = theView->EditAction;

  if (n != 4 && n != 3) {
    CString msg;
    msg.Format("Invalid number of parameters for copy translate");
    lua_error(L, msg.GetBuffer(1));
    return 0;
  }

  thisDoc->UpdateUndo();
  thisDoc->TranslateCopy(x, y, copies, EditAction);
  thisDoc->meshnode.RemoveAll();
  thisDoc->meshline.RemoveAll();
  thisDoc->greymeshline.RemoveAll();
  theView->MeshFlag = FALSE;
  theView->MeshUpToDate = FALSE;
  theView->InvalidateRect(NULL);

  return 0;
}

int CFemmeDoc::lua_move_translate(lua_State* L)
{
  CatchNullDocument();

  double x, y;
  int EditAction;

  CFemmeDoc* thisDoc;
  CFemmeView* theView;
  thisDoc = (CFemmeDoc*)pFemmeDoc;
  POSITION pos;
  pos = thisDoc->GetFirstViewPosition();
  theView = (CFemmeView*)thisDoc->GetNextView(pos);

  int n;
  n = lua_gettop(L);

  x = lua_todouble(L, 1);
  y = lua_todouble(L, 2);

  if (n == 3)
    EditAction = (int)lua_todouble(L, 3);
  if (n == 2)
    EditAction = theView->EditAction;

  if (n != 3 && n != 2) {
    CString msg;
    msg.Format("Invalid number of parameters for move translate");
    lua_error(L, msg.GetBuffer(1));
    return 0;
  }

  {
    thisDoc->UpdateUndo();
    thisDoc->TranslateMove(x, y, EditAction);
    thisDoc->meshnode.RemoveAll();
    thisDoc->meshline.RemoveAll();
    thisDoc->greymeshline.RemoveAll();
    theView->MeshFlag = FALSE;
    theView->MeshUpToDate = FALSE;
    theView->InvalidateRect(NULL);
  }

  return 0;
}

int CFemmeDoc::lua_move_rotate(lua_State* L)
{
  CatchNullDocument();

  double x, y, shiftangle;
  int EditAction;

  int n;
  n = lua_gettop(L);

  CFemmeDoc* thisDoc;
  CFemmeView* theView;
  thisDoc = (CFemmeDoc*)pFemmeDoc;
  POSITION pos;
  pos = thisDoc->GetFirstViewPosition();
  theView = (CFemmeView*)thisDoc->GetNextView(pos);

  x = lua_todouble(L, 1);
  y = lua_todouble(L, 2);
  shiftangle = lua_todouble(L, 3);

  if (n == 4)
    EditAction = (int)lua_todouble(L, 4);
  if (n == 3)
    EditAction = theView->EditAction;

  if (n != 4 && n != 3) {
    CString msg;
    msg.Format("Invalid number of parameters for move rotate");
    lua_error(L, msg.GetBuffer(1));
    return 0;
  }

  {
    thisDoc->UpdateUndo();
    thisDoc->RotateMove(CComplex(x, y), shiftangle, EditAction);
    thisDoc->meshnode.RemoveAll();
    thisDoc->meshline.RemoveAll();
    thisDoc->greymeshline.RemoveAll();
    theView->MeshFlag = FALSE;
    theView->MeshUpToDate = FALSE;
    theView->InvalidateRect(NULL);
  }

  return 0;
}

int CFemmeDoc::lua_mirror(lua_State* L)
{
  CatchNullDocument();
  double m_pax, m_pay, m_pbx, m_pby;
  int EditAction;

  CFemmeDoc* thisDoc;
  CFemmeView* theView;
  thisDoc = (CFemmeDoc*)pFemmeDoc;
  POSITION pos;
  pos = thisDoc->GetFirstViewPosition();
  theView = (CFemmeView*)thisDoc->GetNextView(pos);

  int n;
  n = lua_gettop(L);

  m_pax = lua_todouble(L, 1);
  m_pay = lua_todouble(L, 2);
  m_pbx = lua_todouble(L, 3);
  m_pby = lua_todouble(L, 4);

  if (n == 5)
    EditAction = (int)lua_todouble(L, 5);
  if (n == 4)
    EditAction = theView->EditAction;

  if (n != 4 && n != 5) {
    CString msg;
    msg.Format("Invalid number of parameters for mirror");
    lua_error(L, msg.GetBuffer(1));
    return 0;
  }

  thisDoc->UpdateUndo();
  thisDoc->MirrorSelected(m_pax, m_pay, m_pbx, m_pby, EditAction);
  theView->InvalidateRect(NULL);

  return 0;
}

int CFemmeDoc::lua_scale(lua_State* L)
{
  CatchNullDocument();
  int EditAction;
  double x, y, scalefactor;

  int n;
  n = lua_gettop(L);

  CFemmeDoc* thisDoc;
  CFemmeView* theView;
  thisDoc = (CFemmeDoc*)pFemmeDoc;
  POSITION pos;
  pos = thisDoc->GetFirstViewPosition();
  theView = (CFemmeView*)thisDoc->GetNextView(pos);

  x = lua_todouble(L, 1);
  y = lua_todouble(L, 2);
  scalefactor = lua_todouble(L, 3);
  EditAction = (int)lua_todouble(L, 4);

  if (n == 4)
    EditAction = (int)lua_todouble(L, 4);
  if (n == 3)
    EditAction = theView->EditAction;

  if (n != 4 && n != 3) {
    CString msg;
    msg.Format("Invalid number of parameters for scale");
    lua_error(L, msg.GetBuffer(1));
    return 0;
  }

  thisDoc->UpdateUndo();
  thisDoc->ScaleMove(x, y, scalefactor, EditAction);
  theView->InvalidateRect(NULL);

  return 0;
}

int CFemmeDoc::lua_seteditmode(lua_State* L)
{
  CatchNullDocument();
  CString EditAction;

  EditAction.Format("%s", lua_tostring(L, 1));
  EditAction.MakeLower();

  CFemmeDoc* thisDoc;
  CFemmeView* theView;
  thisDoc = (CFemmeDoc*)pFemmeDoc;
  POSITION pos;
  pos = thisDoc->GetFirstViewPosition();
  theView = (CFemmeView*)thisDoc->GetNextView(pos);

  int iEditAction;
  iEditAction = -1;

  if (EditAction == "nodes")
    iEditAction = 0;
  if (EditAction == "segments")
    iEditAction = 1;
  if (EditAction == "blocks")
    iEditAction = 2;
  if (EditAction == "arcsegments")
    iEditAction = 3;
  if (EditAction == "group")
    iEditAction = 4;

  if (iEditAction == -1) {
    CString msg;
    msg.Format("Invalid Edit Action %s", EditAction);
    lua_error(L, msg.GetBuffer(1));
    return 0;
  } else {
    theView->EditAction = iEditAction;
  }

  return 0;
}

int CFemmeDoc::lua_selectgroup(lua_State* L)
{
  CatchNullDocument();

  int group, i;
  group = (int)lua_todouble(L, 1);

  if (group < 0) {
    CString msg;
    msg.Format("Invalid group %d", group);
    lua_error(L, msg.GetBuffer(1));
    return 0;
  }

  CFemmeDoc* thisDoc;
  CFemmeView* theView;
  thisDoc = (CFemmeDoc*)pFemmeDoc;
  POSITION pos;
  pos = thisDoc->GetFirstViewPosition();
  theView = (CFemmeView*)thisDoc->GetNextView(pos);

  //	thisDoc->UnselectAll();

  // select nodes
  for (i = 0; i < thisDoc->nodelist.GetSize(); i++) {
    if (thisDoc->nodelist[i].InGroup == group)
      thisDoc->nodelist[i].IsSelected = TRUE;
  }

  // select segments
  for (i = 0; i < thisDoc->linelist.GetSize(); i++) {
    if (thisDoc->linelist[i].InGroup == group)
      thisDoc->linelist[i].IsSelected = TRUE;
  }

  // select arc segments
  for (i = 0; i < thisDoc->arclist.GetSize(); i++) {
    if (thisDoc->arclist[i].InGroup == group)
      thisDoc->arclist[i].IsSelected = TRUE;
  }

  // select blocks
  for (i = 0; i < thisDoc->blocklist.GetSize(); i++) {
    if (thisDoc->blocklist[i].InGroup == group)
      thisDoc->blocklist[i].IsSelected = TRUE;
  }

  theView->EditAction = 4; // set to group

  return 0;
}

int CFemmeDoc::lua_addmatprop(lua_State* L)
{
  // for compatibility with 4.0 and 4.1 Lua implementation
  if (((CFemmApp*)AfxGetApp())->CompatibilityMode != 0)
    return ((CFemmeDoc*)pFemmeDoc)->old_lua_addmatprop(L);

  CatchNullDocument();

  CMaterialProp m;
  int n = lua_gettop(L);

  if (n > 0)
    m.BlockName.Format("%s", lua_tostring(L, 1));
  if (n > 1) {
    m.mu_x = lua_todouble(L, 2);
    m.mu_y = m.mu_x;
  }
  if (n > 2)
    m.mu_y = lua_todouble(L, 3);
  if (n > 3)
    m.H_c = lua_todouble(L, 4);
  if (n > 4)
    m.Jsrc = lua_tonumber(L, 5);
  if (n > 5)
    m.Cduct = lua_todouble(L, 6);
  if (n > 6)
    m.Lam_d = lua_todouble(L, 7);
  if (n > 7)
    m.Theta_hn = lua_todouble(L, 8);
  if (n > 8) {
    m.LamFill = lua_todouble(L, 9);
    if (m.LamFill <= 0)
      m.LamFill = 1;
    if (m.LamFill > 1)
      m.LamFill = 1;
  }
  if (n > 9) {
    m.LamType = (int)lua_todouble(L, 10);
    if (m.LamType < 0)
      m.LamType = 0;
  }
  if (n > 10) {
    m.Theta_hx = lua_todouble(L, 11);
    m.Theta_hy = lua_todouble(L, 12);
  } else {
    m.Theta_hx = m.Theta_hn;
    m.Theta_hy = m.Theta_hn;
  }
  if (n > 12) {
    m.NStrands = (int)lua_todouble(L, 13);
    m.WireD = lua_todouble(L, 14);
  }

  ((CFemmeDoc*)pFemmeDoc)->blockproplist.Add(m);

  return 0;
}

int CFemmeDoc::lua_addbhpoint(lua_State* L)
{
  CatchNullDocument();
  CString BlockName;
  CComplex v;
  int j, k, n;

  CFemmeDoc* thisDoc;
  CFemmeView* theView;
  thisDoc = (CFemmeDoc*)pFemmeDoc;
  POSITION pos;
  pos = thisDoc->GetFirstViewPosition();
  theView = (CFemmeView*)thisDoc->GetNextView(pos);

  // find the index of the material to modify;
  if (thisDoc->blockproplist.GetSize() == 0)
    return TRUE;
  BlockName.Format("%s", lua_tostring(L, 1));
  for (k = 0; k < thisDoc->blockproplist.GetSize(); k++)
    if (BlockName == thisDoc->blockproplist[k].BlockName)
      break;

  // get out of here if there's no matching material
  if (k == thisDoc->blockproplist.GetSize())
    return TRUE;

  // now, add the bhpoint for the specified material;
  n = thisDoc->blockproplist[k].BHpoints;
  v = lua_tonumber(L, 2) + I * lua_tonumber(L, 3);
  if (n == 0) // Make sure that (0,0) gets included as a data point;
  {
    n = 1;
    thisDoc->blockproplist[k].BHpoints = 1;
    thisDoc->blockproplist[k].BHdata = (CComplex*)malloc(sizeof(CComplex));
    thisDoc->blockproplist[k].BHdata[0] = 0;
  }
  // make sure the point isn't a duplicate
  for (j = 0; j < n; j++) {
    if (thisDoc->blockproplist[k].BHdata[j] == v)
      return 0;
  }
  CComplex* newBHdata = (CComplex*)calloc(n + 1, sizeof(CComplex));
  for (j = 0; j < n; j++)
    newBHdata[j] = thisDoc->blockproplist[k].BHdata[j];
  thisDoc->blockproplist[k].BHpoints = n + 1;
  if (n != 0)
    free(thisDoc->blockproplist[k].BHdata);
  thisDoc->blockproplist[k].BHdata = newBHdata;
  newBHdata[n] = v;

  // make sure that the BH points are in the right order;
  int flag;
  for (j = 0; j < n; j++) {
    for (k = 0, flag = 0; k < n; k++) {
      if (newBHdata[k].re > newBHdata[k + 1].re) {
        flag = 1;
        v = newBHdata[k];
        newBHdata[k] = newBHdata[k + 1];
        newBHdata[k + 1] = v;
      }
    }
    if (flag == 0)
      j = n;
  }

  return 0;
}

int CFemmeDoc::lua_clearbhpoints(lua_State* L)
{
  CatchNullDocument();
  CString BlockName;
  int k;

  CFemmeDoc* thisDoc;
  CFemmeView* theView;
  thisDoc = (CFemmeDoc*)pFemmeDoc;
  POSITION pos;
  pos = thisDoc->GetFirstViewPosition();
  theView = (CFemmeView*)thisDoc->GetNextView(pos);

  // find the index of the material to modify;
  if (thisDoc->blockproplist.GetSize() == 0)
    return TRUE;
  BlockName.Format("%s", lua_tostring(L, 1));
  for (k = 0; k < thisDoc->blockproplist.GetSize(); k++)
    if (BlockName == thisDoc->blockproplist[k].BlockName)
      break;

  // get out of here if there's no matching material
  if (k == thisDoc->blockproplist.GetSize())
    return TRUE;

  // now, snuff the BH curve for the specified material
  if (thisDoc->blockproplist[k].BHpoints > 0) {
    thisDoc->blockproplist[k].BHpoints = 0;
    free(thisDoc->blockproplist[k].BHdata);
    thisDoc->blockproplist[k].BHdata = NULL;
  }

  return 0;
}

int CFemmeDoc::lua_modmatprop(lua_State* L)
{
  // for compatibility with 4.0 and 4.1 Lua implementation
  if (((CFemmApp*)AfxGetApp())->CompatibilityMode != 0)
    return ((CFemmeDoc*)pFemmeDoc)->old_lua_modmatprop(L);

  CatchNullDocument();
  CString BlockName;
  int k, modprop;

  CFemmeDoc* thisDoc;
  CFemmeView* theView;
  thisDoc = (CFemmeDoc*)pFemmeDoc;
  POSITION pos;
  pos = thisDoc->GetFirstViewPosition();
  theView = (CFemmeView*)thisDoc->GetNextView(pos);

  // find the index of the material to modify;
  if (thisDoc->blockproplist.GetSize() == 0)
    return TRUE;
  BlockName.Format("%s", lua_tostring(L, 1));
  for (k = 0; k < thisDoc->blockproplist.GetSize(); k++)
    if (BlockName == thisDoc->blockproplist[k].BlockName)
      break;

  // get out of here if there's no matching material
  if (k == thisDoc->blockproplist.GetSize())
    return TRUE;

  modprop = (int)lua_todouble(L, 2);

  // now, modify the specified attribute...
  switch (modprop) {
  case 0:
    thisDoc->blockproplist[k].BlockName.Format("%s", lua_tostring(L, 3));
    break;
  case 1:
    thisDoc->blockproplist[k].mu_x = lua_todouble(L, 3);
    break;
  case 2:
    thisDoc->blockproplist[k].mu_y = lua_todouble(L, 3);
    break;
  case 3:
    thisDoc->blockproplist[k].H_c = lua_todouble(L, 3);
    break;
  case 4:
    thisDoc->blockproplist[k].Jsrc = lua_tonumber(L, 3);
    break;
  case 5:
    thisDoc->blockproplist[k].Cduct = lua_todouble(L, 3);
    break;
  case 6:
    thisDoc->blockproplist[k].Lam_d = lua_todouble(L, 3);
    break;
  case 7:
    thisDoc->blockproplist[k].Theta_hn = lua_todouble(L, 3);
    break;
  case 8:
    thisDoc->blockproplist[k].LamFill = lua_todouble(L, 3);
    break;
  case 9:
    thisDoc->blockproplist[k].LamType = (int)lua_todouble(L, 3);
    break;
  case 10:
    thisDoc->blockproplist[k].Theta_hx = lua_todouble(L, 3);
    break;
  case 11:
    thisDoc->blockproplist[k].Theta_hy = lua_todouble(L, 3);
    break;
  case 12:
    thisDoc->blockproplist[k].NStrands = (int)lua_todouble(L, 3);
    break;
  case 13:
    thisDoc->blockproplist[k].WireD = lua_todouble(L, 3);
  default:
    break;
  }

  return 0;
}

int CFemmeDoc::lua_addboundprop(lua_State* L)
{
  CatchNullDocument();

  CBoundaryProp m;
  int n = lua_gettop(L);

  if (n > 0)
    m.BdryName.Format("%s", lua_tostring(L, 1));
  if (n > 1)
    m.A0 = lua_todouble(L, 2);
  if (n > 2)
    m.A1 = lua_todouble(L, 3);
  if (n > 3)
    m.A2 = lua_todouble(L, 4);
  if (n > 4)
    m.phi = lua_todouble(L, 5);
  if (n > 5)
    m.Mu = lua_todouble(L, 6);
  if (n > 6)
    m.Sig = lua_todouble(L, 7);
  if (n > 7)
    m.c0 = lua_tonumber(L, 8);
  if (n > 8)
    m.c1 = lua_tonumber(L, 9);
  if (n > 9)
    m.BdryFormat = (int)lua_todouble(L, 10);
  if (n > 10)
    m.InnerAngle = lua_todouble(L, 11);
  if (n > 11)
    m.InnerAngle = lua_todouble(L, 12);
  if (n > 12)
    m.InnerAngle = lua_todouble(L, 13);
  if (n > 13)
    m.InnerAngle = lua_todouble(L, 14);

  ((CFemmeDoc*)pFemmeDoc)->lineproplist.Add(m);

  return 0;
}

int CFemmeDoc::lua_modboundprop(lua_State* L)
{
  CatchNullDocument();
  CString BdryName;
  int k, modprop;

  CFemmeDoc* thisDoc;
  CFemmeView* theView;
  thisDoc = (CFemmeDoc*)pFemmeDoc;
  POSITION pos;
  pos = thisDoc->GetFirstViewPosition();
  theView = (CFemmeView*)thisDoc->GetNextView(pos);

  // find the index of the boundary property to modify;
  if (thisDoc->lineproplist.GetSize() == 0)
    return TRUE;
  BdryName.Format("%s", lua_tostring(L, 1));
  for (k = 0; k < thisDoc->lineproplist.GetSize(); k++)
    if (BdryName == thisDoc->lineproplist[k].BdryName)
      break;

  // get out of here if there's no matching material
  if (k == thisDoc->lineproplist.GetSize())
    return TRUE;

  modprop = (int)lua_todouble(L, 2);

  // now, modify the specified attribute...
  switch (modprop) {
  case 0:
    thisDoc->lineproplist[k].BdryName.Format("%s", lua_tostring(L, 3));
    break;
  case 1:
    thisDoc->lineproplist[k].A0 = lua_todouble(L, 3);
    break;
  case 2:
    thisDoc->lineproplist[k].A1 = lua_todouble(L, 3);
    break;
  case 3:
    thisDoc->lineproplist[k].A2 = lua_todouble(L, 3);
    break;
  case 4:
    thisDoc->lineproplist[k].phi = lua_todouble(L, 3);
    break;
  case 5:
    thisDoc->lineproplist[k].Mu = lua_todouble(L, 3);
    break;
  case 6:
    thisDoc->lineproplist[k].Sig = lua_todouble(L, 3);
    break;
  case 7:
    thisDoc->lineproplist[k].c0 = lua_tonumber(L, 3);
    break;
  case 8:
    thisDoc->lineproplist[k].c1 = lua_tonumber(L, 3);
    break;
  case 9:
    thisDoc->lineproplist[k].BdryFormat = (int)lua_todouble(L, 3);
    break;
  case 10:
    thisDoc->lineproplist[k].InnerAngle = lua_todouble(L, 3);
    break;
  case 11:
    thisDoc->lineproplist[k].OuterAngle = lua_todouble(L, 3);
    break;

  default:
    break;
  }

  return 0;
}

int CFemmeDoc::lua_addpointprop(lua_State* L)
{
  // for compatibility with 4.0 and 4.1 Lua implementation
  if (((CFemmApp*)AfxGetApp())->CompatibilityMode != 0)
    return ((CFemmeDoc*)pFemmeDoc)->old_lua_addpointprop(L);

  CatchNullDocument();

  CPointProp m;
  int n = lua_gettop(L);

  if (n > 0)
    m.PointName.Format("%s", lua_tostring(L, 1));
  if (n > 1)
    m.Ap = lua_tonumber(L, 2);
  if (n > 2)
    m.Jp = lua_tonumber(L, 3);

  ((CFemmeDoc*)pFemmeDoc)->nodeproplist.Add(m);

  return 0;
}

int CFemmeDoc::lua_modpointprop(lua_State* L)
{
  // for compatibility with 4.0 and 4.1 Lua implementation
  if (((CFemmApp*)AfxGetApp())->CompatibilityMode != 0)
    return ((CFemmeDoc*)pFemmeDoc)->old_lua_modpointprop(L);

  CatchNullDocument();
  CString PointName;
  int k, modprop;

  CFemmeDoc* thisDoc;
  CFemmeView* theView;

  thisDoc = (CFemmeDoc*)pFemmeDoc;
  POSITION pos;
  pos = thisDoc->GetFirstViewPosition();
  theView = (CFemmeView*)thisDoc->GetNextView(pos);

  // find the index of the material to modify;
  if (thisDoc->nodeproplist.GetSize() == 0)
    return TRUE;
  PointName.Format("%s", lua_tostring(L, 1));
  for (k = 0; k < thisDoc->nodeproplist.GetSize(); k++)
    if (PointName == thisDoc->nodeproplist[k].PointName)
      break;

  // get out of here if there's no matching material
  if (k == thisDoc->nodeproplist.GetSize())
    return TRUE;

  modprop = (int)lua_todouble(L, 2);

  // now, modify the specified attribute...
  switch (modprop) {
  case 0:
    thisDoc->nodeproplist[k].PointName.Format("%s", lua_tostring(L, 3));
    break;
  case 1:
    thisDoc->nodeproplist[k].Ap = lua_tonumber(L, 3);
    break;
  case 2:
    thisDoc->nodeproplist[k].Jp = lua_tonumber(L, 3);
    break;
  default:
    break;
  }

  return 0;
}

int CFemmeDoc::lua_addcircuitprop(lua_State* L)
{
  // for compatibility with 4.0 and 4.1 Lua implementation
  if (((CFemmApp*)AfxGetApp())->CompatibilityMode != 0)
    return ((CFemmeDoc*)pFemmeDoc)->old_lua_addcircuitprop(L);

  CatchNullDocument();

  CCircuit m;
  int n = lua_gettop(L);

  if (n > 0)
    m.CircName = lua_tostring(L, 1);
  if (n > 1)
    m.Amps = lua_tonumber(L, 2);
  if (n > 2)
    m.CircType = (int)lua_todouble(L, 3);

  // there shouldn't be duplicate circuit names.
  for (int k = 0; k < ((CFemmeDoc*)pFemmeDoc)->circproplist.GetSize(); k++) {
    if (m.CircName == ((CFemmeDoc*)pFemmeDoc)->circproplist[k].CircName) {
      CString msg;
      msg.Format("Duplicate circuit name (%s) not allowed", m.CircName);
      lua_error(L, msg.GetBuffer(1));
      return NULL;
    }
  }

  ((CFemmeDoc*)pFemmeDoc)->circproplist.Add(m);

  return 0;
}

int CFemmeDoc::lua_modcircprop(lua_State* L)
{
  // for compatibility with 4.0 and 4.1 Lua implementation
  if (((CFemmApp*)AfxGetApp())->CompatibilityMode != 0)
    return ((CFemmeDoc*)pFemmeDoc)->old_lua_modcircprop(L);

  CatchNullDocument();
  CString CircName;
  int k, modprop;

  CFemmeDoc* thisDoc;
  thisDoc = (CFemmeDoc*)pFemmeDoc;

  // find the index of the material to modify;
  if (thisDoc->circproplist.GetSize() == 0)
    return TRUE;
  CircName.Format("%s", lua_tostring(L, 1));
  for (k = 0; k < thisDoc->circproplist.GetSize(); k++)
    if (CircName == thisDoc->circproplist[k].CircName)
      break;

  // get out of here if there's no matching circuit
  if (k == thisDoc->circproplist.GetSize())
    return TRUE;

  modprop = (int)lua_todouble(L, 2);

  // now, modify the specified attribute...
  switch (modprop) {
  case 0:
    thisDoc->circproplist[k].CircName.Format("%s", lua_tostring(L, 3));
    break;
  case 1:
    thisDoc->circproplist[k].Amps = lua_tonumber(L, 3);
    break;
  case 2:
    thisDoc->circproplist[k].CircType = (int)lua_todouble(L, 3);
    break;
  default:
    break;
  }

  return 0;
}

int CFemmeDoc::lua_delcircuitprop(lua_State* L)
{
  CatchNullDocument();
  CString name;
  name.Format("%s", lua_tostring(L, 1));

  CFemmeDoc* thisDoc;
  CFemmeView* theView;

  thisDoc = (CFemmeDoc*)pFemmeDoc;
  POSITION pos;
  pos = thisDoc->GetFirstViewPosition();
  theView = (CFemmeView*)thisDoc->GetNextView(pos);

  for (int i = 0; i < thisDoc->circproplist.GetSize(); i++) {
    if (thisDoc->circproplist[i].CircName == name)
      thisDoc->circproplist.RemoveAt(i);
  }

  return 0;
}

int CFemmeDoc::lua_delmatprop(lua_State* L)
{
  CatchNullDocument();
  CString name;
  name.Format("%s", lua_tostring(L, 1));

  CFemmeDoc* thisDoc;
  CFemmeView* theView;

  thisDoc = (CFemmeDoc*)pFemmeDoc;
  POSITION pos;
  pos = thisDoc->GetFirstViewPosition();
  theView = (CFemmeView*)thisDoc->GetNextView(pos);

  for (int i = 0; i < thisDoc->blockproplist.GetSize(); i++) {
    if (thisDoc->blockproplist[i].BlockName == name)
      thisDoc->blockproplist.RemoveAt(i);
  }

  return 0;
}

int CFemmeDoc::lua_delboundprop(lua_State* L)
{
  CatchNullDocument();
  CString name;
  name.Format("%s", lua_tostring(L, 1));

  CFemmeDoc* thisDoc;
  CFemmeView* theView;

  thisDoc = (CFemmeDoc*)pFemmeDoc;
  POSITION pos;
  pos = thisDoc->GetFirstViewPosition();
  theView = (CFemmeView*)thisDoc->GetNextView(pos);

  for (int i = 0; i < thisDoc->lineproplist.GetSize(); i++) {
    if (thisDoc->lineproplist[i].BdryName == name)
      thisDoc->lineproplist.RemoveAt(i);
  }

  return 0;
}

int CFemmeDoc::lua_delpointprop(lua_State* L)
{
  CatchNullDocument();
  CString name;
  name.Format("%s", lua_tostring(L, 1));
  CFemmeDoc* thisDoc;
  CFemmeView* theView;

  thisDoc = (CFemmeDoc*)pFemmeDoc;
  POSITION pos;
  pos = thisDoc->GetFirstViewPosition();
  theView = (CFemmeView*)thisDoc->GetNextView(pos);

  for (int i = 0; i < thisDoc->nodeproplist.GetSize(); i++) {
    if (thisDoc->nodeproplist[i].PointName == name)
      thisDoc->nodeproplist.RemoveAt(i);
  }

  return 0;
}

int CFemmeDoc::lua_updatewindow(lua_State* L)
{
  CatchNullDocument();
  CFemmeDoc* thisDoc;
  CFemmeView* theView;
  thisDoc = (CFemmeDoc*)pFemmeDoc;
  POSITION pos;
  pos = thisDoc->GetFirstViewPosition();
  theView = (CFemmeView*)thisDoc->GetNextView(pos);

  CDC tempDC;
  CDC* pDC = theView->GetDC();

  // erase background
  CBrush backBrush(theView->BackColor);
  CBrush* pOldBrush = pDC->SelectObject(&backBrush);
  CRect rect;
  pDC->GetClipBox(&rect);
  pDC->PatBlt(rect.left, rect.top, rect.Width(),
      rect.Height(), PATCOPY);
  pDC->SelectObject(pOldBrush);

  // force redraw
  theView->OnDraw(pDC);

  return 0;
}

// mi_setredraw(flag): flag=0 suspends canvas redraw for subsequent edit
// operations (e.g. a batch of mi_copytranslate/mi_copyrotate calls on a
// densely-drawn model); flag=1 (default state) resumes it and forces a
// single refresh to show everything that changed while it was off.
int CFemmeDoc::lua_setredraw(lua_State* L)
{
  CatchNullDocument();
  CFemmeDoc* thisDoc;
  CFemmeView* theView;
  thisDoc = (CFemmeDoc*)pFemmeDoc;
  POSITION pos;
  pos = thisDoc->GetFirstViewPosition();
  theView = (CFemmeView*)thisDoc->GetNextView(pos);

  int n = lua_gettop(L);
  BOOL enable = TRUE;
  if (n > 0)
    enable = (lua_todouble(L, 1) != 0);

  thisDoc->NoDraw = !enable;
  if (enable)
    theView->InvalidateRect(NULL);

  return 0;
}

// mi_setgpuaccel(flag): flag=1 asks fkn.exe to try its optional CUDA-
// accelerated linear solve for this problem (see fkn/spars_cuda.cu); it
// transparently falls back to the normal CPU solve if fkn.exe wasn't
// built with CUDA support, or if the GPU solve fails for any reason.
// flag=0 (default) is CPU-only. Persisted in the .fem file as
// [GPUAccel], same mechanism as the existing AC solver choice.
int CFemmeDoc::lua_setgpuaccel(lua_State* L)
{
  CatchNullDocument();
  CFemmeDoc* thisDoc;
  thisDoc = (CFemmeDoc*)pFemmeDoc;

  int n = lua_gettop(L);
  BOOL enable = TRUE;
  if (n > 0)
    enable = (lua_todouble(L, 1) != 0);

  thisDoc->GPUAccel = enable ? 1 : 0;

  return 0;
}

// mi_savepng("filename") -- the preprocessor twin of mo_savepng; see
// that function in femmviewLua.cpp for the routing rationale.
int CFemmeDoc::lua_savepng(lua_State* L)
{
  CatchNullDocument();
  CFemmeDoc* thisDoc = (CFemmeDoc*)pFemmeDoc;
  POSITION pos = thisDoc->GetFirstViewPosition();
  CFemmeView* theView = (CFemmeView*)thisDoc->GetNextView(pos);

  CString filename;
  filename.Format("%s", lua_tostring(L, 1));

  RECT r;
  theView->GetClientRect(&r);
  // Modified by Claude (Anthropic), noreply@anthropic.com, 2026-09-11:
  // savepng took its size straight from the client rect, which is the
  // exact defect issue #4 fixed for savebitmap and then left standing
  // here. A view that has never been shown -- every COM-automation
  // session -- reports a rect with a zero dimension, and the two paths
  // failed differently and both badly: the classic path asked
  // CreateCompatibleBitmap for a 0-by-0 bitmap, which is documented to
  // hand back a 1x1 MONOCHROME one, so a script got a valid, useless PNG
  // and a success return; the Qt path shelled out
  // `femmqt.exe --render-png ... 0 0`, which refuses a bad size and
  // exits 1. femmCaptureSize() substitutes the same documented default
  // savebitmap uses, so a headless script gets a real picture (#19).
  SIZE cap = femmCaptureSize(r);
  int width = (lua_gettop(L) >= 3) ? (int)lua_todouble(L, 2) : (int)cap.cx;
  int height = (lua_gettop(L) >= 3) ? (int)lua_todouble(L, 3) : (int)cap.cy;

  if (GetScriptGui() == ScriptGui::Qt) {
    CString pn = thisDoc->GetPathName();
    if (pn.GetLength() == 0) {
      CString msg = "mi_savepng: with setgui(\"qt\"), the document must "
                    "already be saved to disk for femmqt.exe to open.";
      lua_error(L, msg.GetBuffer(1));
      return 0;
    }
    CString err;
    // NULL: the pre-processor is geometry, with no plot state to carry
    // (#86).
    if (!RenderPngViaQtGui(theView->BinDir, pn, filename, width, height, NULL,
            &err)) {
      CString msg;
      msg.Format("mi_savepng: %s", (const char*)err);
      lua_error(L, msg.GetBuffer(1));
    }
    return 0;
  }

  CDC tempDC;
  CBitmap bitmap;
  CBitmap* oldbitmap;
  CDC* pDC = theView->GetDC();

  tempDC.CreateCompatibleDC(pDC);
  bitmap.CreateCompatibleBitmap(pDC, cap.cx, cap.cy);
  oldbitmap = tempDC.SelectObject(&bitmap);
  tempDC.Rectangle(0, 0, cap.cx, cap.cy);
  theView->OnDraw(&tempDC);

  BOOL ok = SaveHBitmapAsPng(HBITMAP(bitmap), filename.GetBuffer(1));

  tempDC.SelectObject(oldbitmap);
  theView->ReleaseDC(pDC);
  tempDC.DeleteDC();
  bitmap.DeleteObject();

  if (!ok) {
    CString msg;
    msg.Format("mi_savepng: couldn't write \"%s\"", (const char*)filename);
    lua_error(L, msg.GetBuffer(1));
  }
  return 0;
}

int CFemmeDoc::lua_savebitmap(lua_State* L)
{
  CatchNullDocument();
  CFemmeDoc* thisDoc;
  CFemmeView* theView;
  thisDoc = (CFemmeDoc*)pFemmeDoc;
  POSITION pos;
  pos = thisDoc->GetFirstViewPosition();
  theView = (CFemmeView*)thisDoc->GetNextView(pos);
  CString filename;

  filename.Format("%s", lua_tostring(L, 1));

  RECT r;
  CDC tempDC;
  CBitmap bitmap;
  CDC* pDC = theView->GetDC();

  theView->GetClientRect(&r);

  // Issue #4: a view that has never been shown -- every COM-automation
  // session -- reports a rect with a zero dimension, and
  // CreateCompatibleBitmap answers a zero dimension with a 1x1 MONOCHROME
  // bitmap. That is how savebitmap used to write a valid, useless 58-byte
  // file and report success. Capture at a real size instead.
  SIZE cap = femmCaptureSize(r);

  tempDC.CreateCompatibleDC(pDC);
  bitmap.CreateCompatibleBitmap(pDC, cap.cx, cap.cy);
  CBitmap* oldbitmap = tempDC.SelectObject(&bitmap);

  tempDC.Rectangle(0, 0, cap.cx, cap.cy);
  theView->OnDraw(&tempDC);

  CString bmpErr;
  BOOL bmpOk = femmWriteBitmapFile(HBITMAP(bitmap), tempDC.m_hDC,
                                   (LPCTSTR)filename, bmpErr);

  // Only CFemmviewDoc used to restore and release; the other seven leaked a
  // DC per call and let CBitmap delete a bitmap still selected into one.
  tempDC.SelectObject(oldbitmap);
  theView->ReleaseDC(pDC);
  tempDC.DeleteDC();

  if (!bmpOk)
    MsgBox("%s", (LPCTSTR)bmpErr);

  return 0;
}

PBITMAPINFO CFemmeDoc::CreateBitmapInfoStruct(HWND hwnd, HBITMAP hBmp)
{
  BITMAP bmp;
  PBITMAPINFO pbmi;
  WORD cClrBits;

  // Retrieve the bitmap's color format, width, and height.
  if (!GetObject(hBmp, sizeof(BITMAP), (LPSTR)&bmp)) { // errhandler("GetObject", hwnd);
    MsgBox("Critical error on getting bmp info, possible page fault ahoy17");
  }
  // Convert the color format to a count of bits.
  cClrBits = (WORD)(bmp.bmPlanes * bmp.bmBitsPixel);
  if (cClrBits == 1)
    cClrBits = 1;
  else if (cClrBits <= 4)
    cClrBits = 4;
  else if (cClrBits <= 8)
    cClrBits = 8;
  else if (cClrBits <= 16)
    cClrBits = 16;
  else if (cClrBits <= 24)
    cClrBits = 24;
  else
    cClrBits = 32;

  // Allocate memory for the BITMAPINFO structure. (This structure
  // contains a BITMAPINFOHEADER structure and an array of RGBQUAD
  // data structures.)

  if (cClrBits != 24)
    pbmi = (PBITMAPINFO)LocalAlloc(LPTR,
        sizeof(BITMAPINFOHEADER) + sizeof(RGBQUAD) * ((int)(1 << cClrBits)));

  // There is no RGBQUAD array for the 24-bit-per-pixel format.

  else
    pbmi = (PBITMAPINFO)LocalAlloc(LPTR,
        sizeof(BITMAPINFOHEADER));

  // Initialize the fields in the BITMAPINFO structure.

  pbmi->bmiHeader.biSize = sizeof(BITMAPINFOHEADER);
  pbmi->bmiHeader.biWidth = bmp.bmWidth;
  pbmi->bmiHeader.biHeight = bmp.bmHeight;
  pbmi->bmiHeader.biPlanes = bmp.bmPlanes;
  pbmi->bmiHeader.biBitCount = bmp.bmBitsPixel;
  if (cClrBits < 24)
    pbmi->bmiHeader.biClrUsed = (1 << cClrBits);

  // If the bitmap is not compressed, set the BI_RGB flag.
  pbmi->bmiHeader.biCompression = BI_RGB;

  // Compute the number of bytes in the array of color
  // indices and store the result in biSizeImage.
  // For Windows NT/2000, the width must be DWORD aligned unless
  // the bitmap is RLE compressed. This example shows this.
  // For Windows 95/98, the width must be WORD aligned unless the
  // bitmap is RLE compressed.
  pbmi->bmiHeader.biSizeImage = ((pbmi->bmiHeader.biWidth * cClrBits + 31) & ~31) / 8
      * pbmi->bmiHeader.biHeight;
  // Set biClrImportant to 0, indicating that all of the
  // device colors are important.
  pbmi->bmiHeader.biClrImportant = 0;
  return pbmi;
}

void CFemmeDoc::CreateBMPFile(HWND hwnd, LPTSTR pszFile, PBITMAPINFO pbi,
    HBITMAP hBMP, HDC hDC)
{
  HANDLE hf; // file handle
  BITMAPFILEHEADER hdr; // bitmap file-header
  PBITMAPINFOHEADER pbih; // bitmap info-header
  LPBYTE lpBits; // memory pointer
  DWORD dwTotal; // total count of bytes
  DWORD cb; // incremental count of bytes
  BYTE* hp; // byte pointer
  DWORD dwTmp;

  pbih = (PBITMAPINFOHEADER)pbi;
  lpBits = (LPBYTE)GlobalAlloc(GMEM_FIXED, pbih->biSizeImage);

  if (!lpBits)
    MsgBox("Critical error on getting bmp info, possible page fault ahoy18");
  //              errhandler("GlobalAlloc", hwnd);

  // Retrieve the color table (RGBQUAD array) and the bits
  // (array of palette indices) from the DIB.
  if (!GetDIBits(hDC, hBMP, 0, (WORD)pbih->biHeight, lpBits, pbi,
          DIB_RGB_COLORS)) {
    //    errhandler("GetDIBits", hwnd);
    MsgBox("Critical error on getting bmp info, possible page fault ahoy19");
  }

  // Create the .BMP file.
  hf = CreateFile(pszFile,
      GENERIC_READ | GENERIC_WRITE,
      (DWORD)0,
      NULL,
      CREATE_ALWAYS,
      FILE_ATTRIBUTE_NORMAL,
      (HANDLE)NULL);
  if (hf == INVALID_HANDLE_VALUE) { //    errhandler("CreateFile", hwnd);
    MsgBox("Critical error on getting bmp info, possible page fault ahoy20");
  }
  hdr.bfType = 0x4d42; // 0x42 = "B" 0x4d = "M"
  // Compute the size of the entire file.
  hdr.bfSize = (DWORD)(sizeof(BITMAPFILEHEADER) + pbih->biSize + pbih->biClrUsed * sizeof(RGBQUAD) + pbih->biSizeImage);
  hdr.bfReserved1 = 0;
  hdr.bfReserved2 = 0;

  // Compute the offset to the array of color indices.
  hdr.bfOffBits = (DWORD)sizeof(BITMAPFILEHEADER) + pbih->biSize + pbih->biClrUsed * sizeof(RGBQUAD);

  // Copy the BITMAPFILEHEADER into the .BMP file.
  if (!WriteFile(hf, (LPVOID)&hdr, sizeof(BITMAPFILEHEADER),
          (LPDWORD)&dwTmp, NULL)) {
    MsgBox("Critical error on getting bmp info, possible page fault ahoy21");

    //      errhandler("WriteFile", hwnd);
  }

  // Copy the BITMAPINFOHEADER and RGBQUAD array into the file.
  if (!WriteFile(hf, (LPVOID)pbih, sizeof(BITMAPINFOHEADER) + pbih->biClrUsed * sizeof(RGBQUAD),
          (LPDWORD)&dwTmp, (NULL)))
    //        errhandler("WriteFile", hwnd);
    MsgBox("Critical error on getting bmp info, possible page fault ahoy22");

  // Copy the array of color indices into the .BMP file.
  dwTotal = cb = pbih->biSizeImage;
  hp = lpBits;
  if (!WriteFile(hf, (LPSTR)hp, (int)cb, (LPDWORD)&dwTmp, NULL))
    //           errhandler("WriteFile", hwnd);
    MsgBox("Critical error on getting bmp info, possible page fault ahoy23");

  // Close the .BMP file.
  if (!CloseHandle(hf))
    //           errhandler("CloseHandle", hwnd);
    MsgBox("Critical error on getting bmp info, possible page fault ahoy24");

  // Free memory.
  GlobalFree((HGLOBAL)lpBits);
}

int CFemmeDoc::lua_saveWMF(lua_State* L)
{
  CatchNullDocument();
  CFemmeDoc* thisDoc;
  CFemmeView* theView;
  thisDoc = (CFemmeDoc*)pFemmeDoc;
  POSITION pos;
  pos = thisDoc->GetFirstViewPosition();
  theView = (CFemmeView*)thisDoc->GetNextView(pos);

  CString filename;

  filename.Format("%s", lua_tostring(L, 1));

  RECT r;
  CDC tempDC;
  CDC* pDC = theView->GetDC();

  CMetaFileDC Meta;
  CRgn R;

  Meta.CreateEnhanced(NULL, NULL, NULL, NULL);
  theView->GetClientRect(&r);
  R.CreateRectRgnIndirect(&r);
  Meta.SelectClipRgn(&R);
  theView->OnDraw(&Meta);
  HENHMETAFILE hMeta = Meta.CloseEnhanced();

  DeleteEnhMetaFile(CopyEnhMetaFile(hMeta, filename));
  DeleteEnhMetaFile(hMeta);

  return 0;
}

int CFemmeDoc::lua_hidegrid(lua_State* L)
{
  CatchNullDocument();
  CFemmeDoc* thisDoc;
  CFemmeView* theView;
  thisDoc = (CFemmeDoc*)pFemmeDoc;
  POSITION pos;
  pos = thisDoc->GetFirstViewPosition();
  theView = (CFemmeView*)thisDoc->GetNextView(pos);

  CMainFrame* MFrm;
  MFrm = (CMainFrame*)theView->GetTopLevelFrame();
  CMenu* MMnu = MFrm->GetMenu();
  CToolBar* pToolBar;
  pToolBar = &MFrm->m_FE_toolBar1;
  CToolBarCtrl* tc = &pToolBar->GetToolBarCtrl();

  theView->GridFlag = FALSE;
  MMnu->CheckMenuItem(ID_SHOW_GRID, MF_UNCHECKED);
  tc->PressButton(ID_SHOW_GRID, FALSE);
  theView->InvalidateRect(NULL);

  return 0;
}

int CFemmeDoc::lua_showgrid(lua_State* L)
{
  CatchNullDocument();
  CFemmeDoc* thisDoc;
  CFemmeView* theView;
  thisDoc = (CFemmeDoc*)pFemmeDoc;
  POSITION pos;
  pos = thisDoc->GetFirstViewPosition();
  theView = (CFemmeView*)thisDoc->GetNextView(pos);

  CMainFrame* MFrm;
  MFrm = (CMainFrame*)theView->GetTopLevelFrame();
  CMenu* MMnu = MFrm->GetMenu();
  CToolBar* pToolBar;
  pToolBar = &MFrm->m_FE_toolBar1;
  CToolBarCtrl* tc = &pToolBar->GetToolBarCtrl();

  theView->GridFlag = TRUE;
  MMnu->CheckMenuItem(ID_SHOW_GRID, MF_CHECKED);
  tc->PressButton(ID_SHOW_GRID, TRUE);
  theView->InvalidateRect(NULL);

  return 0;
}

int CFemmeDoc::lua_gridsnap(lua_State* L)
{
  CatchNullDocument();
  CFemmeDoc* thisDoc;
  CFemmeView* theView;
  thisDoc = (CFemmeDoc*)pFemmeDoc;
  POSITION pos;
  pos = thisDoc->GetFirstViewPosition();
  theView = (CFemmeView*)thisDoc->GetNextView(pos);

  CString temp;
  temp.Format("%s", lua_tostring(L, 1));
  temp.MakeLower();

  CMainFrame* MFrm;
  MFrm = (CMainFrame*)theView->GetTopLevelFrame();
  CMenu* MMnu = MFrm->GetMenu();
  CToolBar* pToolBar;
  pToolBar = &MFrm->m_FE_toolBar1;
  CToolBarCtrl* tc = &pToolBar->GetToolBarCtrl();

  if (temp == "off") {
    theView->SnapFlag = FALSE;
    MMnu->CheckMenuItem(ID_SNAP_GRID, MF_UNCHECKED);
    tc->PressButton(ID_SNAP_GRID, FALSE);
  } else {
    theView->SnapFlag = TRUE;
    MMnu->CheckMenuItem(ID_SNAP_GRID, MF_CHECKED);
    tc->PressButton(ID_SNAP_GRID, TRUE);
  }

  if (temp != "on" && temp != "off") {
    CString msg = "Unknown option for grid snap";
    lua_error(L, msg.GetBuffer(1));
    return 0;
  }

  return 0;
}

int CFemmeDoc::lua_setgrid(lua_State* L)
{
  CatchNullDocument();
  CFemmeDoc* thisDoc;
  CFemmeView* theView;
  thisDoc = (CFemmeDoc*)pFemmeDoc;
  POSITION pos;
  pos = thisDoc->GetFirstViewPosition();
  theView = (CFemmeView*)thisDoc->GetNextView(pos);

  CString temp;
  int coords = 0;
  double gridsize;

  gridsize = lua_todouble(L, 1);
  temp.Format("%s", lua_tostring(L, 2));
  temp.MakeLower();

  if (temp == "cart")
    coords = 0;
  if (temp == "polar")
    coords = 1;

  if (temp != "cart" && temp != "polar") {
    CString msg = "Unknown option for set grid";
    lua_error(L, msg.GetBuffer(1));
    return 0;
  }

  theView->GridSize = gridsize;
  thisDoc->Coords = coords;
  theView->InvalidateRect(NULL);

  return 0;
}

int CFemmeDoc::lua_shownames(lua_State* L)
{
  CatchNullDocument();
  CFemmeDoc* thisDoc;
  CFemmeView* theView;
  thisDoc = (CFemmeDoc*)pFemmeDoc;
  POSITION pos;
  pos = thisDoc->GetFirstViewPosition();
  theView = (CFemmeView*)thisDoc->GetNextView(pos);

  int flg = (int)lua_todouble(L, 1);
  if (flg != 0)
    flg = 1;
  theView->ShowNames = flg;
  theView->InvalidateRect(NULL);

  return 0;
}

int CFemmeDoc::luaResize(lua_State* L)
{
  CatchNullDocument();
  CFemmeDoc* thisDoc;
  CFemmeView* theView;
  thisDoc = (CFemmeDoc*)pFemmeDoc;
  POSITION pos;
  pos = thisDoc->GetFirstViewPosition();
  theView = (CFemmeView*)thisDoc->GetNextView(pos);
  CChildFrame* pChildFrm = (CChildFrame*)theView->GetParentFrame();
  int n = lua_gettop(L);
  if (n != 2)
    return 0;

  int nWidth = (int)lua_todouble(L, 1);
  int nHeight = (int)lua_todouble(L, 2);
  pChildFrm->ResizeClient(nWidth, nHeight, TRUE);

  return 0;
}

int CFemmeDoc::luaMinimize(lua_State* L)
{
  CatchNullDocument();
  CFemmeDoc* thisDoc;
  CFemmeView* theView;
  thisDoc = (CFemmeDoc*)pFemmeDoc;
  POSITION pos;
  pos = thisDoc->GetFirstViewPosition();
  theView = (CFemmeView*)thisDoc->GetNextView(pos);
  CChildFrame* pChildFrm = (CChildFrame*)theView->GetParentFrame();

  pChildFrm->ShowWindow(SW_MINIMIZE);

  return 0;
}

int CFemmeDoc::luaMaximize(lua_State* L)
{
  CatchNullDocument();
  CFemmeDoc* thisDoc;
  CFemmeView* theView;
  thisDoc = (CFemmeDoc*)pFemmeDoc;
  POSITION pos;
  pos = thisDoc->GetFirstViewPosition();
  theView = (CFemmeView*)thisDoc->GetNextView(pos);
  CChildFrame* pChildFrm = (CChildFrame*)theView->GetParentFrame();

  pChildFrm->ShowWindow(SW_MAXIMIZE);

  return 0;
}

int CFemmeDoc::luaRestore(lua_State* L)
{
  CatchNullDocument();
  CFemmeDoc* thisDoc;
  CFemmeView* theView;
  thisDoc = (CFemmeDoc*)pFemmeDoc;
  POSITION pos;
  pos = thisDoc->GetFirstViewPosition();
  theView = (CFemmeView*)thisDoc->GetNextView(pos);
  CChildFrame* pChildFrm = (CChildFrame*)theView->GetParentFrame();

  pChildFrm->ShowWindow(SW_RESTORE);

  return 0;
}

int CFemmeDoc::lua_defineouterspace(lua_State* L)
{
  CatchNullDocument();
  CFemmeDoc* thisDoc;
  thisDoc = (CFemmeDoc*)pFemmeDoc;
  int n = lua_gettop(L);
  if (n != 3)
    return 0;

  thisDoc->extZo = fabs(lua_todouble(L, 1));
  thisDoc->extRo = fabs(lua_todouble(L, 2));
  thisDoc->extRi = fabs(lua_todouble(L, 3));

  if ((thisDoc->extRo == 0) || (thisDoc->extRi == 0)) {
    thisDoc->extZo = 0;
    thisDoc->extRo = 0;
    thisDoc->extRi = 0;
  }

  return 0;
}

int CFemmeDoc::lua_attachouterspace(lua_State* L)
{
  CatchNullDocument();
  CFemmeDoc* thisDoc;
  thisDoc = (CFemmeDoc*)pFemmeDoc;

  for (int i = 0; i < thisDoc->blocklist.GetSize(); i++)
    if (thisDoc->blocklist[i].IsSelected == TRUE)
      thisDoc->blocklist[i].IsExternal = TRUE;

  return 0;
}

int CFemmeDoc::lua_detachouterspace(lua_State* L)
{
  CatchNullDocument();
  CFemmeDoc* thisDoc;
  thisDoc = (CFemmeDoc*)pFemmeDoc;

  for (int i = 0; i < thisDoc->blocklist.GetSize(); i++)
    if (thisDoc->blocklist[i].IsSelected == TRUE)
      thisDoc->blocklist[i].IsExternal = FALSE;

  return 0;
}

int CFemmeDoc::lua_createradius(lua_State* L)
{
  CatchNullDocument();
  CFemmeDoc* thisDoc;
  CFemmeView* theView;
  thisDoc = (CFemmeDoc*)pFemmeDoc;
  POSITION pos;
  pos = thisDoc->GetFirstViewPosition();
  theView = (CFemmeView*)thisDoc->GetNextView(pos);

  int n = lua_gettop(L);
  if (n != 3)
    return 0;

  double x, y, r;
  int k;

  x = lua_todouble(L, 1);
  y = lua_todouble(L, 2);
  r = fabs(lua_todouble(L, 3));

  if ((k = thisDoc->ClosestNode(x, y)) < 0)
    return 0; // catch case where no nodes have been drawn yet;

  if (thisDoc->CanCreateRadius(k) == FALSE) {
    CString msg;
    msg.Format("The specified point is not suitable for conversion into a radius");
    lua_error(L, msg.GetBuffer(1));
    return 0;
  }

  if (thisDoc->CreateRadius(k, r)) {
    theView->InvalidateRect(NULL);
    theView->MeshUpToDate = FALSE;
  } else {
    CString msg;
    msg.Format("Could not make a radius of the prescribed dimension");
    lua_error(L, msg.GetBuffer(1));
    return 0;
  }

  return 0;
}

//////////////////////////////////////////////////////////////////////////////
//
// compatibility with previous versions
//
//////////////////////////////////////////////////////////////////////////////

int CFemmeDoc::old_lua_addmatprop(lua_State* L)
{
  CatchNullDocument();

  CMaterialProp m;
  int n = lua_gettop(L);

  if (n > 0)
    m.BlockName.Format("%s", lua_tostring(L, 1));
  if (n > 1) {
    m.mu_x = lua_todouble(L, 2);
    m.mu_y = m.mu_x;
  }
  if (n > 2)
    m.mu_y = lua_todouble(L, 3);
  if (n > 3)
    m.H_c = lua_todouble(L, 4);
  if (n > 4)
    m.Jsrc.re = lua_todouble(L, 5);
  if (n > 5)
    m.Jsrc.im = lua_todouble(L, 6);
  if (n > 6)
    m.Cduct = lua_todouble(L, 7);
  if (n > 7)
    m.Lam_d = lua_todouble(L, 8);
  if (n > 8)
    m.Theta_hn = lua_todouble(L, 9);
  if (n > 9)
    m.LamFill = lua_todouble(L, 10);
  if (n > 10)
    m.LamType = (int)lua_todouble(L, 11);
  if (n > 11) {
    m.Theta_hx = lua_todouble(L, 12);
    m.Theta_hy = lua_todouble(L, 13);
  } else {
    m.Theta_hx = m.Theta_hn;
    m.Theta_hy = m.Theta_hn;
  }
  if (n > 13) {
    m.NStrands = (int)lua_todouble(L, 14);
    m.WireD = lua_todouble(L, 15);
  }

  // do some sanity checking

  // shouldn't have a zero or negative permeability
  if (m.mu_x <= 0)
    m.mu_x = 1;
  if (m.mu_y <= 0)
    m.mu_y = 1;

  // checks for wire definitions
  if (m.LamType >= 3) {
    // should always have at least one strand if this is a wire
    if (m.NStrands <= 0)
      m.NStrands = 1;
  }

  ((CFemmeDoc*)pFemmeDoc)->blockproplist.Add(m);

  return 0;
}

int CFemmeDoc::old_lua_modmatprop(lua_State* L)
{
  CatchNullDocument();
  CString BlockName;
  int k, modprop;

  CFemmeDoc* thisDoc;
  CFemmeView* theView;
  thisDoc = (CFemmeDoc*)pFemmeDoc;
  POSITION pos;
  pos = thisDoc->GetFirstViewPosition();
  theView = (CFemmeView*)thisDoc->GetNextView(pos);

  // find the index of the material to modify;
  if (thisDoc->blockproplist.GetSize() == 0)
    return TRUE;
  BlockName.Format("%s", lua_tostring(L, 1));
  for (k = 0; k < thisDoc->blockproplist.GetSize(); k++)
    if (BlockName == thisDoc->blockproplist[k].BlockName)
      break;

  // get out of here if there's no matching material
  if (k == thisDoc->blockproplist.GetSize())
    return TRUE;

  modprop = (int)lua_todouble(L, 2);

  // now, modify the specified attribute...
  switch (modprop) {
  case 0:
    thisDoc->blockproplist[k].BlockName.Format("%s", lua_tostring(L, 3));
    break;
  case 1:
    thisDoc->blockproplist[k].mu_x = lua_todouble(L, 3);
    break;
  case 2:
    thisDoc->blockproplist[k].mu_y = lua_todouble(L, 3);
    break;
  case 3:
    thisDoc->blockproplist[k].H_c = lua_todouble(L, 3);
    break;
  case 4:
    thisDoc->blockproplist[k].Jsrc.re = lua_todouble(L, 3);
    break;
  case 5:
    thisDoc->blockproplist[k].Jsrc.im = lua_todouble(L, 3);
    break;
  case 6:
    thisDoc->blockproplist[k].Cduct = lua_todouble(L, 3);
    break;
  case 7:
    thisDoc->blockproplist[k].Lam_d = lua_todouble(L, 3);
    break;
  case 8:
    thisDoc->blockproplist[k].Theta_hn = lua_todouble(L, 3);
    break;
  case 9:
    thisDoc->blockproplist[k].LamFill = lua_todouble(L, 3);
    break;
  case 10:
    thisDoc->blockproplist[k].LamType = (int)lua_todouble(L, 3);
    break;
  case 11:
    thisDoc->blockproplist[k].Theta_hx = lua_todouble(L, 3);
    break;
  case 12:
    thisDoc->blockproplist[k].Theta_hy = lua_todouble(L, 3);
    break;
  case 13:
    thisDoc->blockproplist[k].NStrands = (int)lua_todouble(L, 3);
    break;
  case 14:
    thisDoc->blockproplist[k].WireD = lua_todouble(L, 4);
  default:
    break;
  }

  return 0;
}

int CFemmeDoc::old_lua_addpointprop(lua_State* L)
{
  CatchNullDocument();

  CPointProp m;
  int n = lua_gettop(L);

  if (n > 0)
    m.PointName.Format("%s", lua_tostring(L, 1));
  if (n > 1)
    m.Ap.re = lua_todouble(L, 2);
  if (n > 2)
    m.Ap.im = lua_todouble(L, 3);
  if (n > 3)
    m.Jp.re = lua_todouble(L, 4);
  if (n > 4)
    m.Jp.im = lua_todouble(L, 5);
  ((CFemmeDoc*)pFemmeDoc)->nodeproplist.Add(m);

  return 0;
}

int CFemmeDoc::old_lua_modpointprop(lua_State* L)
{
  CatchNullDocument();
  CString PointName;
  int k, modprop;

  CFemmeDoc* thisDoc;
  CFemmeView* theView;

  thisDoc = (CFemmeDoc*)pFemmeDoc;
  POSITION pos;
  pos = thisDoc->GetFirstViewPosition();
  theView = (CFemmeView*)thisDoc->GetNextView(pos);

  // find the index of the material to modify;
  if (thisDoc->nodeproplist.GetSize() == 0)
    return TRUE;
  PointName.Format("%s", lua_tostring(L, 1));
  for (k = 0; k < thisDoc->nodeproplist.GetSize(); k++)
    if (PointName == thisDoc->nodeproplist[k].PointName)
      break;

  // get out of here if there's no matching material
  if (k == thisDoc->nodeproplist.GetSize())
    return TRUE;

  modprop = (int)lua_todouble(L, 2);

  // now, modify the specified attribute...
  switch (modprop) {
  case 0:
    thisDoc->nodeproplist[k].PointName.Format("%s", lua_tostring(L, 3));
    break;
  case 1:
    thisDoc->nodeproplist[k].Ap.re = lua_todouble(L, 3);
    break;
  case 2:
    thisDoc->nodeproplist[k].Ap.im = lua_todouble(L, 3);
    break;
  case 3:
    thisDoc->nodeproplist[k].Jp.re = lua_todouble(L, 3);
    break;
  case 4:
    thisDoc->nodeproplist[k].Jp.im = lua_todouble(L, 3);
    break;
  default:
    break;
  }

  return 0;
}

int CFemmeDoc::old_lua_addcircuitprop(lua_State* L)
{
  CatchNullDocument();

  CCircuit m;
  int n = lua_gettop(L);

  if (n > 0)
    m.CircName = lua_tostring(L, 1);
  if (n > 1)
    m.Amps.re = lua_todouble(L, 2);
  if (n > 2)
    m.Amps.im = lua_todouble(L, 3);
  if (n > 3)
    m.CircType = (int)lua_todouble(L, 4);

  ((CFemmeDoc*)pFemmeDoc)->circproplist.Add(m);

  return 0;
}

int CFemmeDoc::old_lua_modcircprop(lua_State* L)
{
  CatchNullDocument();
  CString CircName;
  int k, modprop;

  CFemmeDoc* thisDoc;
  thisDoc = (CFemmeDoc*)pFemmeDoc;

  // find the index of the material to modify;
  if (thisDoc->circproplist.GetSize() == 0)
    return TRUE;
  CircName.Format("%s", lua_tostring(L, 1));
  for (k = 0; k < thisDoc->circproplist.GetSize(); k++)
    if (CircName == thisDoc->circproplist[k].CircName)
      break;

  // get out of here if there's no matching circuit
  if (k == thisDoc->circproplist.GetSize())
    return TRUE;

  modprop = (int)lua_todouble(L, 2);

  // now, modify the specified attribute...
  switch (modprop) {
  case 0:
    thisDoc->circproplist[k].CircName.Format("%s", lua_tostring(L, 3));
    break;
  case 1:
    thisDoc->circproplist[k].Amps.re = lua_todouble(L, 3);
    break;
  case 2:
    thisDoc->circproplist[k].Amps.im = lua_todouble(L, 3);
    break;
  case 3:
    thisDoc->circproplist[k].CircType = (int)lua_todouble(L, 3);
    break;
  default:
    break;
  }

  return 0;
}

int CFemmeDoc::lua_gettitle(lua_State* L)
{
  CatchNullDocument();
  CFemmeDoc* thisDoc;
  thisDoc = (CFemmeDoc*)pFemmeDoc;

  lua_pushstring(L, thisDoc->GetTitle());

  return 1;
}

int CFemmeDoc::lua_setgroup(lua_State* L)
{
  CatchNullDocument();
  CFemmeDoc* thisDoc;
  thisDoc = (CFemmeDoc*)pFemmeDoc;
  int grp, i;

  int n = lua_gettop(L);

  if (n > 0)
    grp = (int)lua_todouble(L, 1);
  else
    return 0;

  for (i = 0; i < thisDoc->nodelist.GetSize(); i++)
    if (thisDoc->nodelist[i].IsSelected == TRUE)
      thisDoc->nodelist[i].InGroup = grp;

  for (i = 0; i < thisDoc->linelist.GetSize(); i++)
    if (thisDoc->linelist[i].IsSelected == TRUE)
      thisDoc->linelist[i].InGroup = grp;

  for (i = 0; i < thisDoc->arclist.GetSize(); i++)
    if (thisDoc->arclist[i].IsSelected == TRUE)
      thisDoc->arclist[i].InGroup = grp;

  for (i = 0; i < thisDoc->blocklist.GetSize(); i++)
    if (thisDoc->blocklist[i].IsSelected == TRUE)
      thisDoc->blocklist[i].InGroup = grp;

  thisDoc->UnselectAll();

  return 0;
}

int CFemmeDoc::lua_getmaterial(lua_State* L)
{
  CatchNullDocument();
  CFemmeDoc* thisDoc;
  thisDoc = (CFemmeDoc*)pFemmeDoc;

  CString matname;
  int n = lua_gettop(L);

  if (n > 0)
    matname = lua_tostring(L, 1);
  else
    return 0;

  // Modified by Claude (Anthropic), noreply@anthropic.com, 2026-09-12:
  // optional second argument, a folder name, to disambiguate duplicate
  // material names (issue #34).
  //
  // matlib.dat ships two DIFFERENT materials both called "Supermalloy" --
  // one in Nickel Alloys with mu_r 529095, one in Metals Handbook DC
  // Magnetization Curves with mu_r 1 -- and this function matched on name
  // alone, first in file order. So the Metals Handbook entry could not be
  // selected from a script at all, and a script asking for "Supermalloy"
  // silently got the other one. heatlib.dat has the same collision on
  // "Ammonia": liquid at k=0.546 and gas at k=0.0153, a factor of 36
  // apart. The GUI's material browser disambiguates by folder; scripting
  // had no way to.
  //
  // Deliberately additive rather than a rename. Renaming an entry in a
  // library users' existing models already reference by name would make
  // some of those models silently resolve to the other material, which is
  // the very failure being fixed. With one argument the behaviour is
  // unchanged, down to which duplicate wins.
  CString foldername;
  if (n > 1)
    foldername = lua_tostring(L, 2);

  CString LibName = thisDoc->BinDir + "matlib.dat";

  FILE* fp;
  int i, j, k;
  char s[1024], q[1024];
  char* v;

  CMaterialProp MProp;

  if ((fp = fopen(LibName, "rt")) == NULL) {
    CString msg;
    msg.Format("Couldn't open %s", LibName);
    lua_error(L, msg.GetBuffer(1));
    return FALSE;
  }

  // parse the file
  // Tracks which folder of the library tree the parser is inside,
  // so the optional folder argument can pick between two entries
  // that share a name (issue #34).
  CStringArray FolderStack;

  while (fgets(s, 1024, fp) != NULL) {
    if (sscanf(s, "%s", q) == EOF)
      q[0] = NULL;

    if (TrackMaterialFolder(q, s, FolderStack)) {
      q[0] = NULL;
      continue;
    }

    // Block Properties;
    if (_strnicmp(q, "<beginblock>", 12) == 0) {
      MProp.BlockName = "New Material";
      MProp.mu_x = 1.;
      MProp.mu_y = 1.; // permeabilities, relative
      MProp.H_c = 0.; // magnetization, A/m
      MProp.Jsrc = 0; // applied current density, MA/m^2
      MProp.Cduct = 0.; // conductivity of the material, MS/m
      MProp.Lam_d = 0.; // lamination thickness, mm
      MProp.Theta_hn = 0.; // hysteresis angle, degrees
      MProp.Theta_hx = 0.;
      MProp.Theta_hy = 0.;
      MProp.LamFill = 1.; // lamination fill factor;
      MProp.LamType = 0; // type of lamination;
      MProp.NStrands = 0;
      MProp.WireD = 0;
      MProp.BHpoints = 0;
      MProp.BHdata = NULL;
      q[0] = NULL;
    }

    if (_strnicmp(q, "<blockname>", 10) == 0) {
      v = StripKey(s);
      k = (int)strlen(v);
      for (i = 0; i < k; i++)
        if (v[i] == '\"') {
          v = v + i + 1;
          i = k;
        }
      k = (int)strlen(v);
      if (k > 0)
        for (i = k - 1; i >= 0; i--) {
          if (v[i] == '\"') {
            v[i] = 0;
            i = -1;
          }
        }
      MProp.BlockName = v;
      q[0] = NULL;
    }

    if (_strnicmp(q, "<mu_x>", 6) == 0) {
      v = StripKey(s);
      sscanf(v, "%lf", &MProp.mu_x);
      q[0] = NULL;
    }

    if (_strnicmp(q, "<mu_y>", 6) == 0) {
      v = StripKey(s);
      sscanf(v, "%lf", &MProp.mu_y);
      q[0] = NULL;
    }

    if (_strnicmp(q, "<H_c>", 5) == 0) {
      v = StripKey(s);
      sscanf(v, "%lf", &MProp.H_c);
      q[0] = NULL;
    }

    if (_strnicmp(q, "<J_re>", 6) == 0) {
      v = StripKey(s);
      sscanf(v, "%lf", &MProp.Jsrc.re);
      q[0] = NULL;
    }

    if (_strnicmp(q, "<J_im>", 6) == 0) {
      v = StripKey(s);
      sscanf(v, "%lf", &MProp.Jsrc.im);
      q[0] = NULL;
    }

    if (_strnicmp(q, "<sigma>", 7) == 0) {
      v = StripKey(s);
      sscanf(v, "%lf", &MProp.Cduct);
      q[0] = NULL;
    }

    if (_strnicmp(q, "<phi_h>", 7) == 0) {
      v = StripKey(s);
      sscanf(v, "%lf", &MProp.Theta_hn);
      q[0] = NULL;
    }

    if (_strnicmp(q, "<phi_hx>", 8) == 0) {
      v = StripKey(s);
      sscanf(v, "%lf", &MProp.Theta_hx);
      q[0] = NULL;
    }

    if (_strnicmp(q, "<phi_hy>", 8) == 0) {
      v = StripKey(s);
      sscanf(v, "%lf", &MProp.Theta_hy);
      q[0] = NULL;
    }

    if (_strnicmp(q, "<d_lam>", 7) == 0) {
      v = StripKey(s);
      sscanf(v, "%lf", &MProp.Lam_d);
      q[0] = NULL;
    }

    if (_strnicmp(q, "<LamFill>", 8) == 0) {
      v = StripKey(s);
      sscanf(v, "%lf", &MProp.LamFill);
      q[0] = NULL;
    }

    if (_strnicmp(q, "<LamType>", 9) == 0) {
      v = StripKey(s);
      sscanf(v, "%i", &MProp.LamType);
      q[0] = NULL;
    }

    if (_strnicmp(q, "<NStrands>", 10) == 0) {
      v = StripKey(s);
      sscanf(v, "%i", &MProp.NStrands);
      q[0] = NULL;
    }

    if (_strnicmp(q, "<WireD>", 7) == 0) {
      v = StripKey(s);
      sscanf(v, "%lf", &MProp.WireD);
      q[0] = NULL;
    }

    if (_strnicmp(q, "<BHPoints>", 10) == 0) {
      v = StripKey(s);
      sscanf(v, "%i", &MProp.BHpoints);
      if (MProp.BHpoints > 0) {
        MProp.BHdata = (CComplex*)calloc(MProp.BHpoints, sizeof(CComplex));
        for (j = 0; j < MProp.BHpoints; j++) {
          fgets(s, 1024, fp);
          sscanf(s, "%lf	%lf", &MProp.BHdata[j].re, &MProp.BHdata[j].im);
        }
      }
      q[0] = NULL;
    }

    if (_strnicmp(q, "<endblock>", 9) == 0) {
      // See the foldername note at the top of this function (issue #34).
      // With no folder argument this is exactly the old condition.
      if (MProp.BlockName == matname
          && (foldername.IsEmpty() || InFolder(FolderStack, foldername))) {
        thisDoc->blockproplist.Add(MProp);
        MProp.BHpoints = 0;
        fclose(fp);
        return 0;
      } else {
        free(MProp.BHdata);
        MProp.BHdata = NULL;
        MProp.BHpoints = 0;
      }
      q[0] = NULL;
    }
  }

  fclose(fp);

  CString msg;
  msg.Format("Couldn't load \"%s\" from the materials library", matname);
  lua_error(L, msg.GetBuffer(1));
  return FALSE;
}

int CFemmeDoc::lua_attachdefault(lua_State* L)
{
  CatchNullDocument();
  CFemmeDoc* thisDoc;
  thisDoc = (CFemmeDoc*)pFemmeDoc;

  for (int i = 0, j = 0; i < thisDoc->blocklist.GetSize(); i++) {
    if ((thisDoc->blocklist[i].IsSelected == TRUE) && (j == 0)) {
      thisDoc->blocklist[i].IsDefault = 2;
      j++;
    } else
      thisDoc->blocklist[i].IsDefault = FALSE;
  }

  return 0;
}

int CFemmeDoc::lua_getprobleminfo(lua_State* L)
{
  CatchNullDocument();
  CFemmeDoc* thisDoc;
  thisDoc = (CFemmeDoc*)pFemmeDoc;

  lua_pushnumber(L, thisDoc->ProblemType);
  lua_pushnumber(L, thisDoc->Frequency);
  lua_pushnumber(L, thisDoc->Depth);
  switch (thisDoc->LengthUnits) {
  case 1: // mm
    lua_pushnumber(L, 0.001);
    break;
  case 2: // cm
    lua_pushnumber(L, 0.01);
    break;
  case 3: // m
    lua_pushnumber(L, 1.0);
    break;
  case 4: // mils
    lua_pushnumber(L, 2.54e-05);
    break;
  case 5: // um
    lua_pushnumber(L, 1.0e-06);
    break;
  default: // inches
    lua_pushnumber(L, 0.0254);
    break;
  }

  return 4;
}

int CFemmeDoc::lua_getboundingbox(lua_State* L)
{
  CatchNullDocument();
  CFemmeDoc* thisDoc;
  CFemmeView* theView;

  thisDoc = (CFemmeDoc*)pFemmeDoc;
  POSITION pos;
  pos = thisDoc->GetFirstViewPosition();
  theView = (CFemmeView*)thisDoc->GetNextView(pos);

  double x[2], y[2];
  if (theView->GetBoundingBox(x, y)) {
    lua_pushnumber(L, x[0]);
    lua_pushnumber(L, x[1]);
    lua_pushnumber(L, y[0]);
    lua_pushnumber(L, y[1]);
    return 4;
  } else
    return 0;
}

int CFemmeDoc::lua_detachdefault(lua_State* L)
{
  CatchNullDocument();
  CFemmeDoc* thisDoc;
  thisDoc = (CFemmeDoc*)pFemmeDoc;

  for (int i = 0; i < thisDoc->blocklist.GetSize(); i++)
    if (thisDoc->blocklist[i].IsSelected == TRUE)
      thisDoc->blocklist[i].IsDefault = FALSE;

  return 0;
}

int CFemmeDoc::lua_selectcircle(lua_State* L)
{
  CatchNullDocument();
  CFemmeDoc* pDoc;
  CFemmeView* theView;

  pDoc = (CFemmeDoc*)pFemmeDoc;
  POSITION pos;
  pos = pDoc->GetFirstViewPosition();
  theView = (CFemmeView*)pDoc->GetNextView(pos);

  int i, k, n, EditAction;
  double R;
  CComplex c, q;

  n = lua_gettop(L);
  if (n < 3)
    return 0;
  c = lua_tonumber(L, 1) + I * lua_tonumber(L, 2);
  R = lua_todouble(L, 3);
  if (n > 3)
    EditAction = (int)lua_todouble(L, 4);
  else
    EditAction = theView->EditAction;
  if ((EditAction > 4) || (EditAction < 0))
    return 0;

  if ((EditAction == 0) || (EditAction == 4)) {
    for (i = 0; i < pDoc->nodelist.GetSize(); i++) {
      q = pDoc->nodelist[i].CC();
      if (abs(q - c) <= R)
        pDoc->nodelist[i].IsSelected = TRUE;
    }
  }

  if ((EditAction == 2) || (EditAction == 4)) {
    for (i = 0; i < pDoc->blocklist.GetSize(); i++) {
      q = pDoc->blocklist[i].x + I * pDoc->blocklist[i].y;
      if (abs(q - c) <= R)
        pDoc->blocklist[i].IsSelected = TRUE;
    }
  }

  if ((EditAction == 1) || (EditAction == 4)) {
    for (i = 0; i < pDoc->linelist.GetSize(); i++) {

      k = 0;
      q = pDoc->nodelist[pDoc->linelist[i].n0].CC();
      if (abs(q - c) <= R)
        k++;
      q = pDoc->nodelist[pDoc->linelist[i].n1].CC();
      if (abs(q - c) <= R)
        k++;

      if (k == 2)
        pDoc->linelist[i].IsSelected = TRUE;
    }
  }

  if ((EditAction == 3) || (EditAction == 4)) {
    for (i = 0; i < pDoc->arclist.GetSize(); i++) {
      k = 0;
      q = pDoc->nodelist[pDoc->arclist[i].n0].CC();
      if (abs(q - c) <= R)
        k++;
      q = pDoc->nodelist[pDoc->arclist[i].n1].CC();
      if (abs(q - c) <= R)
        k++;

      if (k == 2)
        pDoc->arclist[i].IsSelected = TRUE;
    }
  }

  theView->InvalidateRect(NULL);
  return 0;
}

int CFemmeDoc::lua_selectrectangle(lua_State* L)
{
  CatchNullDocument();
  CFemmeDoc* pDoc;
  CFemmeView* theView;

  pDoc = (CFemmeDoc*)pFemmeDoc;
  POSITION pos;
  pos = pDoc->GetFirstViewPosition();
  theView = (CFemmeView*)pDoc->GetNextView(pos);

  int i, k, n, EditAction;
  double mx, my, wzx, wzy, x, y, z;

  n = lua_gettop(L);
  if (n < 4)
    return 0;
  mx = lua_todouble(L, 1);
  my = lua_todouble(L, 2);
  wzx = lua_todouble(L, 3);
  wzy = lua_todouble(L, 4);
  if (n > 4)
    EditAction = (int)lua_todouble(L, 5);
  else
    EditAction = theView->EditAction;
  if ((EditAction > 4) || (EditAction < 0))
    return 0;

  if (mx < wzx) {
    z = wzx;
    wzx = mx;
    mx = z;
  }
  if (my < wzy) {
    z = wzy;
    wzy = my;
    my = z;
  }

  if ((EditAction == 0) || (EditAction == 4)) {
    for (i = 0; i < pDoc->nodelist.GetSize(); i++) {
      x = pDoc->nodelist[i].x;
      y = pDoc->nodelist[i].y;
      if ((x <= mx) && (x >= wzx) && (y <= my) && (y >= wzy))
        pDoc->nodelist[i].IsSelected = TRUE;
    }
  }

  if ((EditAction == 2) || (EditAction == 4)) {
    for (i = 0; i < pDoc->blocklist.GetSize(); i++) {
      x = pDoc->blocklist[i].x;
      y = pDoc->blocklist[i].y;
      if ((x <= mx) && (x >= wzx) && (y <= my) && (y >= wzy))
        pDoc->blocklist[i].IsSelected = TRUE;
    }
  }

  if ((EditAction == 1) || (EditAction == 4)) {
    for (i = 0; i < pDoc->linelist.GetSize(); i++) {
      k = 0;
      x = pDoc->nodelist[pDoc->linelist[i].n0].x;
      y = pDoc->nodelist[pDoc->linelist[i].n0].y;
      if ((x <= mx) && (x >= wzx) && (y <= my) && (y >= wzy))
        k++;
      x = pDoc->nodelist[pDoc->linelist[i].n1].x;
      y = pDoc->nodelist[pDoc->linelist[i].n1].y;
      if ((x <= mx) && (x >= wzx) && (y <= my) && (y >= wzy))
        k++;

      if (k == 2)
        pDoc->linelist[i].IsSelected = TRUE;
    }
  }

  if ((EditAction == 3) || (EditAction == 4)) {
    for (i = 0; i < pDoc->arclist.GetSize(); i++) {
      k = 0;
      x = pDoc->nodelist[pDoc->arclist[i].n0].x;
      y = pDoc->nodelist[pDoc->arclist[i].n0].y;
      if ((x <= mx) && (x >= wzx) && (y <= my) && (y >= wzy))
        k++;
      x = pDoc->nodelist[pDoc->arclist[i].n1].x;
      y = pDoc->nodelist[pDoc->arclist[i].n1].y;
      if ((x <= mx) && (x >= wzx) && (y <= my) && (y >= wzy))
        k++;

      if (k == 2)
        pDoc->arclist[i].IsSelected = TRUE;
    }
  }

  theView->InvalidateRect(NULL);
  return 0;
}
