SpgV0/femmx/femm/femmviewLua.cpp

#include "stdafx.h"
#include "BitmapCapture.h"
#include "ScriptGui.h"
#include <afx.h>
#include <afxtempl.h>
#include "problem.h"
#include "femm.h"
#include "xyplot.h"
#include "femmviewDoc.h"
#include "femmviewview.h"
#include "MainFrm.h"
#include "windows.h" //necessary for bitmap saving
#include "lua.h"
#include "mycommandlineinfo.h"
#include "promptbox.h"
#include "ChildFrm.h"

#ifdef _DEBUG
#define new DEBUG_NEW
#undef THIS_FILE
static char THIS_FILE[] = __FILE__;
#endif

extern lua_State* lua;
extern BOOL bLinehook;
extern void* pFemmviewdoc;
extern CLuaConsoleDlg* LuaConsole;
extern BOOL lua_byebye;
extern int m_luaWindowStatus;

#define CatchNullDocument()                       \
  ;                                               \
  if (pFemmviewdoc == NULL) {                     \
    CString msg = "No magnetics output in focus"; \
    lua_error(L, msg.GetBuffer(1));               \
    return 0;                                     \
  }

//-------------------Lua Extensions-------------------------

void CFemmviewDoc::initalise_lua()
{
  // use a messagebox to display errors
  lua_register(lua, "mo_setfocus", lua_switchfocus);
  lua_register(lua, "mo_getpointvalues", lua_getpointvals);
  lua_register(lua, "mo_close", lua_exitpost);
  lua_register(lua, "mo_addcontour", lua_addcontour);
  lua_register(lua, "mo_clearcontour", lua_clearcontour);
  lua_register(lua, "mo_lineintegral", lua_lineintegral);
  lua_register(lua, "mo_selectblock", lua_selectblock);
  lua_register(lua, "mo_groupselectblock", lua_groupselectblock);
  lua_register(lua, "mo_clearblock", lua_clearblock);
  lua_register(lua, "mo_blockintegral", lua_blockintegral);
  lua_register(lua, "mo_zoomnatural", lua_zoomnatural);
  lua_register(lua, "mo_zoomin", lua_zoomin);
  lua_register(lua, "mo_zoomout", lua_zoomout);
  lua_register(lua, "mo_zoom", lua_zoom);
  lua_register(lua, "mo_showgrid", lua_showgrid);
  lua_register(lua, "mo_hidegrid", lua_hidegrid);
  lua_register(lua, "mo_gridsnap", lua_gridsnap);
  lua_register(lua, "mo_setgrid", lua_setgrid);
  lua_register(lua, "mo_showmesh", lua_showmesh);
  lua_register(lua, "mo_hidemesh", lua_hidemesh);
  lua_register(lua, "mo_hidedensityplot", lua_hidedensity);
  lua_register(lua, "mo_showdensityplot", lua_showdensity);
  lua_register(lua, "mo_hidecontourplot", lua_hidecountour);
  lua_register(lua, "mo_showcontourplot", lua_showcountour);
  lua_register(lua, "mo_showvectorplot", lua_vectorplot);
  lua_register(lua, "mo_smooth", lua_smoothing);
  lua_register(lua, "mo_showpoints", lua_showpoints);
  lua_register(lua, "mo_hidepoints", lua_hidepoints);
  lua_register(lua, "mo_shownames", lua_shownames);
  lua_register(lua, "mo_getprobleminfo", lua_getprobleminfo);
  lua_register(lua, "mo_savebitmap", lua_savebitmap);
  lua_register(lua, "mo_savepng", lua_savepng);
  lua_register(lua, "mo_save_png", lua_savepng);
  lua_register(lua, "mo_getcircuitproperties", lua_getcircuitprops);
  lua_register(lua, "mo_savemetafile", lua_saveWMF);
  lua_register(lua, "mo_refreshview", lua_refreshview);
  lua_register(lua, "mo_selectpoint", lua_selectline);
  lua_register(lua, "mo_seteditmode", lua_seteditmode);
  lua_register(lua, "mo_bendcontour", lua_bendcontour);
  lua_register(lua, "mo_makeplot", lua_makeplot);
  lua_register(lua, "mo_reload", lua_reload);
  lua_register(lua, "mo_gradient", lua_gradient);
  lua_register(lua, "mo_gettitle", lua_gettitle);
  lua_register(lua, "mo_get_title", lua_gettitle);
  lua_register(lua, "mo_set_weighting_scheme", lua_weighting);
  lua_register(lua, "mo_setweightingscheme", lua_weighting);

  lua_register(lua, "mo_resize", luaResize);
  lua_register(lua, "mo_minimize", luaMinimize);
  lua_register(lua, "mo_maximize", luaMaximize);
  lua_register(lua, "mo_restore", luaRestore);

  // compatibility with alternate lua function naming convention
  lua_register(lua, "mo_set_focus", lua_switchfocus);
  lua_register(lua, "mo_get_point_values", lua_getpointvals);
  lua_register(lua, "mo_add_contour", lua_addcontour);
  lua_register(lua, "mo_clear_contour", lua_clearcontour);
  lua_register(lua, "mo_line_integral", lua_lineintegral);
  lua_register(lua, "mo_select_block", lua_selectblock);
  lua_register(lua, "mo_group_select_block", lua_groupselectblock);
  lua_register(lua, "mo_clear_block", lua_clearblock);
  lua_register(lua, "mo_block_integral", lua_blockintegral);
  lua_register(lua, "mo_zoom_natural", lua_zoomnatural);
  lua_register(lua, "mo_zoom_in", lua_zoomin);
  lua_register(lua, "mo_zoom_out", lua_zoomout);
  lua_register(lua, "mo_show_grid", lua_showgrid);
  lua_register(lua, "mo_hide_grid", lua_hidegrid);
  lua_register(lua, "mo_show_mesh", lua_showmesh);
  lua_register(lua, "mo_hide_mesh", lua_hidemesh);
  lua_register(lua, "mo_hide_density_plot", lua_hidedensity);
  lua_register(lua, "mo_show_density_plot", lua_showdensity);
  lua_register(lua, "mo_hide_contour_plot", lua_hidecountour);
  lua_register(lua, "mo_show_contour_plot", lua_showcountour);
  lua_register(lua, "mo_show_vector_plot", lua_vectorplot);
  lua_register(lua, "mo_show_points", lua_showpoints);
  lua_register(lua, "mo_hide_points", lua_hidepoints);
  lua_register(lua, "mo_grid_snap", lua_gridsnap);
  lua_register(lua, "mo_set_grid", lua_setgrid);
  lua_register(lua, "mo_get_problem_info", lua_getprobleminfo);
  lua_register(lua, "mo_save_bitmap", lua_savebitmap);
  lua_register(lua, "mo_get_circuit_properties", lua_getcircuitprops);
  lua_register(lua, "mo_save_metafile", lua_saveWMF);
  lua_register(lua, "mo_refresh_view", lua_refreshview);
  lua_register(lua, "mo_select_point", lua_selectline);
  lua_register(lua, "mo_set_edit_mode", lua_seteditmode);
  lua_register(lua, "mo_bend_contour", lua_bendcontour);
  lua_register(lua, "mo_make_plot", lua_makeplot);
  lua_register(lua, "mo_show_names", lua_shownames);
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
